pfanchri/Bachelorarbeit/Latex/Bachelorarbeit/Abschnitte/Anhang/Schaltplaene.tex

\section{Schaltpläne}
\label{app:Schematics}
Auf den folgenden Seiten sind die in Altium Designer erstellten Schaltpläne für alle Baugruppen der Basisstation dargestellt. Außerdem ist das \ac{PCB}-Layout der Basisstation abgebildet.

\includepdf[landscape, pages=-]{"../../Altium/mobile Basisstation/Project Outputs for mobile Basisstation/Basisstation Schematics"} 

\includepdf[landscape, pages=11]{"Abbildungen/Aufnahmen/SmartPDF/mobile Basisstation"}
