pfanchri/Bachelorarbeit/Präsentation/Präsentation PDF Export.pdf

# Au#au und Inbetriebnahme einer mobilen Basissta4on für feldstärkebasierte Lokalisierung

# Christof Pfannenmüller

07.10.2016

# Übersicht

# •Motivation •Anforderungen •Platinenlayout

# - Transceiver TDA 5340 - Mikrocontroller XMC4500

# •SoIwareentwurf •Datenausgabe und Tests

# Mo4va4on

# - ernergiesparende Lösung zur Lokalisierung - relative Ortung zu mobiler Basisstation - Anwendung innerhalb von Gebäuden - Sub-GHz-Band - Lokalisierung auf RSSI-Basis - Nutzung bereitgestellter Daten

# Anforderungen

# Anforderungen

# - sechs unabhängige Transceiver - Mikrocontroller zur Steuerung - Spannungsversorgung - Ausgabe ( USB & Ethernet ) - interruptbasierte Steuerung - Kommunikation über SPI-Interface

# Pla4nenlayout

# Mikrocontroller XMC4500

# - ARM® CortexTM-M4

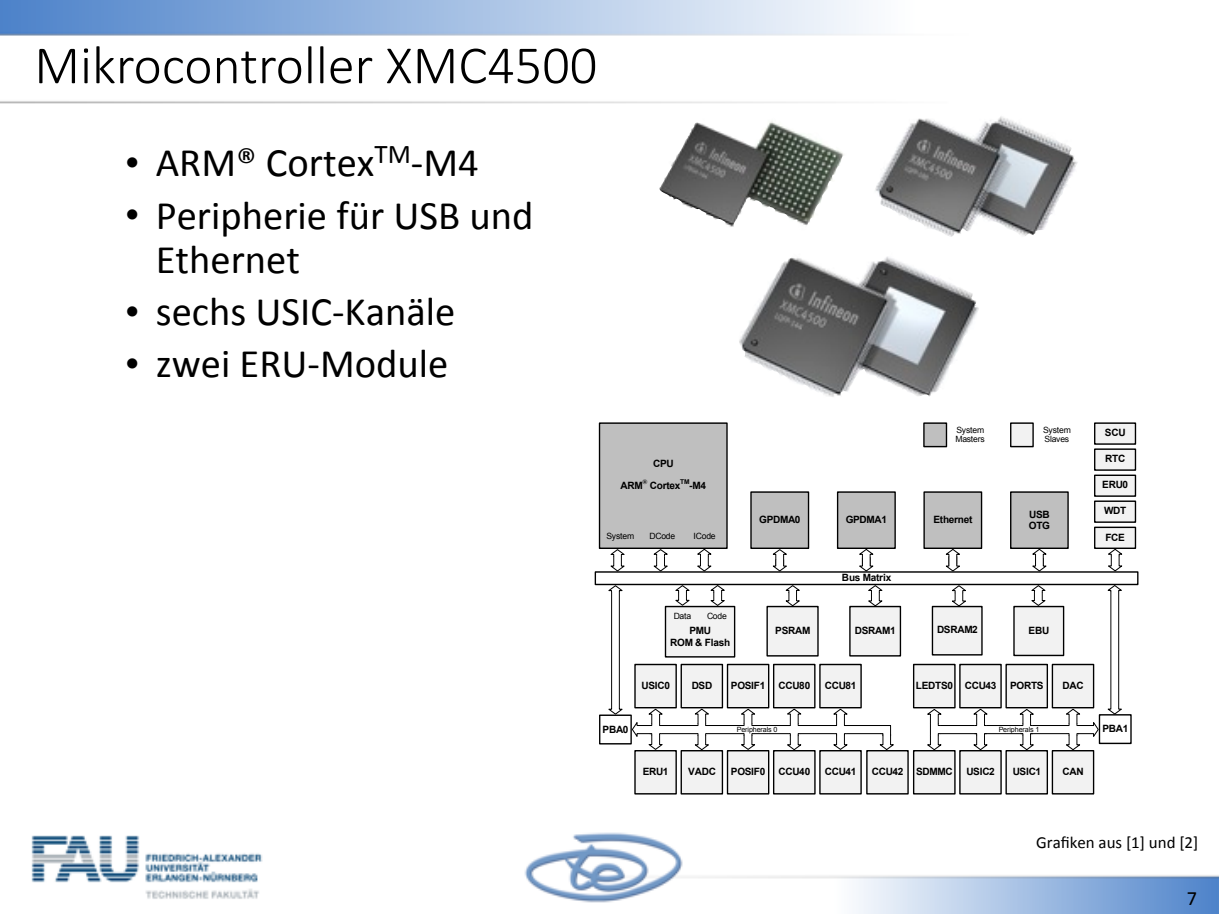
[picture p25: page 7]
PMU ROM & Flash; Bus Matrix; CPU; ARM® CortexTM-M4; PSRAM; DSRAM1; DSRAM2; EBU; FCE; GPDMA0; GPDMA1; USB; OTG Ethernet; System; ICode DCode; PBA0; Peripherals 0; Peripherals 1; Data; Code; WDT; RTC; ERU0; SCU; ERU1; VADC; POSIF0 CCU40; CCU41; CCU42; USIC0; DSD; POSIF1 CCU80; CCU81; LEDTS0 CCU43; PORTS; DAC; SDMMC; USIC2; USIC1; CAN; System Masters; System Slaves; PBA1

• Peripherie für USB und
Ethernet
• sechs USIC-Kanäle
• zwei ERU-Module

Grafiken aus [1] und [2]

# Schaltplan Mikrocontroller 1

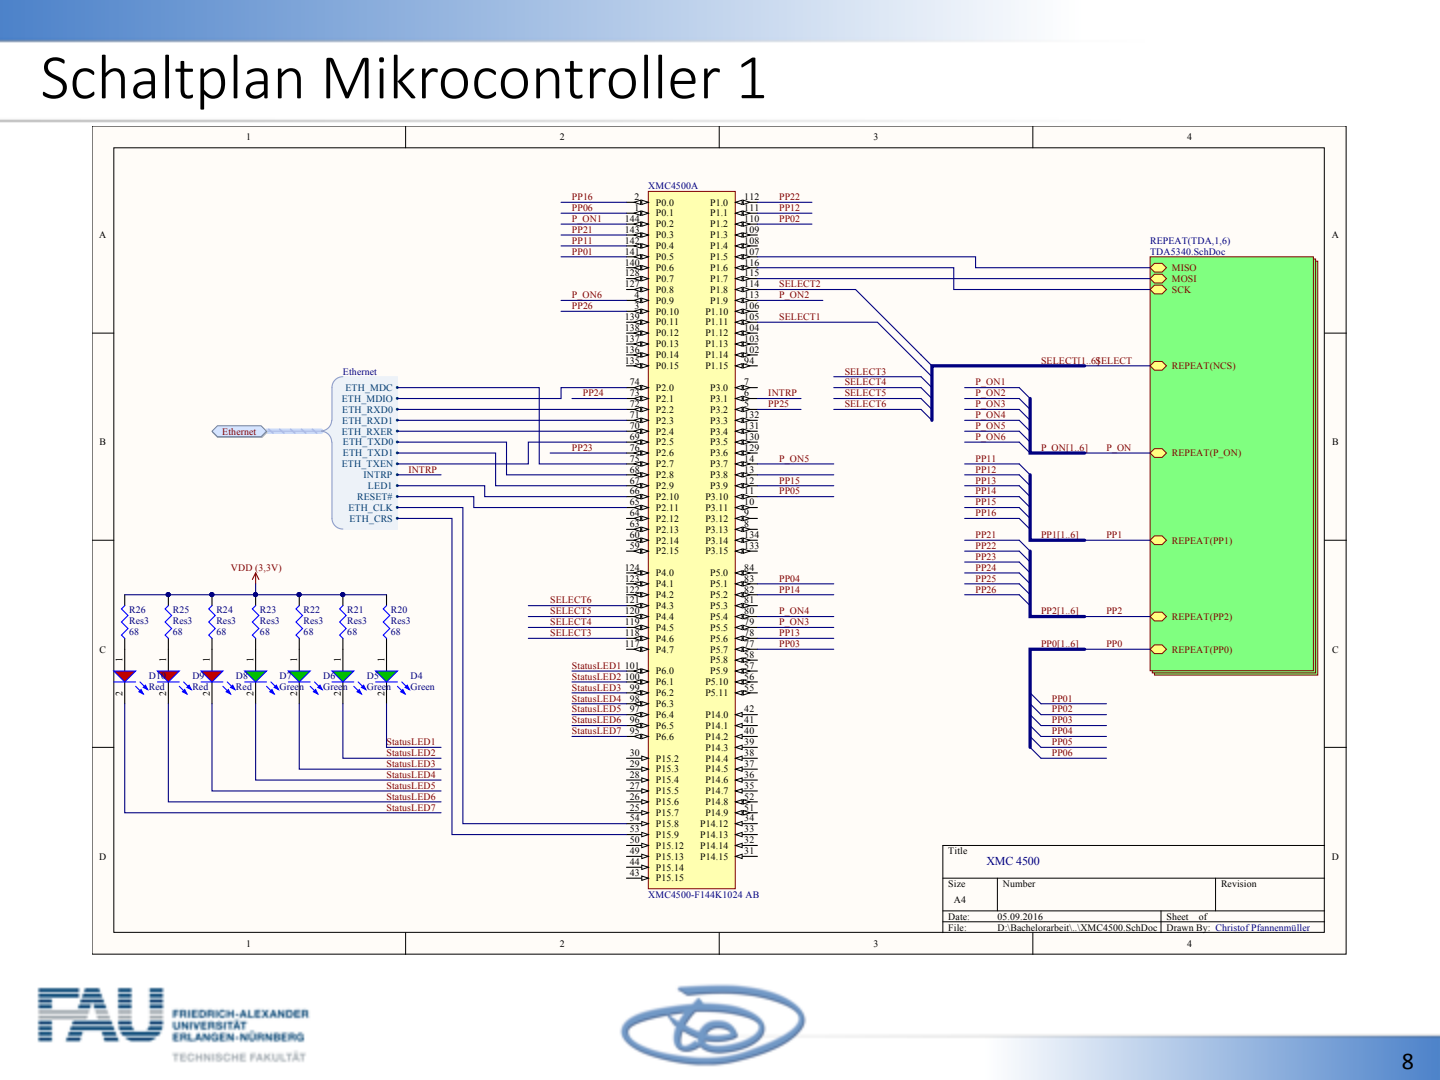
[picture p26: page 8]

# Schaltplan Mikrocontroller 2

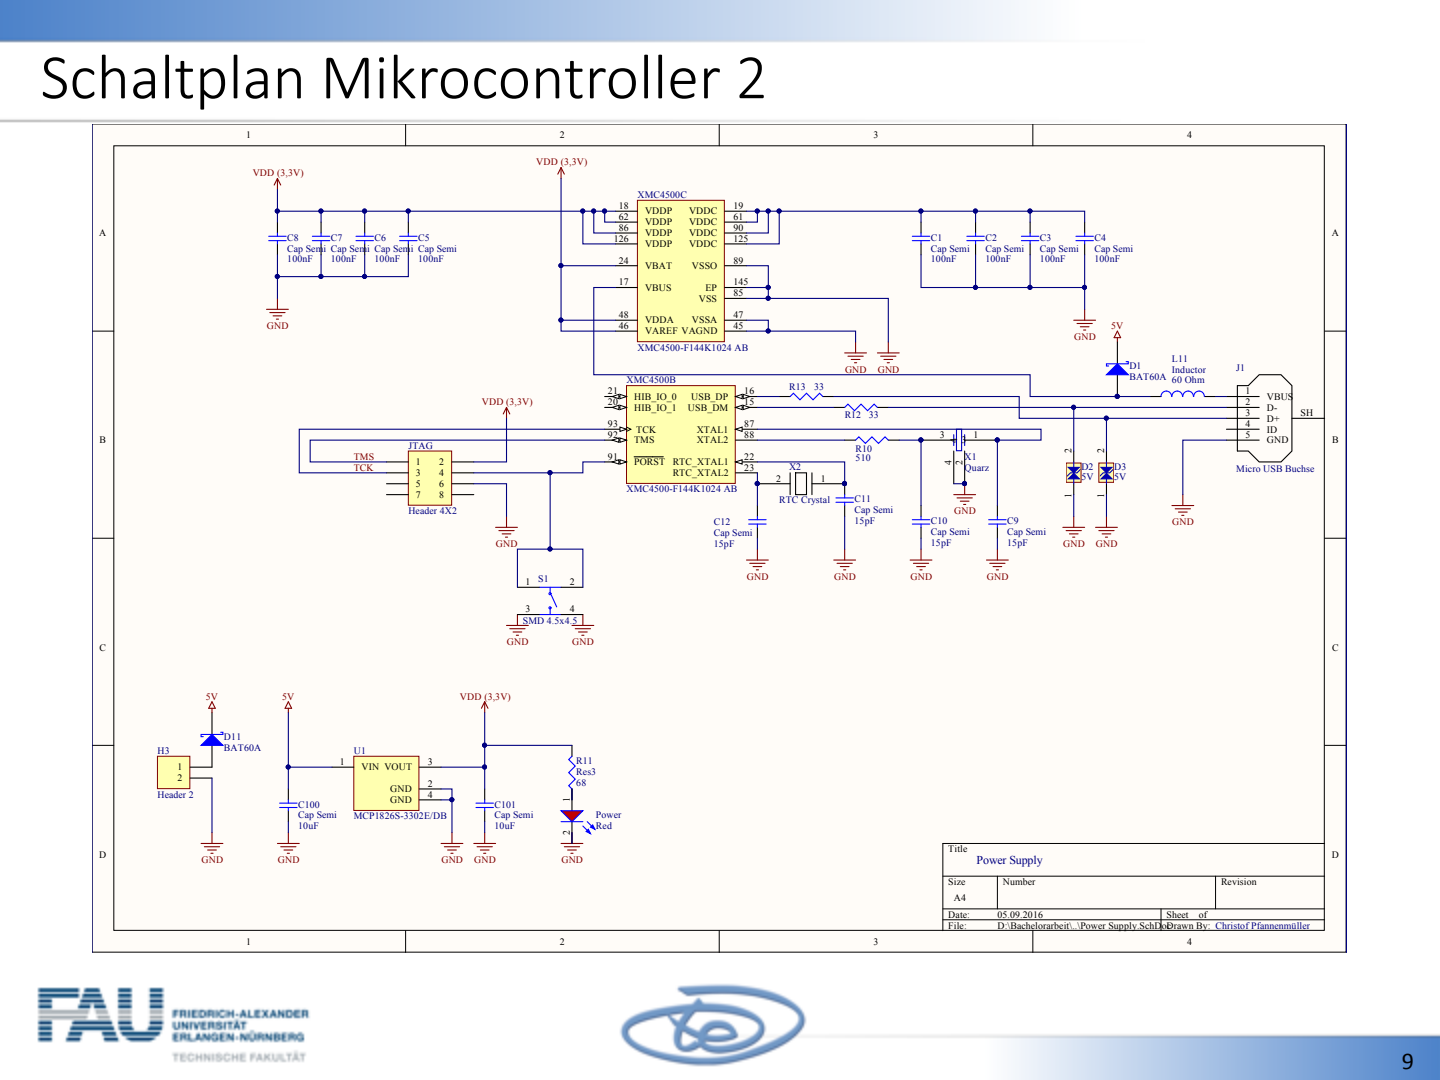
[picture p27: page 9]

# Transceiver TDA5340

# - Basisbanddemodulation

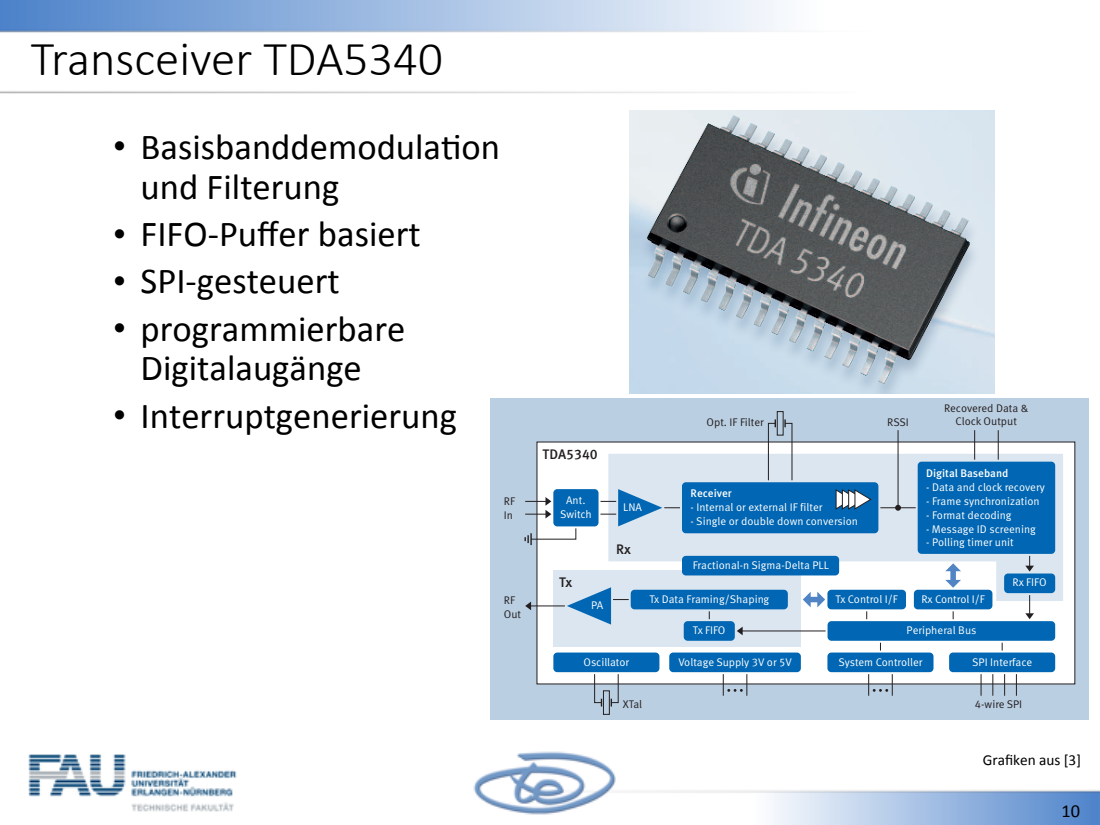
[picture p28: page 10]
Grafiken aus [3]; LNA; TDA5340; Ant. Switch; Rx FIFO; Tx FIFO; Peripheral Bus; Tx Data Framing/Shaping; Tx Control I/F; Oscillator; Voltage Supply 3V or 5V; System Controller; XTal; 4-wire SPI; Opt. IF Filter; RSSI; Recovered Data & Clock Output; RF Out; SPI Interface; Rx Control I/F

und Filterung
• FIFO-Puffer basiert
• SPI-gesteuert
• programmierbare
Digitalaugänge
• Interruptgenerierung

Digital Baseband
- Data and clock recovery
- Frame synchronization
- Format decoding
- Message ID screening
- Polling timer unit

Receiver
- Internal or external IF filter
- Single or double down conversion

Fractional-n Sigma-Delta PLL

# Schaltplan Transceiver

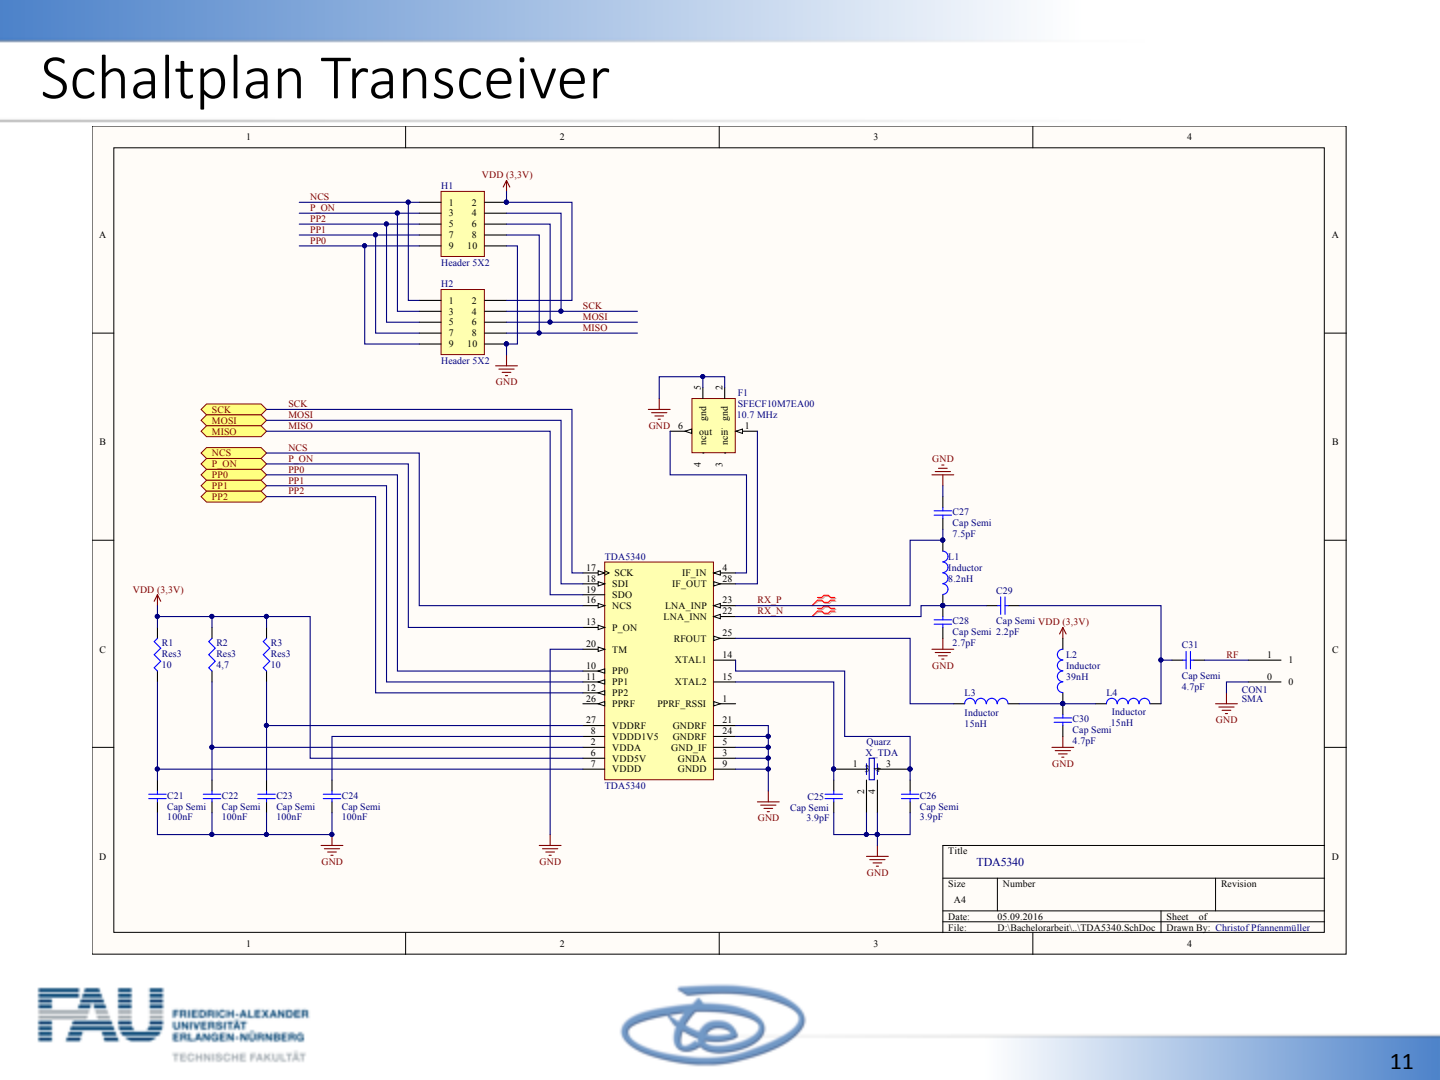
[picture p29: page 11]

# Layout Basissta4on

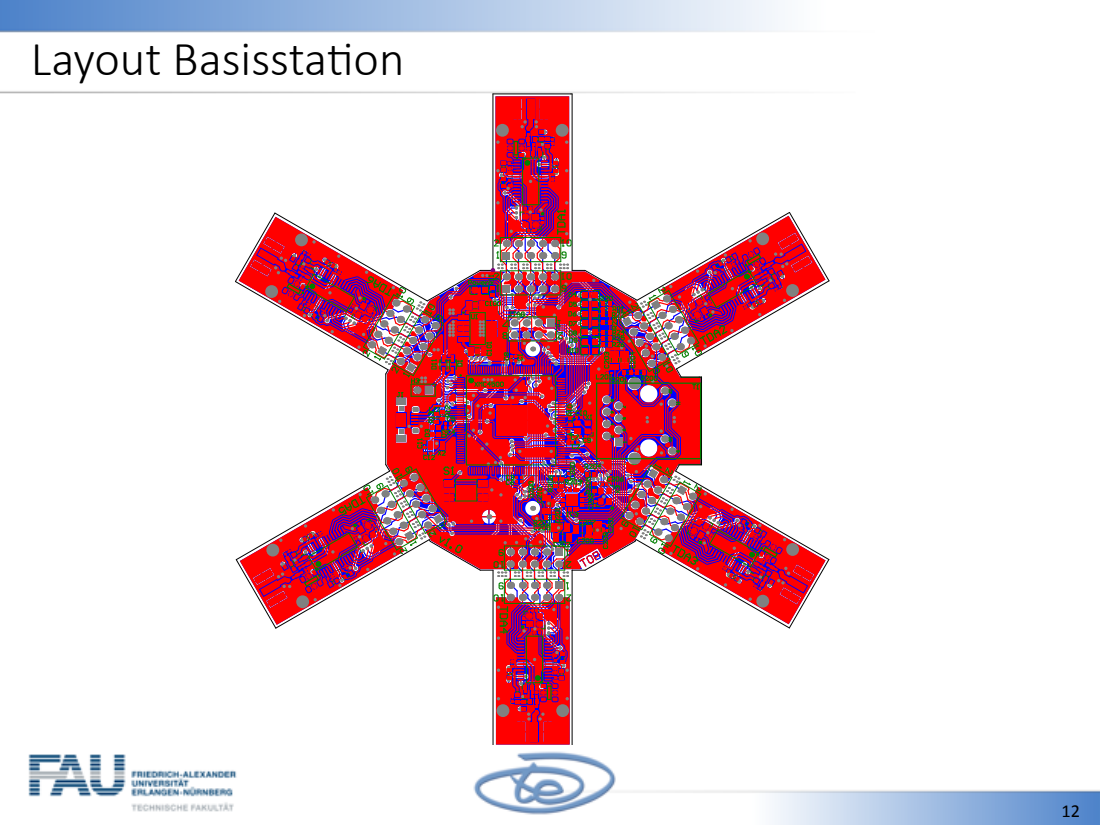
[picture p30: page 12]

# Layout XMC4500

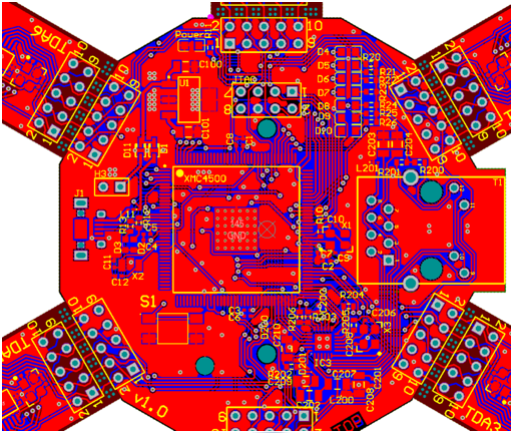
[picture p31: figure]

# Layout Transceiver

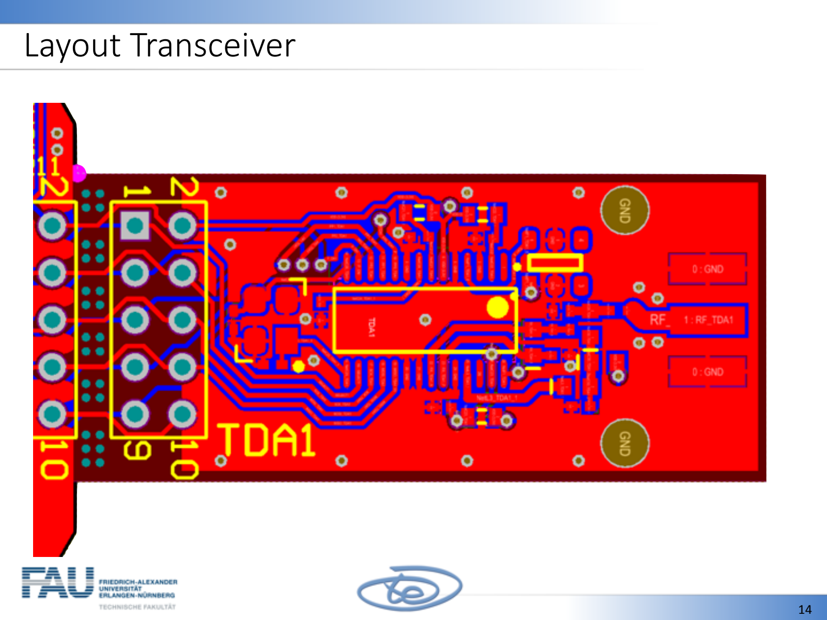
[picture p32: page 14]

# Bestückung

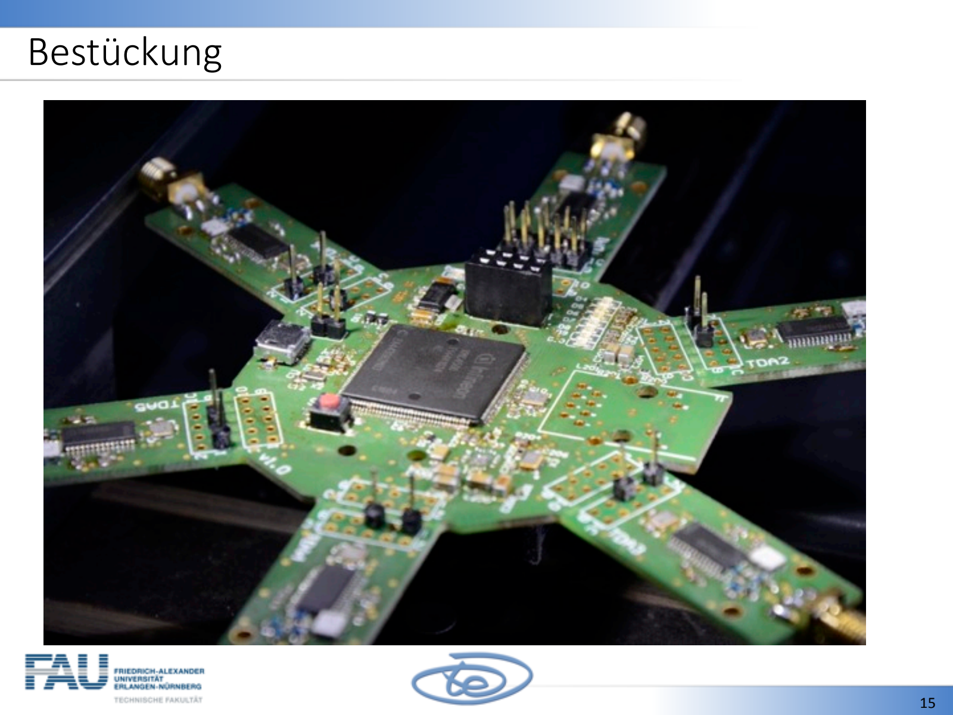
[picture p33: page 15]

# SoMwareentwurf

# Datenausgabe und Feldtest

# Vielen Dank für Ihre Aufmerksamkeit!

# Literatur

[1] P. Bauer, P. Schäfer und S. Zizala, New Infineon 32-bit Microcontroller Family XMC4000 for Industrial Applications Combines Powerful Application-optimized Peripherals and ARM CortexTM-M4 processor,

# Presseerklärung, 2012 [2] XMC4500 Data Sheet, Revison 1.3, Infineon Technologies AG, März 2014

[3] “SmartLEWISTM TRX – TDA5340 Mul9-Channel Transceiver for Sub 1GHz.” Produktbroschüre, April 2004.

# Au#au und Inbetriebnahme einer mobilen Basissta4on für feldstärkebasierte Lokalisierung

# Christof Pfannenmüller
