pfanchri/Bachelorarbeit/Latex/Bachelorarbeit/Abschnitte/Feldtest.tex

\chapter{Feldtest}
\label{sec:Feldtest}
\pagestyle{scrheadings}
\section{Aufbau}
Zur Evaluation der Basisstation wurde ein  XMC4500 Relax Kit von Infineon mit einem aufgesteckten Evaluations-Board für den TDA5340 betrieben. Mit Hilfe einer Powerbank konnte dieses mobil über den \ac{USB}-Anschluss des Relax Kits betrieben werden.
Dieses wurde auf eine Sendefrequenz von \unit[868,0]{MHz} und eine Empfangsfrequenz von \unit[867,999]{MHz} programmiert, was durch die Werte für die \ac{PLL} im TDA5340 eingestellt wurde. 
Die Basisstation wurde mit sechs Antennen bestückt, die einen Verstärkungsfaktor von \unit[3,6]{dBi} und eine Mittenfrequenz von \unit[868]{MHz} aufwiesen. Die Basis wurde über \ac{USB} an den Computer zur Auswertung angeschlossen. Das Auslesen der durch den virtuellen COM-Port übertragenen Daten erfolgte mit  PuTTY. Die Messungen fanden innerhalb des Gebäudes statt.

\section{Durchführung}
Es wurden  im selben Raum von diversen Positionen durch einen Tastendruck am Relax Kit eine Übertragung ausgelöst. Dabei wurde die zuvor einprogrammierte Zeichenkette $1,2,3,4,5,6,7,8,9$ ausgesendet. Der Abstand zur Basisstation betrug im ersten Test  \unit[3,30]{m} und wurde nach jeder Übertragung um \unit[30]{cm} verringert. 
In einem zweiten Test wurde ebenfalls mit einem Abstand von \unit[3,30]{m} gestartet.  Nach jeder Übertragung wurde der Sender \unit[30]{cm}  von der Startposition aus entlang einer  Linie rechtwinklig zur Sichtverbindung Startpunkt-Basis vom Relax Kit entfernt. Die gemessenen Werte wurden zur weiteren Auswertung abgespeichert.
In beiden Tests war die Basisstation so ausgerichtet, dass TDA1 in Richtung der gemeinsamen Startposition der Tests zeigte. Logic Analyser und Debugger waren während der Tests nicht an der Basisstation angeschlossen. So sollten Abschattungseffekte durch diese verhindert werden. Die Basisstation wurde auf einem \unit[70]{cm} hohen Tisch aufgestellt. Der Sender wurde auf gleicher Höhe freischwebend bewegt. Es wurden in beiden Tests zehn Messpunkte gesendet. Sowohl die Antennen an der Basisstation als auch jene am Relax Kit waren senkrecht nach oben zeigend ausgerichtet.
\begin{figure}[h]
\centering

\caption[Aufbau des Testszenarios]{Aufbau des ersten (rot) und des zweiten (blau) Feldtests der Basisstation. Transceiver TDA1 zeigt in Richtung des Startpunktes der beiden Feldtests}
\label{fig:aufbau-feldtest}
\end{figure}

\section{Ergebnisse und Auswertung}
Auffallend ist, dass zwar in jedem Test zehn Mal durch das Drücken des Tasters eine Übertragung ausgelöst wurde, jedoch öfter eine Übertragung an der Basisstation registriert wurde. Im ersten Feldtest wurden fünfzehn, im zweiten sogar sechzehn gültige Übertragungen von der Basisstation an den Hostcomputer weitergegeben. Beispielhafte Werte der Ausgabe sind in Tabelle \ref{tab:gemesseneWerte} zu erkennen, die gesamte Ausgabe der Konsole ist im  Anhang \ref{app:Feldtest} eingefügt. Darin ist zu erkennen, dass die Empfangsleistung mit abnehmendem Abstand des Senders ansteigt, wie es zu erwarten war.

\begin{table}
	\centering
	\begin{tabular}{c|ccccccc}
		Position & Start & 4 & 7 & 11 & 13 & 14 & 15 \\ 
		\hline
		TDA1 & -114 & -114 & -114 & -114 & -104 & -104 & -97 \\ 
		TDA2 & -110 & -37 & -50 & -33 & -32 & -32 & -32 \\ 
		TDA3 & -114 & -114 & -114 & -114 & -109 & -106 & -106 \\ 
		TDA4 & -110 & -35 & -33 & -36 & -36 & -31 & -31 \\ 
		TDA5 & -67 & -50 & -44 & -43 & -44 & -33 & -33 \\ 
		TDA6 & -59 & -58 & -58 & -55 & -48 & -43 & -43 \\ 
	\end{tabular} 
	\caption[Beispielhafte Empfangsleistungen des ersten Feldtests]{Empfangsleistungen für Übertragungen von ausgewählten Messpunkten des ersten Feldtests. In der ersten Zeile sind die durchnummerierten Positionen des Feldtests aufgeführt, an denen die jeweilige Messung durchgeführt wurde. Alle dargestellten Werte sind in dBm angegeben}
	\label{tab:gemesseneWerte}
\end{table}

Im ersten Test konnten bei der ersten Übertragung an den Transceivern eins bis vier keine Daten empfangen  werden. Erst in der darauffolgenden zweiten erkannten Übertragung wurde hier die gesendete Zahlenfolge empfangen. Bei der zweiten Übertragung, welche über die Konsole ausgegeben wurde, stimmten die Werte von TDA5 und TDA6 in allen ausgelesenen Registern mit den Messwerten der ersten Übertragung überein.  Daraus ist zu folgern, dass es sich bei diesen Werten noch um die Messungen aus dem ersten Transfer handelt. Somit wäre zu vermuten, dass durch eine leichte Verzögerung zwischen den TDA5340 der steuernde Mikrocontroller eine gemeinsame Übermittlung als zwei getrennte Übertragungen interpretiert hat.

Transceiver 1 konnte in dem Test erst ab der vierten Übertragung gültige Daten empfangen. Außerdem waren die gemessenen Empfangsleistungen stets geringer als \mbox{\unit[-100]{dBm}}, lediglich  bei der letzten Übertragung, welche bei einem Abstand von \unit[30]{cm} stattfand, konnte hier ein Wert von \unit[-97]{dBm} gemessen werden. Da diese  sehr schwachen Empfangsleistungen in vorherigen Tests nicht auftraten, ist zu vermuten, dass etwa eine nicht richtig verbundene Antenne  Grund der schwachen Empfangswerte war.

TDA3 konnte in keiner einzigen Übertragung passable Messwerte liefern. Die errechnete und ausgegebene Empfangsfeldstärke von \unit[-114]{dBm} entsprach dem minimal möglichen Ausgabewert der dafür verwendeten Funktion. Es ist also davon auszugehen, dass in diesem Transceiver nie eine Funkverbindung erkannt wurde. Gründe dafür wären ein Fehler im Anpassnetzwerk zwischen der Antenne und dem Transceiver oder ein Defekt des selbigen. Letzteres ist eher unwahrscheinlich, da eine Verbindung über \ac{SPI} mit dem \ac{IC} möglich war. Lediglich ein Teildefekt  in der RF-Sektion des Chips wäre also denkbar.
Daneben waren vereinzelt auch noch Übertragungen zu erkennen, in denen Registerwerte mit den Messungen aus den folgenden oder vorherigen Übertragungen übereinstimmten. Auch hier ist zu vermuten, das einzelne Transceiver eine Übertragung nicht erkennen konnten. 

Zu beachten ist, dass die vermeintlich doppelt ankommenden Übertragungen auch vom Sender ausgehen konnten. Es war nicht  sicher festzustellen, ob die mehrfache Ausgabe einer Übertragung durch die Basisstation  bedingt ist oder ob vom Relax Kit mehr als die gezählten Übertragungen versendet wurden. Das Versenden der Nachricht wurde an diesem durch einen Tastendruck ausgelöst.  Durch ein Prellen des Tasters könnten auch mehrfache, nur minimal verzögerte Übertragungen ausgelöst worden sein.
Für die Durchführung von nachfolgenden Tests wäre demnach ein Sicherstellen einer nur einmaligen Übertragung pro Tastendruck notwendig. Zusätzlich wäre die Ausgabe eines Zählers für die Übertragungen am Relax Kit und ein neuer zu sendender Datensatz für jede Übermittlung hilfreich.

Ein Abtrennen der Transceiver-Baugruppen und somit ein Vergrößern des Abstandes der Antennen war zur Verbesserung der Empfangsleistung nicht notwendig.
