pfanchri/Bachelorarbeit/Latex/Bachelorarbeit/Abschnitte/Anhang/3D.tex

\section{Gehäuse}
\label{app:Gehause}
Mit der Software SolidWorks wurde ein Gehäuse für die Platine erstellt. Dieses wurde anschließend mit einem 3D-Drucker aus Polylactide (PLA) ausgedruckt.
\begin{figure}[H]
\centering

\caption{Erstellte Box zum Schutz der Basisstation in der Software SolidWorks}
\label{fig:boxbildschirmsw}
\end{figure}
