pfanchri/Bachelorarbeit/Latex/Bachelorarbeit/Abschnitte/Anhang/Aufsteckboard.tex

\section{Layout Aufsteckboard TDA5340}
\label{app:Aufsteckboard}
Das Layout der Transceiver-Unterbaugruppen orientiert sich an dem Layout eines Aufsteckboards für den \enquote{XMC 2Go}, damit ein TDA5340 mit diesem verwendet werden kann. 

\begin{figure}[H] 
	\centering
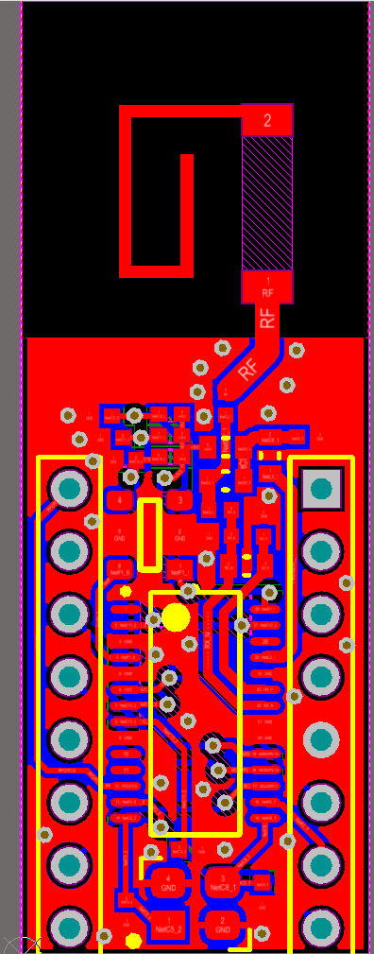
[picture p34: Latex/Bachelorarbeit/Abbildungen/Aufnahmen/Bilder/Altium/Layout_Stefan_Erhard/Layout.PNG]
	
	\caption{Layout des Aufsteckboards mit dem TDA5340}
	\label{fig:AufsteckboardTDA}
\end{figure}
