pfanchri/Bachelorarbeit/Latex/Bachelorarbeit/Abschnitte/Anhang/Seriennummern.tex

\section{Seriennummern}
\label{app:Seriennummern}
Alle TDA5340 verfügen über eine eingebaute Seriennummer, welche ausgelesen werden kann. Die Seriennummern der verwendeten TDA5340 sind in der Tabelle aufgeführt.
\begin{table}[H]
	\centering
	\begin{tabular}{cc}
		TDA & Seriennummer\\
		\hline
		TDA1 & 33020236\\
		TDA2 & 11727080\\
		TDA3& 11545236\\
		TDA4& 11728870\\
		TDA5& 11550773\\
		TDA6& 33026263\\
	\end{tabular}
	\caption{Seriennummern der im Projekt verwendeten TDA5340 }
	\label{default}
\end{table}
