pfanchri/Bachelorarbeit/Präsentation/LTE-Vorlagen/Latex/Presentation.pdf

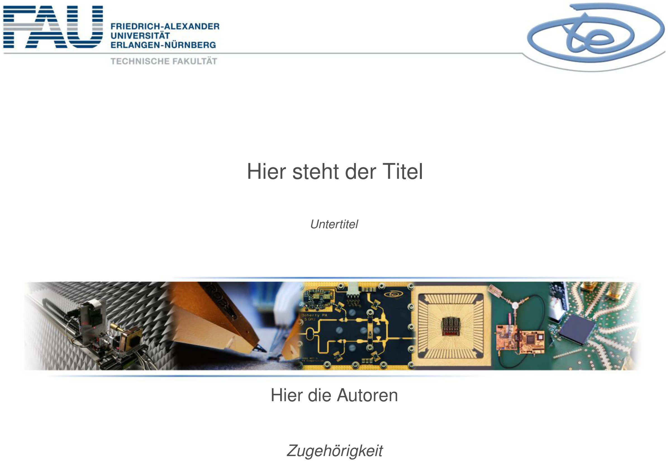
[picture p35: page 1]

Hier steht der Titel

Untertitel

Hier die Autoren

Zugehörigkeit

## Übersicht/Content

1 | First Section
2 | Second Section Minipage Columns
3 | Third Section

## Übersicht/Content

1 | First Section
2 | Second Section Minipage Columns
3 | Third Section

## Übersicht/Content

1 | First Section
2 | Second Section Minipage Columns
3 | Third Section

First Section

## Page with Title

First Section

Page without Title

Second Section | Minipage

## Minipage


Left side

Second Section | Columns

## Columns

Left side | Right side

Below
Listing:
First item
second item

Third Section

Auflistung
1 | Punkt 1
2 | Punkt 2
3 | Punkt 3

# Vielen Dank für Ihre Aufmerksamkeit!

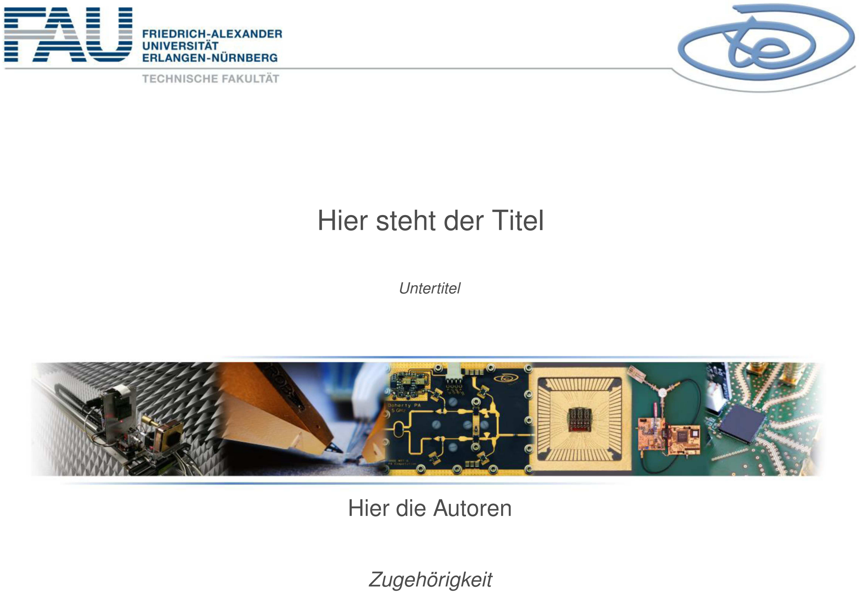
[picture p36: page 11]

Hier steht der Titel

Untertitel

Hier die Autoren

Zugehörigkeit
