pfanchri/Bachelorarbeit/Latex/Bachelorarbeit/Abbildungen/Logo/FAUlogo.pdf

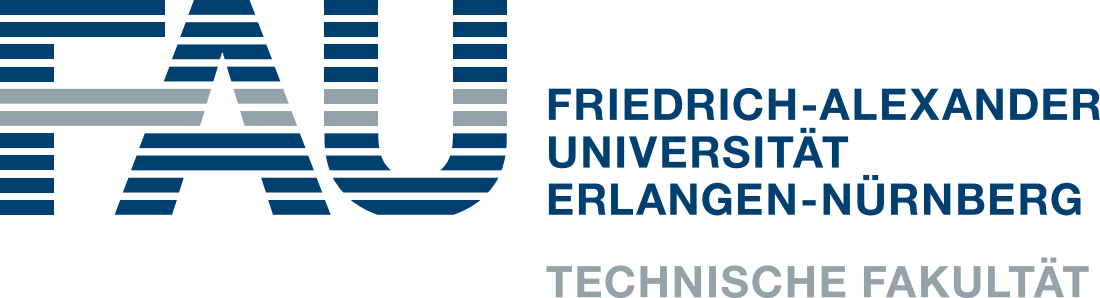
[picture p37: page 1]
