pfanchri/Bachelorarbeit/Präsentation/LTE-Vorlagen/Latex/graphics/theme/FAU.pdf

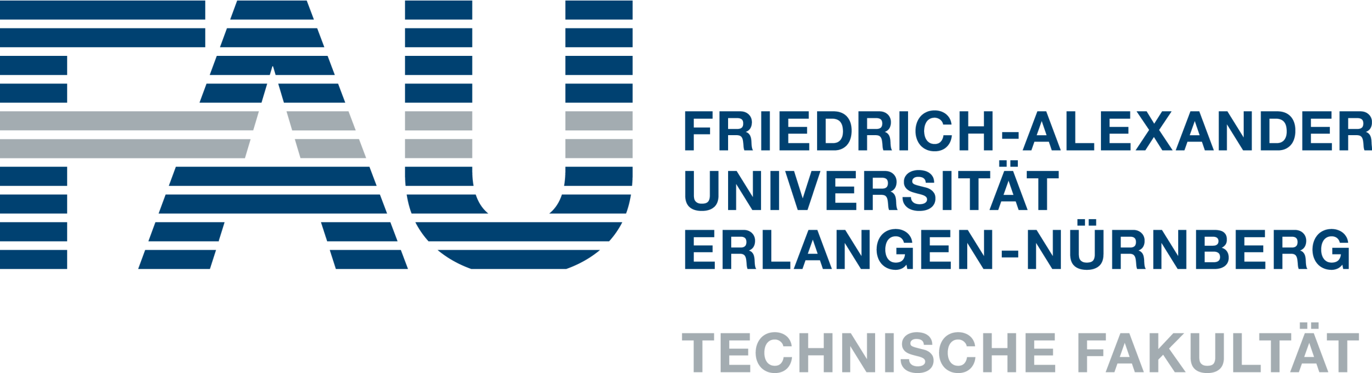
[picture p38: page 1]
