pfanchri/Bachelorarbeit/Präsentation/LTE-Vorlagen/Latex/graphics/theme/logo_oben2.pdf

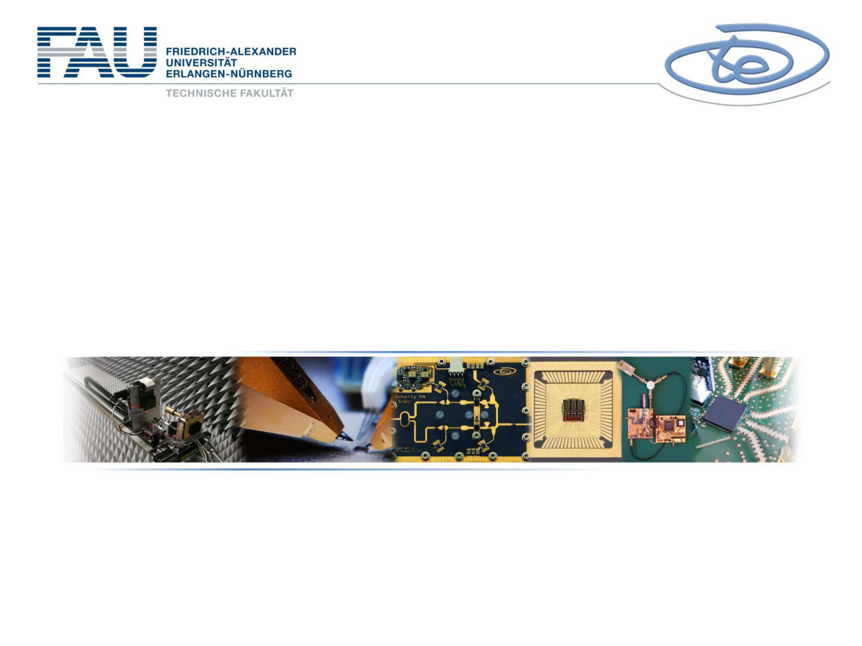
[picture p39: page 1]
