pfanchri/Bachelorarbeit/Präsentation/LTE-Vorlagen/Latex/graphics/theme/logoLTE.pdf

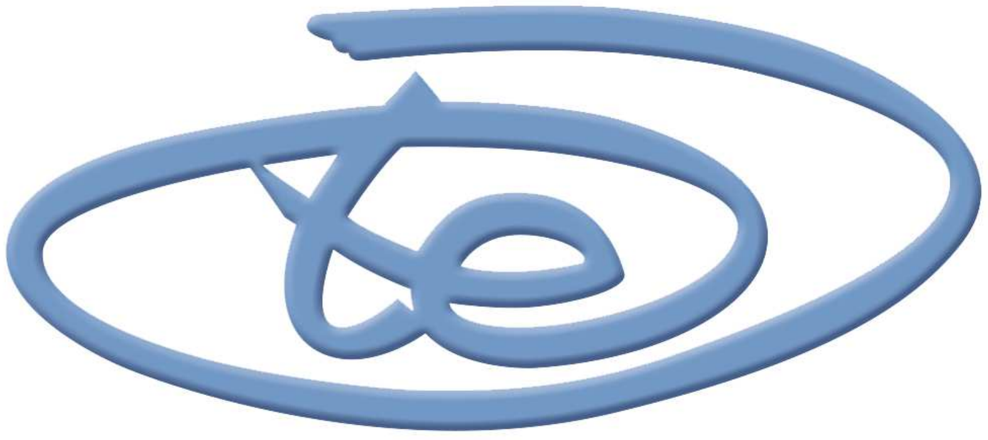
[picture p40: page 1]
