pfanchri/Bachelorarbeit/Latex/Bachelorarbeit/Abbildungen/Aufnahmen/Bilder/Altium/3D3.PNG

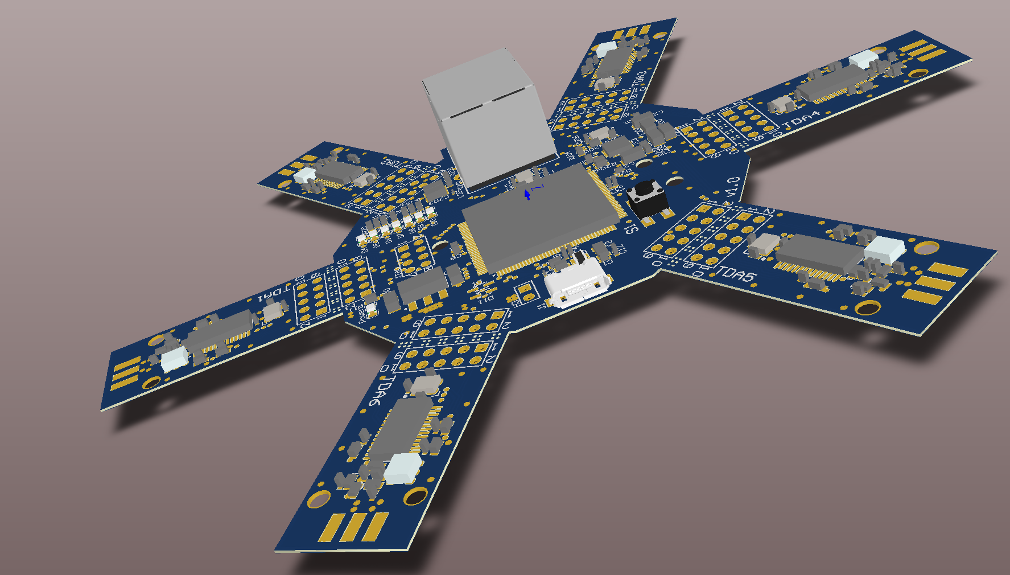
Latex/Bachelorarbeit/Abbildungen/Aufnahmen/Bilder/Altium/3D3.PNG
