pfanchri/Bachelorarbeit/Latex/Bachelorarbeit/Abbildungen/Aufnahmen/Bilder/Altium/3D4.PNG

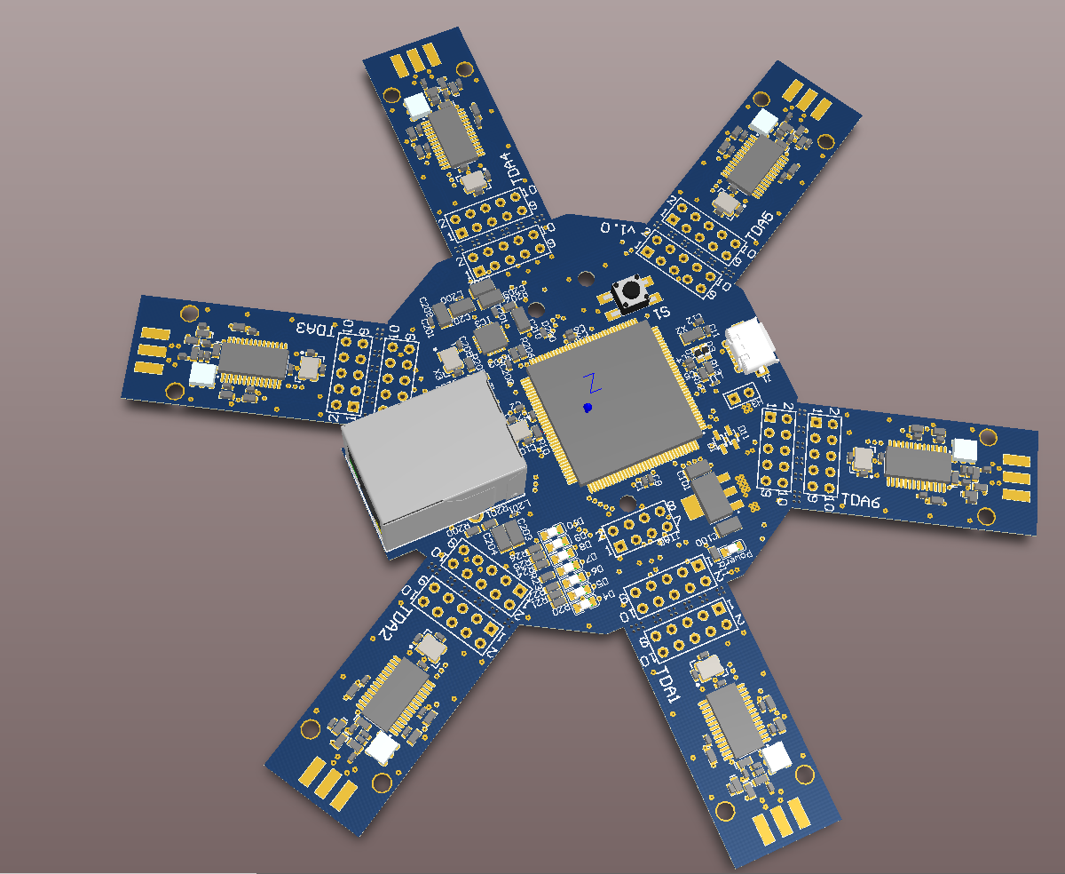
Latex/Bachelorarbeit/Abbildungen/Aufnahmen/Bilder/Altium/3D4.PNG
