pfanchri/Bachelorarbeit/Latex/Bachelorarbeit/Abbildungen/Aufnahmen/Bilder/Altium/3D.PNG

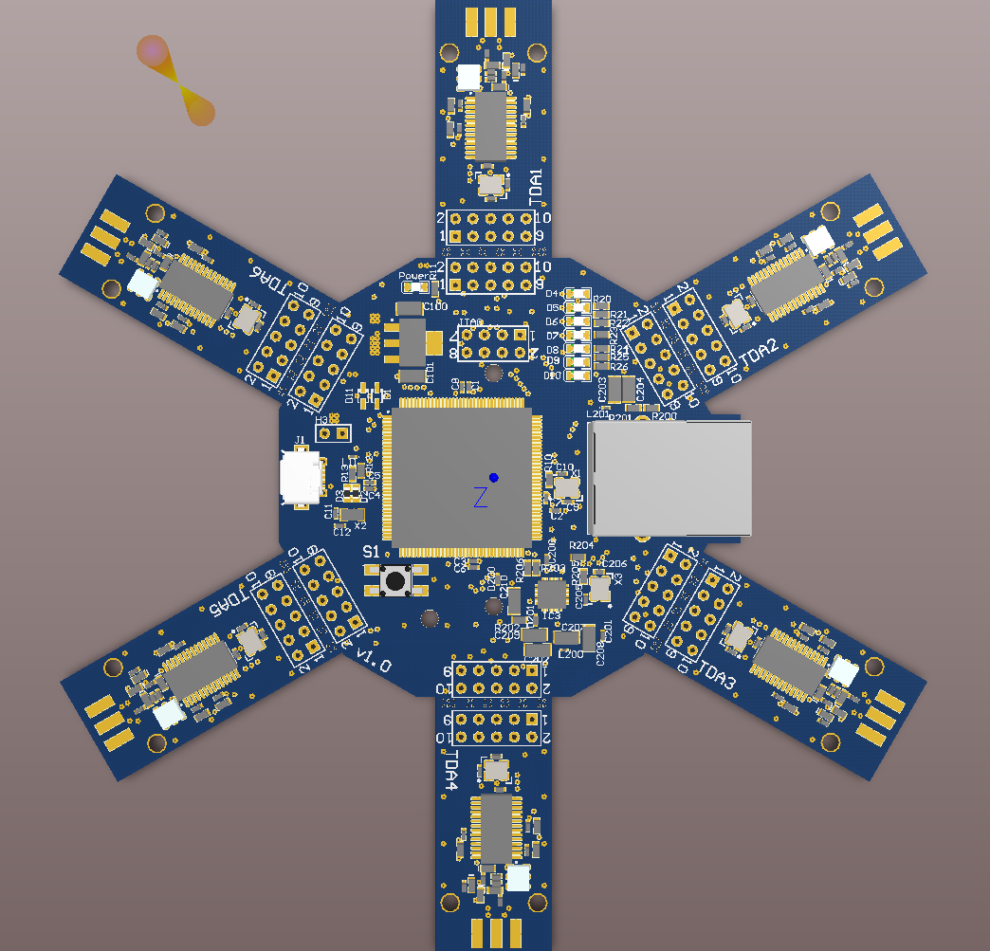
Latex/Bachelorarbeit/Abbildungen/Aufnahmen/Bilder/Altium/3D.PNG
