pfanchri/Bachelorarbeit/Latex/Bachelorarbeit/Abbildungen/Aufnahmen/Bilder/Altium/Anpassnetzwerk.PNG

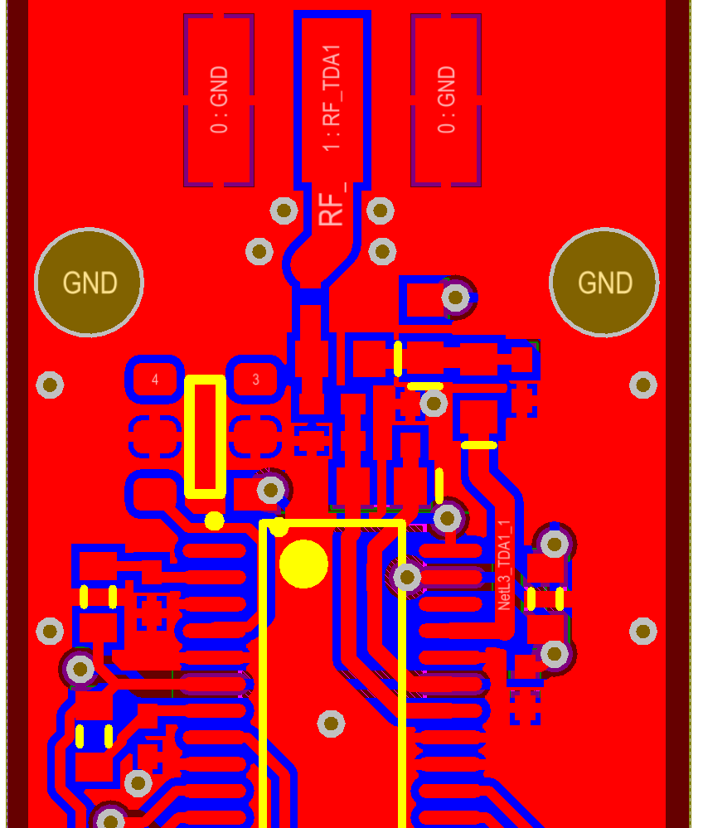
Latex/Bachelorarbeit/Abbildungen/Aufnahmen/Bilder/Altium/Anpassnetzwerk.PNG
