pfanchri/Bachelorarbeit/Latex/Bachelorarbeit/Abbildungen/Aufnahmen/Bilder/Altium/eigene PCB Library.PNG

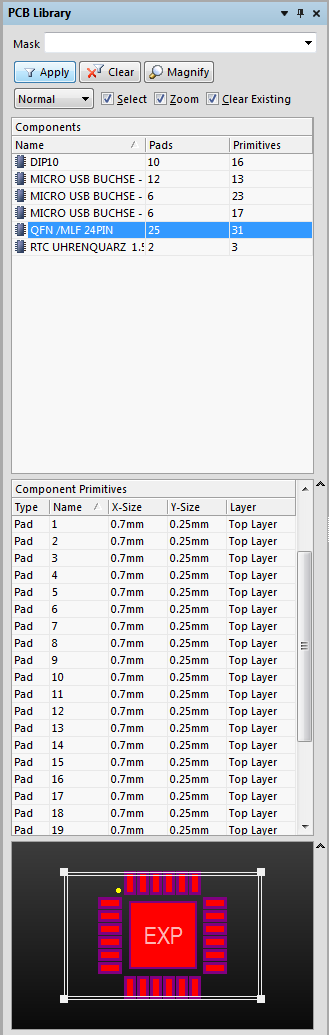
Latex/Bachelorarbeit/Abbildungen/Aufnahmen/Bilder/Altium/eigene PCB Library.PNG
