pfanchri/Bachelorarbeit/Latex/Bachelorarbeit/Abbildungen/Aufnahmen/Bilder/Altium/Gerber2.PNG

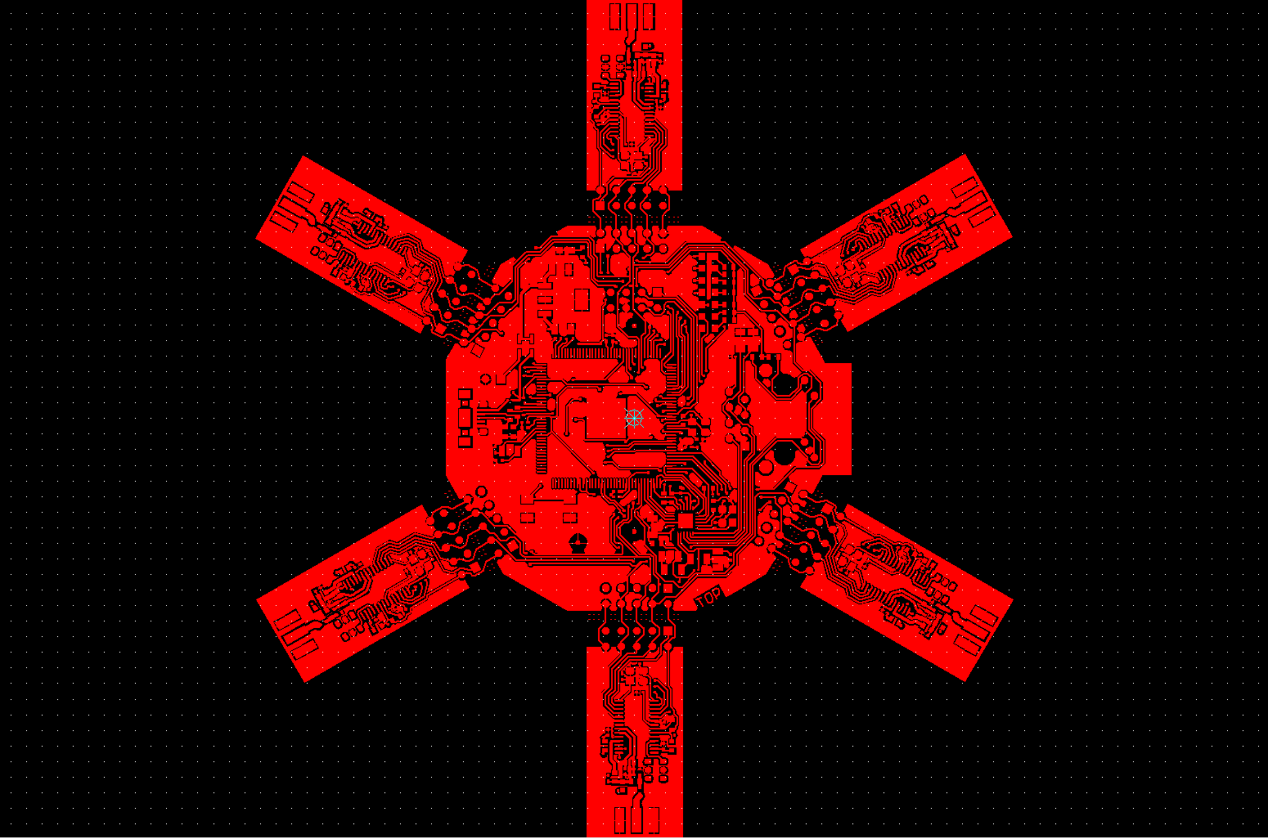
Latex/Bachelorarbeit/Abbildungen/Aufnahmen/Bilder/Altium/Gerber2.PNG
