pfanchri/Bachelorarbeit/Latex/Bachelorarbeit/Abbildungen/Aufnahmen/Bilder/Altium/Gerber.PNG

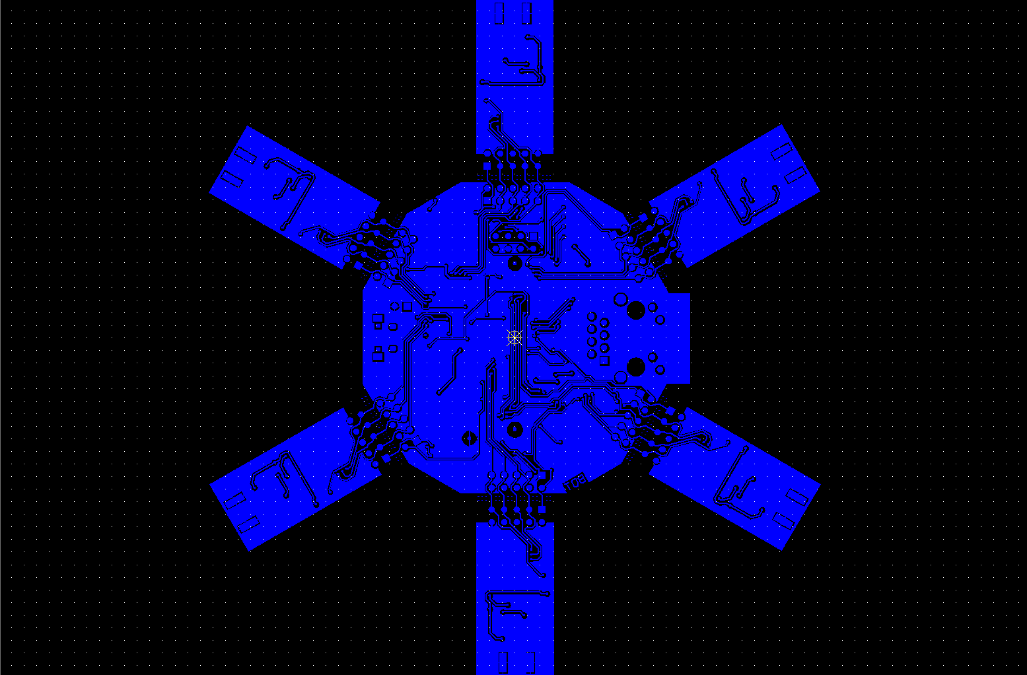
Latex/Bachelorarbeit/Abbildungen/Aufnahmen/Bilder/Altium/Gerber.PNG
