pfanchri/Bachelorarbeit/Latex/Bachelorarbeit/Abbildungen/Aufnahmen/Bilder/Altium/Header.PNG

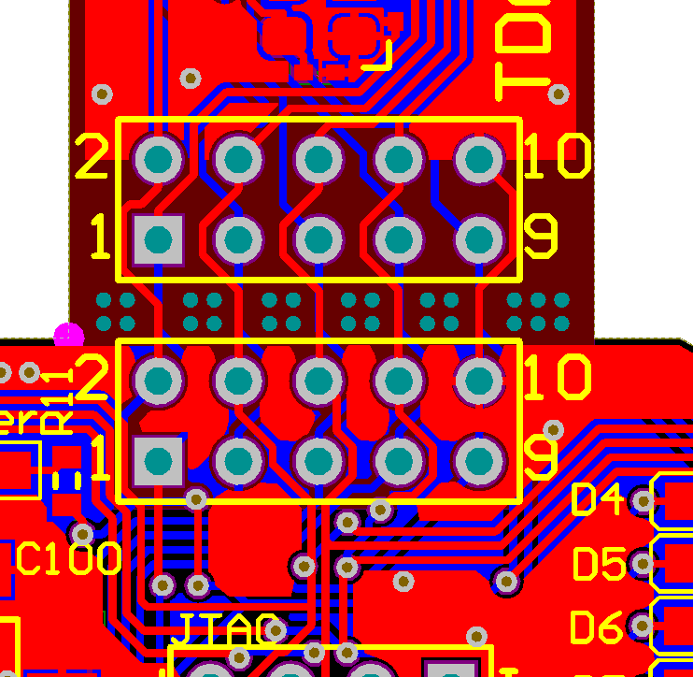
Latex/Bachelorarbeit/Abbildungen/Aufnahmen/Bilder/Altium/Header.PNG
