pfanchri/Bachelorarbeit/Latex/Bachelorarbeit/Abbildungen/Aufnahmen/Bilder/Altium/Layout_Stefan_Erhard/Antenne.PNG

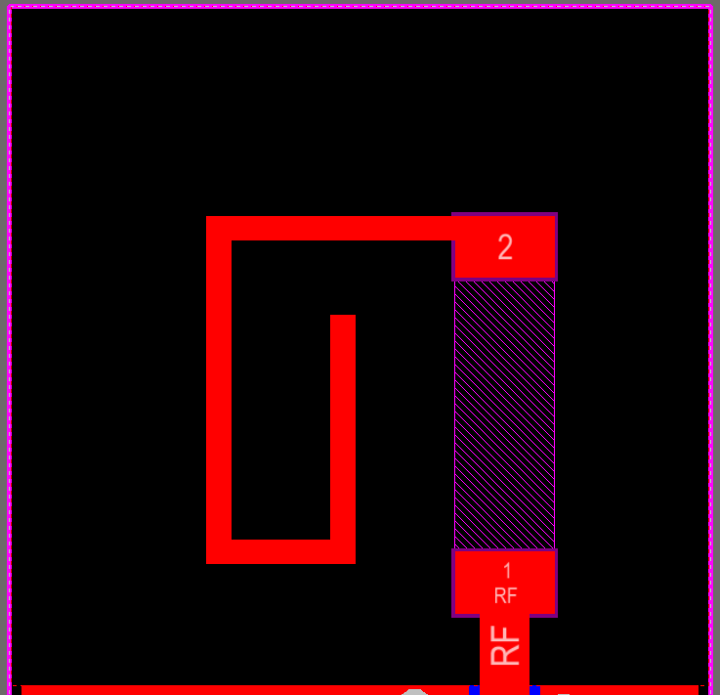
Latex/Bachelorarbeit/Abbildungen/Aufnahmen/Bilder/Altium/Layout_Stefan_Erhard/Antenne.PNG
