pfanchri/Bachelorarbeit/Latex/Bachelorarbeit/Abbildungen/Aufnahmen/Bilder/Altium/PCB2.PNG

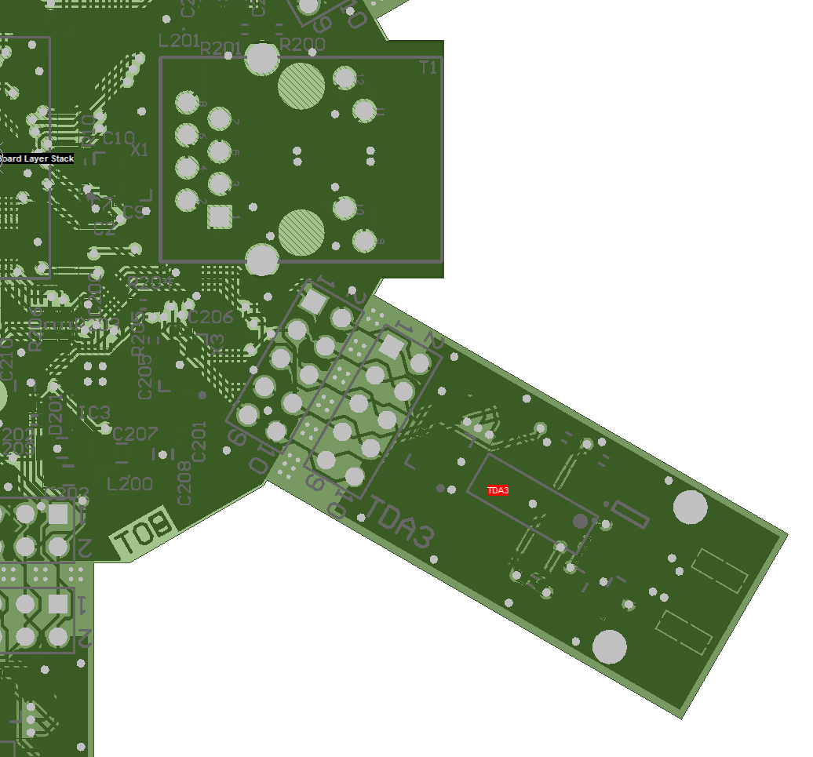
Latex/Bachelorarbeit/Abbildungen/Aufnahmen/Bilder/Altium/PCB2.PNG
