pfanchri/Bachelorarbeit/Latex/Bachelorarbeit/Abbildungen/Aufnahmen/Bilder/Altium/PCB.PNG

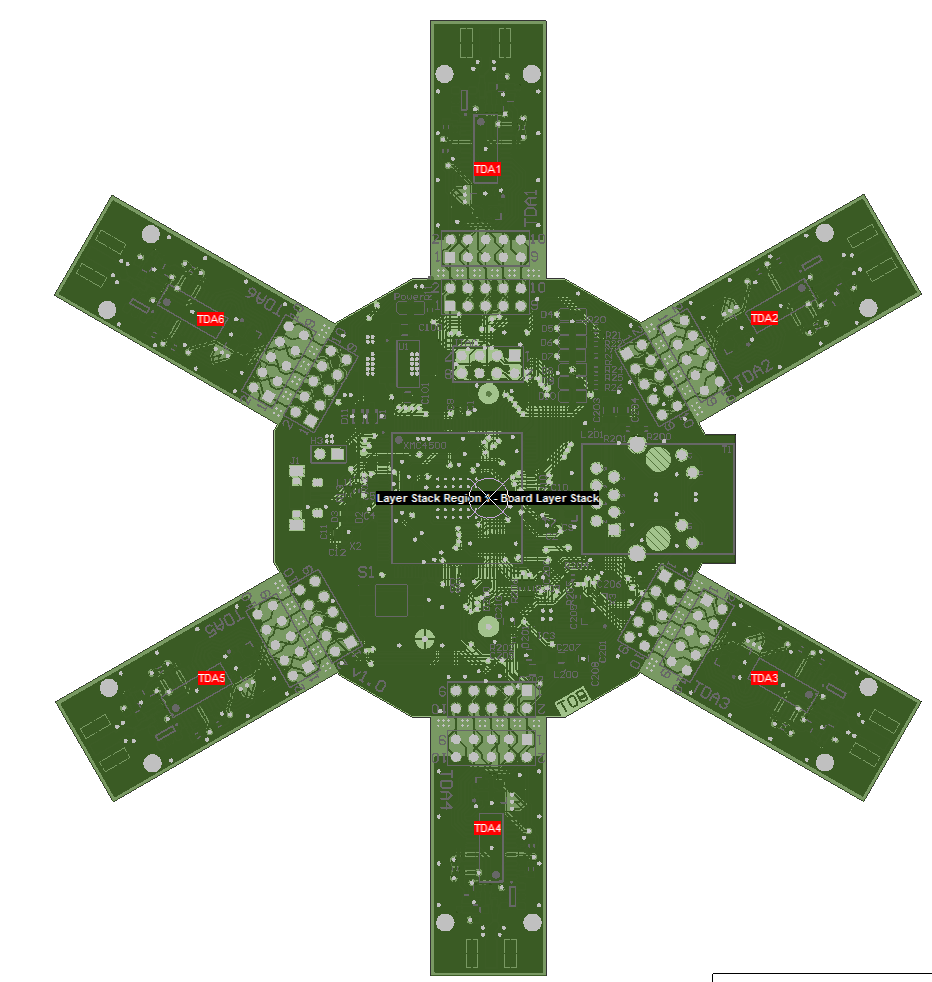
Latex/Bachelorarbeit/Abbildungen/Aufnahmen/Bilder/Altium/PCB.PNG
