pfanchri/Bachelorarbeit/Latex/Bachelorarbeit/Abbildungen/Aufnahmen/Bilder/Altium/PowerSupply.PNG

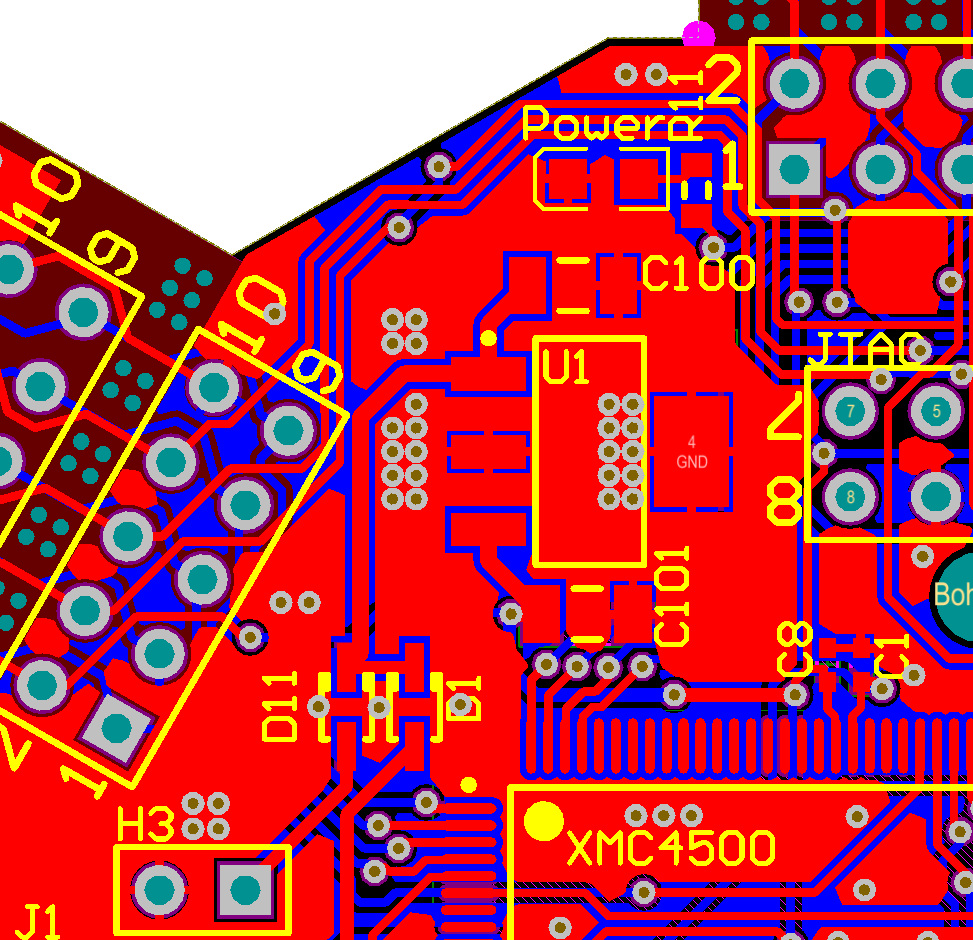
Latex/Bachelorarbeit/Abbildungen/Aufnahmen/Bilder/Altium/PowerSupply.PNG
