pfanchri/Bachelorarbeit/Latex/Bachelorarbeit/Abbildungen/Aufnahmen/Bilder/Altium/QFN Package.PNG

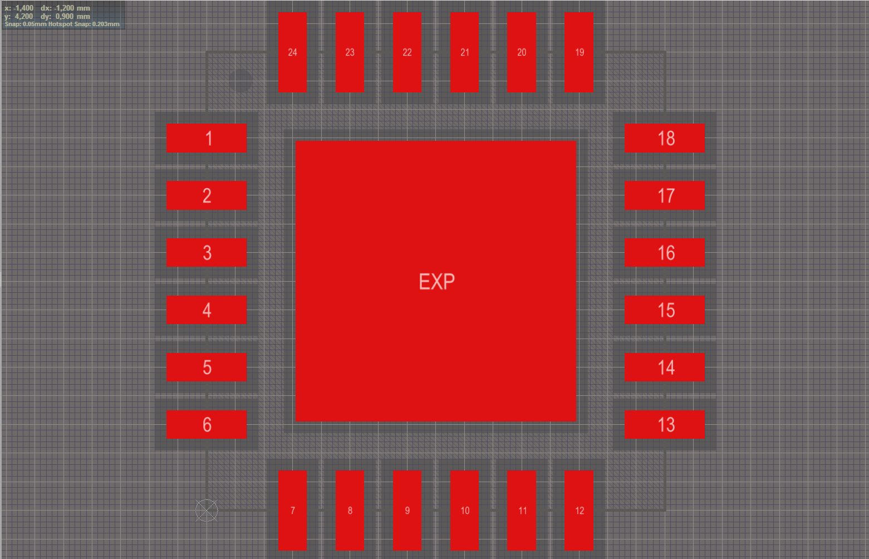
Latex/Bachelorarbeit/Abbildungen/Aufnahmen/Bilder/Altium/QFN Package.PNG
