pfanchri/Bachelorarbeit/Latex/Bachelorarbeit/Abbildungen/Aufnahmen/Bilder/Altium/TDA2.PNG

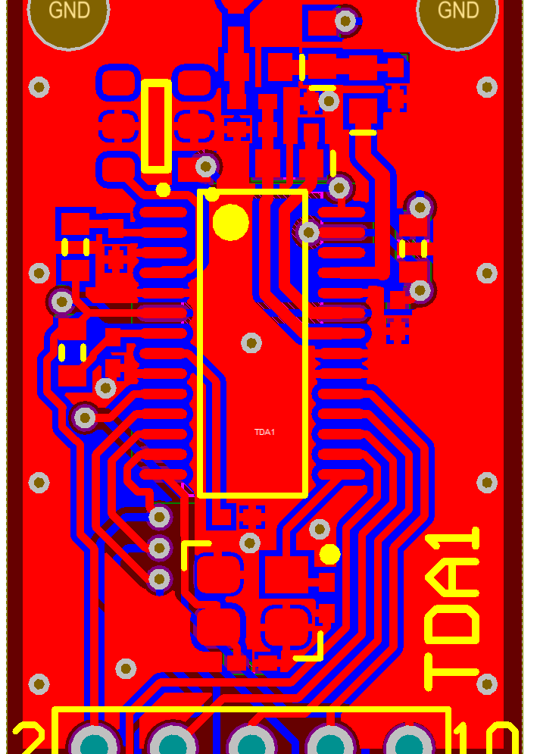
Latex/Bachelorarbeit/Abbildungen/Aufnahmen/Bilder/Altium/TDA2.PNG
