pfanchri/Bachelorarbeit/Latex/Bachelorarbeit/Abbildungen/Aufnahmen/Bilder/Altium/TDA.PNG

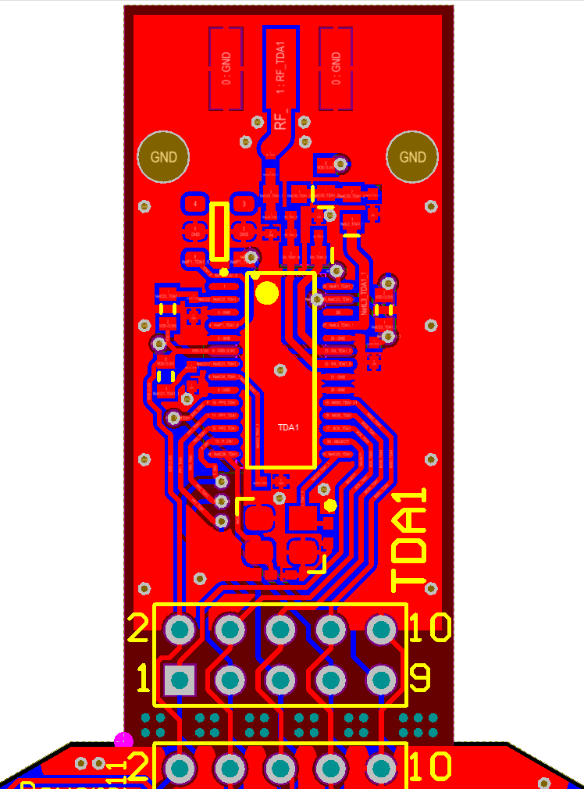
Latex/Bachelorarbeit/Abbildungen/Aufnahmen/Bilder/Altium/TDA.PNG
