pfanchri/Bachelorarbeit/Latex/Bachelorarbeit/Abbildungen/Aufnahmen/Bilder/Altium/USB und XMC.PNG

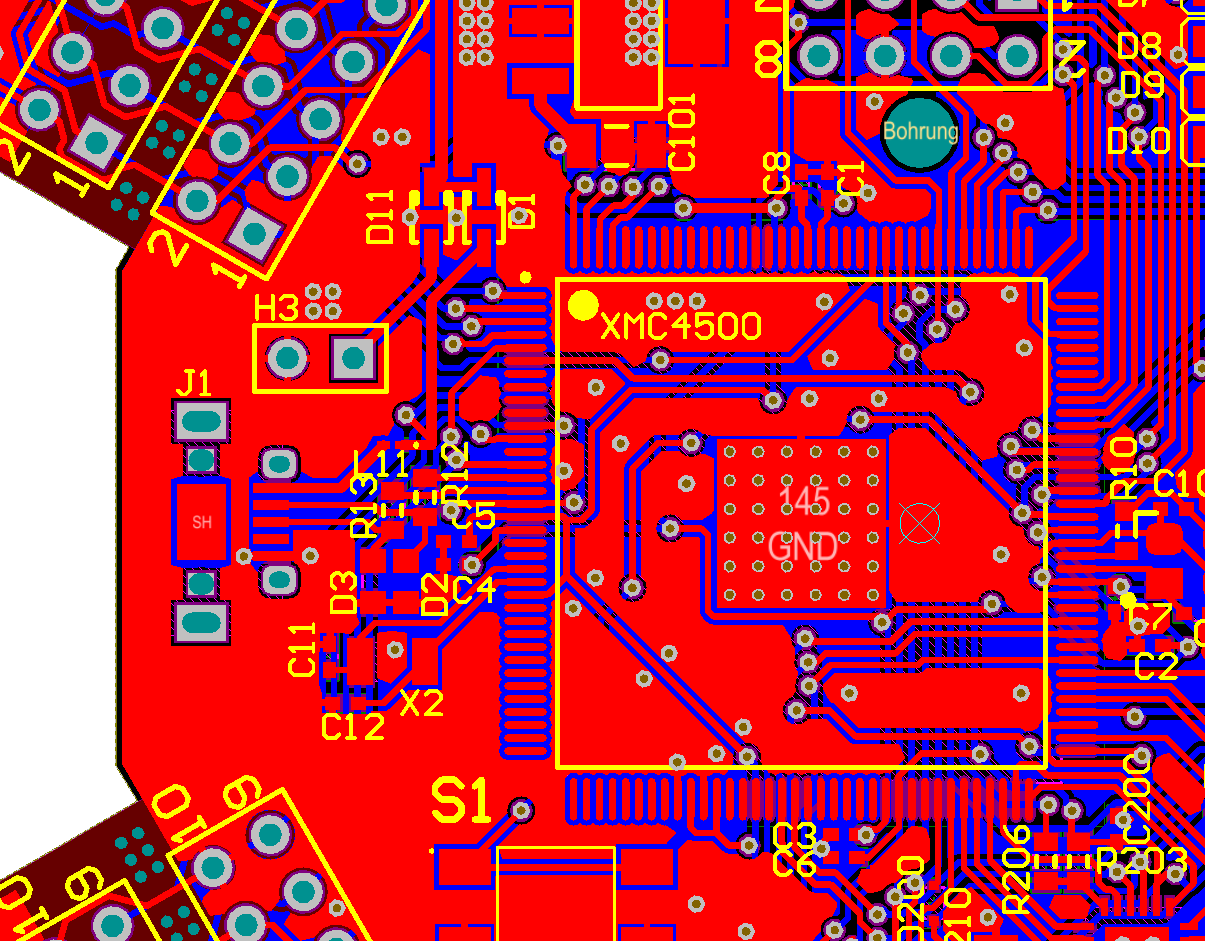
Latex/Bachelorarbeit/Abbildungen/Aufnahmen/Bilder/Altium/USB und XMC.PNG
