pfanchri/Bachelorarbeit/Latex/Bachelorarbeit/Abbildungen/Aufnahmen/Bilder/Dave/Dave Apps.PNG

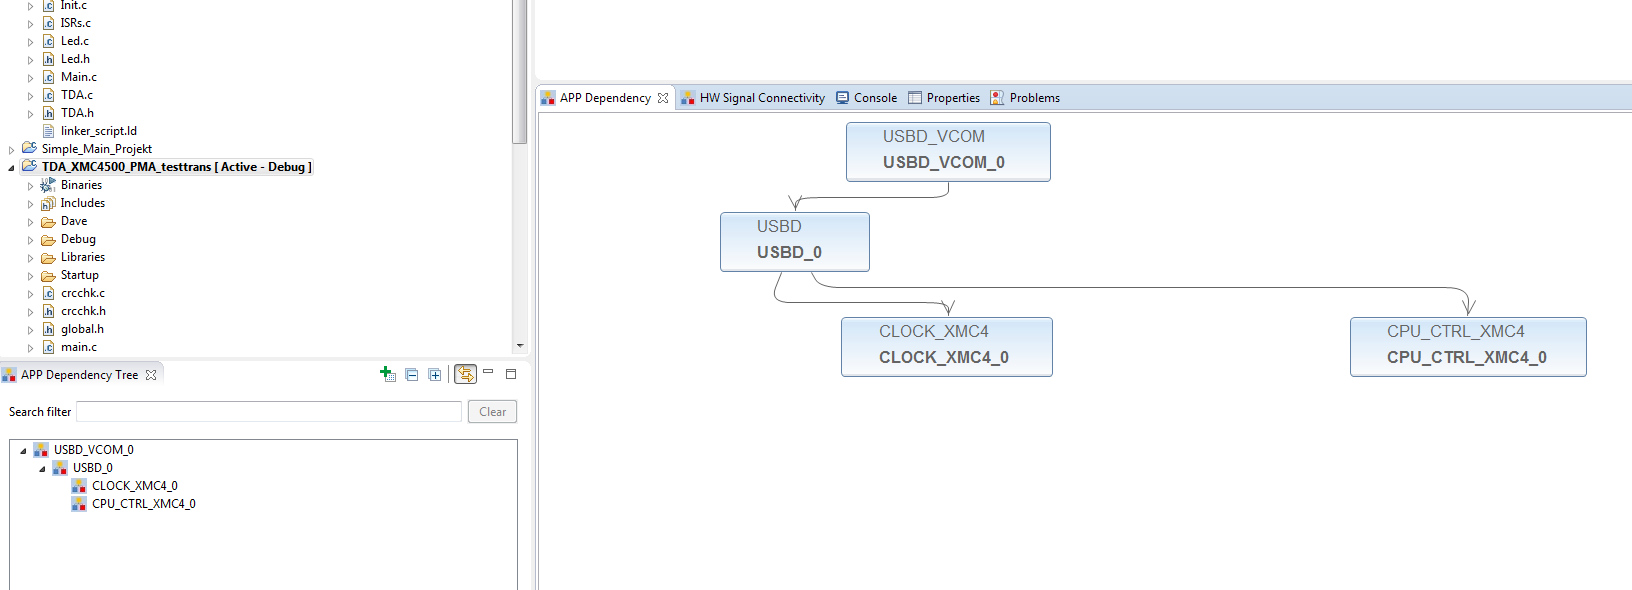
Latex/Bachelorarbeit/Abbildungen/Aufnahmen/Bilder/Dave/Dave Apps.PNG
