pfanchri/Bachelorarbeit/Latex/Bachelorarbeit/Abbildungen/Aufnahmen/Bilder/Dave/Projektexplorrer.PNG

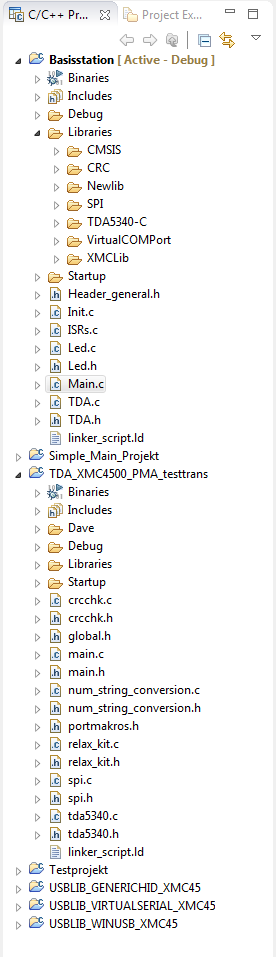
Latex/Bachelorarbeit/Abbildungen/Aufnahmen/Bilder/Dave/Projektexplorrer.PNG
