pfanchri/Bachelorarbeit/Latex/Bachelorarbeit/Abbildungen/Aufnahmen/Bilder/Dave/Übersicht.PNG

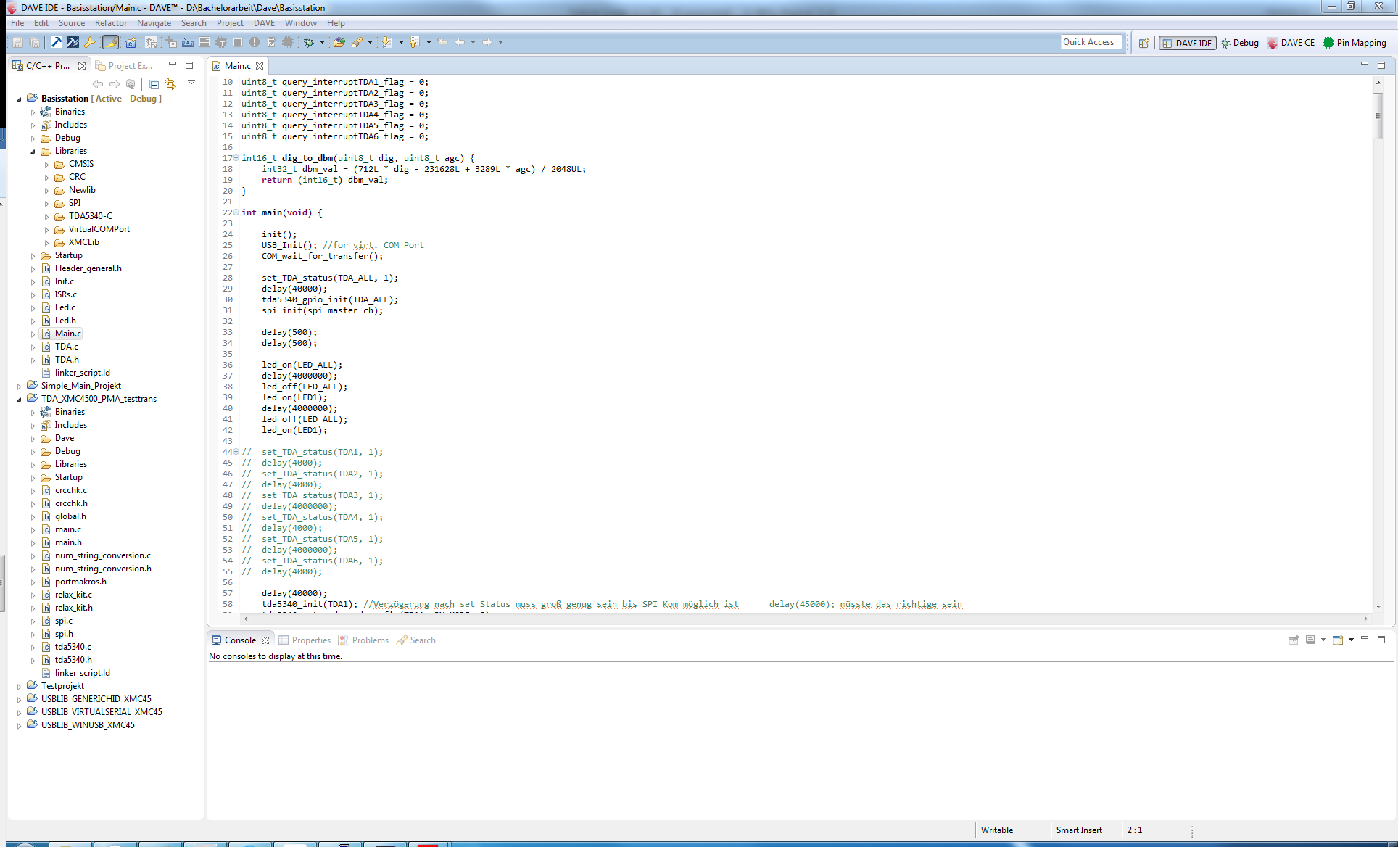
Latex/Bachelorarbeit/Abbildungen/Aufnahmen/Bilder/Dave/Übersicht.PNG
