pfanchri/Bachelorarbeit/Latex/Bachelorarbeit/Abbildungen/Aufnahmen/Bilder/Logic Analyser/AuftretenInterrupts.PNG

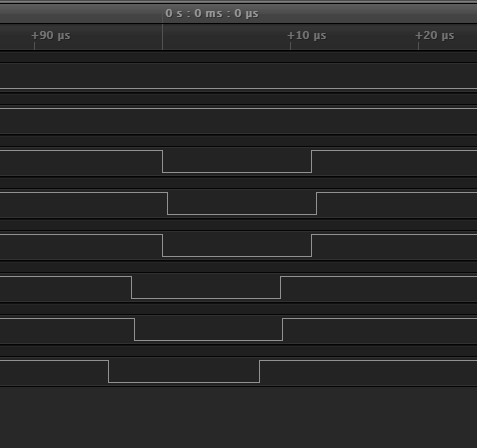
Latex/Bachelorarbeit/Abbildungen/Aufnahmen/Bilder/Logic Analyser/AuftretenInterrupts.PNG
