pfanchri/Bachelorarbeit/Latex/Bachelorarbeit/Abbildungen/Aufnahmen/Bilder/Logic Analyser/AuftretenInterruptsZeitmessung2.PNG

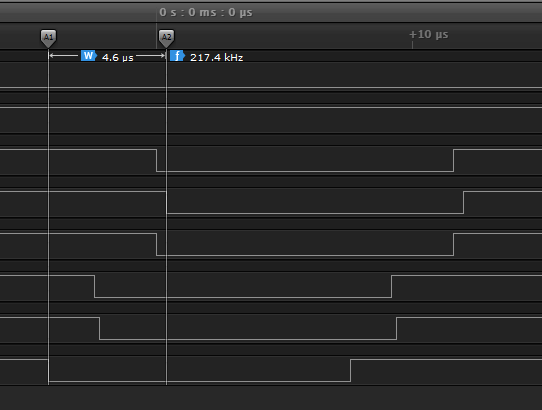
Latex/Bachelorarbeit/Abbildungen/Aufnahmen/Bilder/Logic Analyser/AuftretenInterruptsZeitmessung2.PNG
