pfanchri/Bachelorarbeit/Latex/Bachelorarbeit/Abbildungen/Aufnahmen/Bilder/Logic Analyser/AuftretenInterruptsZeitmessung.PNG

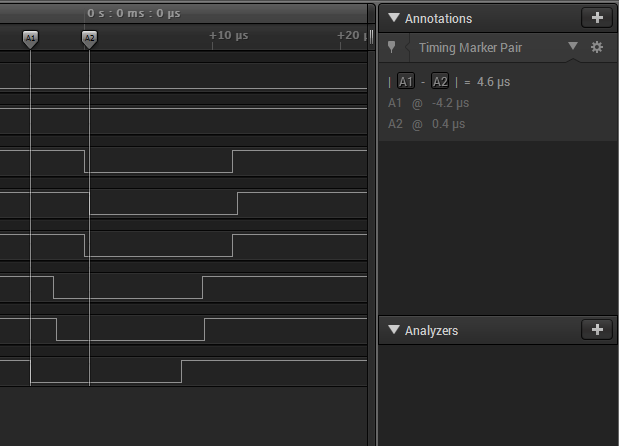
Latex/Bachelorarbeit/Abbildungen/Aufnahmen/Bilder/Logic Analyser/AuftretenInterruptsZeitmessung.PNG
