pfanchri/Bachelorarbeit/Latex/Bachelorarbeit/Abbildungen/Aufnahmen/Bilder/Logic Analyser/SPI_Interrupt_messung.PNG

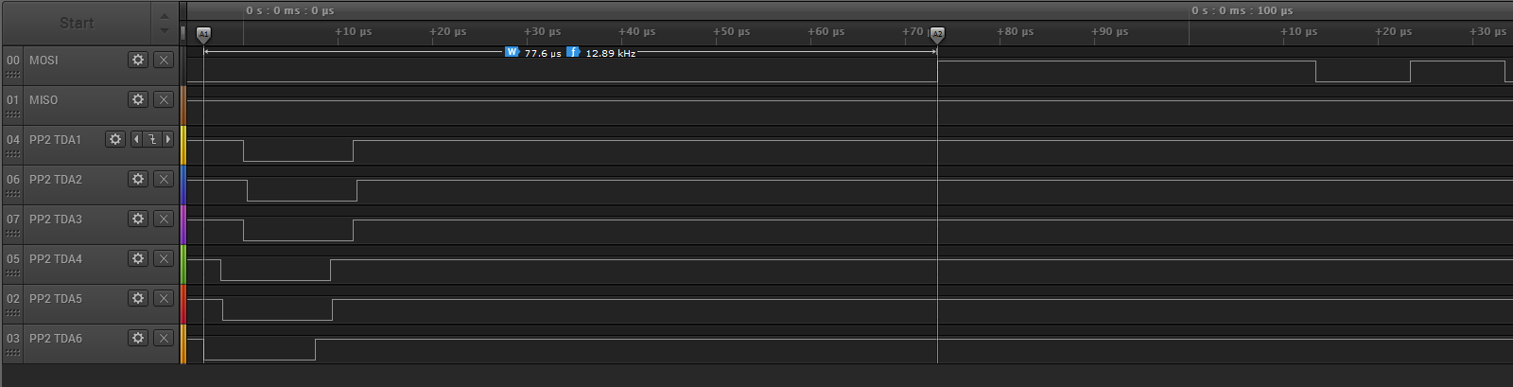
Latex/Bachelorarbeit/Abbildungen/Aufnahmen/Bilder/Logic Analyser/SPI_Interrupt_messung.PNG
