pfanchri/Bachelorarbeit/Latex/Bachelorarbeit/Abbildungen/Aufnahmen/Bilder/Logic Analyser/SPI_Start.PNG

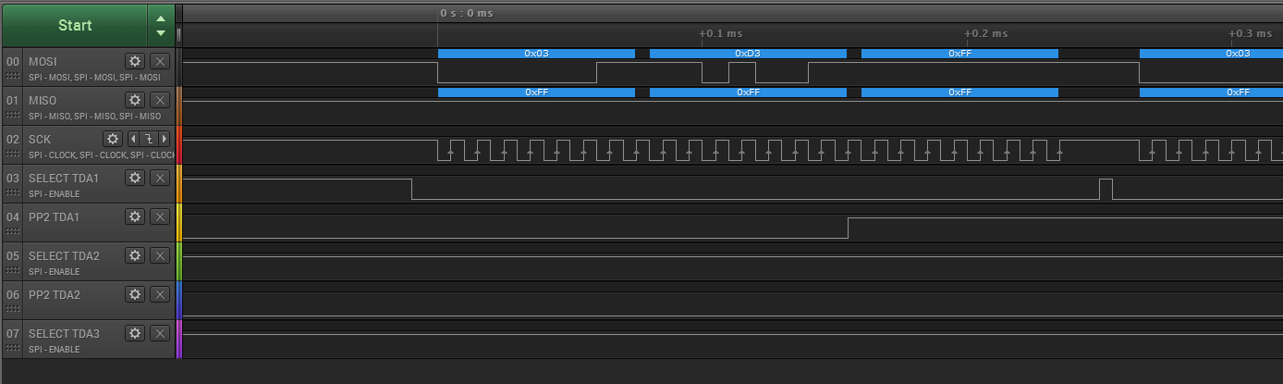
Latex/Bachelorarbeit/Abbildungen/Aufnahmen/Bilder/Logic Analyser/SPI_Start.PNG
