pfanchri/Bachelorarbeit/Latex/Bachelorarbeit/Abbildungen/Aufnahmen/Bilder/Putty/Ubertragung2.PNG

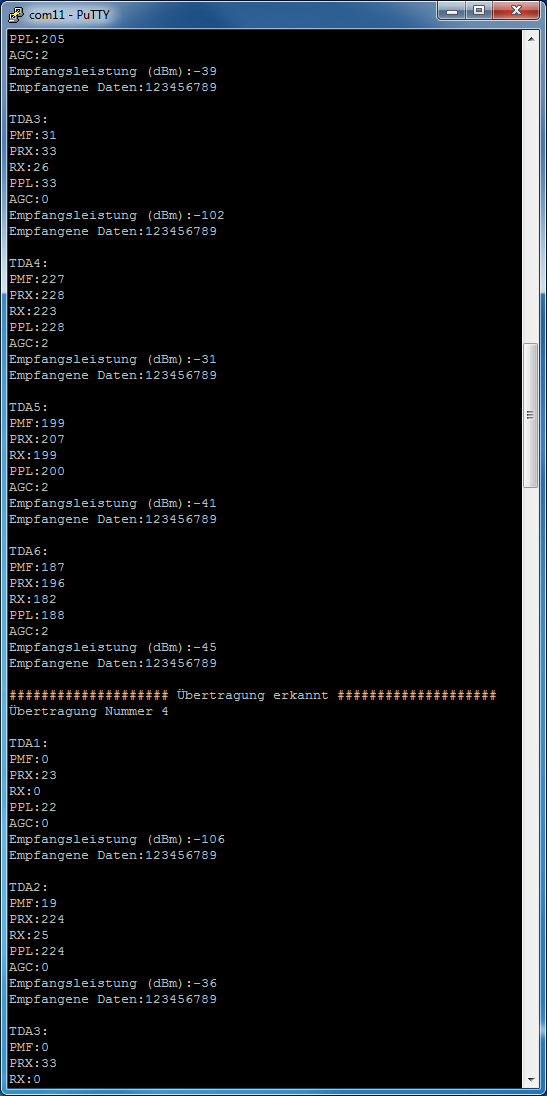
Latex/Bachelorarbeit/Abbildungen/Aufnahmen/Bilder/Putty/Ubertragung2.PNG
