pfanchri/Bachelorarbeit/Latex/Bachelorarbeit/Quellen/DAvE3.jpg

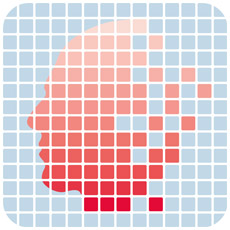
Latex/Bachelorarbeit/Quellen/DAvE3.jpg
