pfanchri/Bachelorarbeit/Latex/Bachelorarbeit/Quellen/Infineon Microcontroller avaliable/Application_Board_Kits.jpg

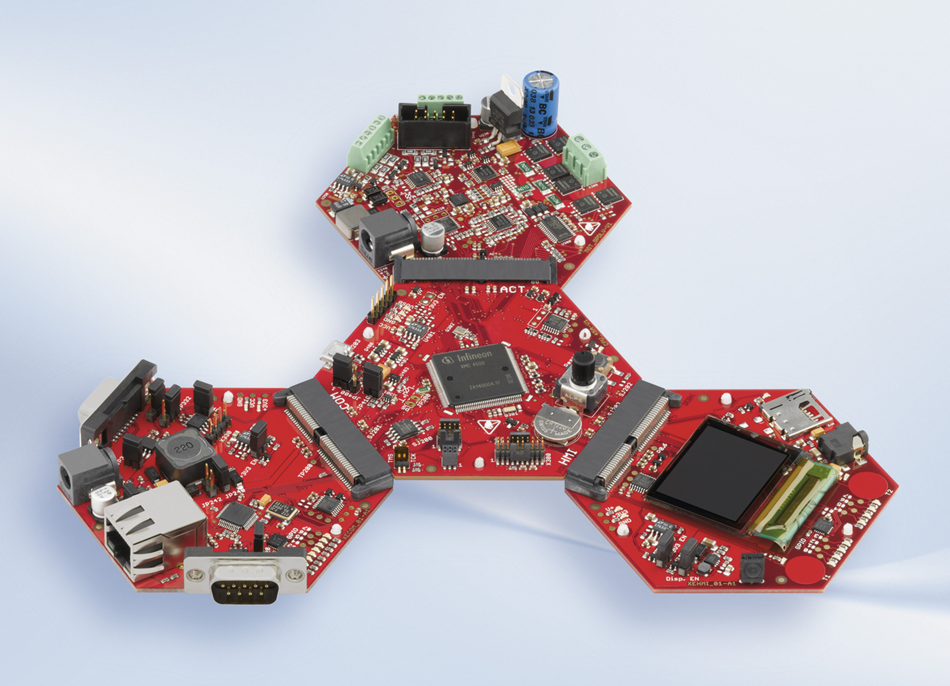
Latex/Bachelorarbeit/Quellen/Infineon Microcontroller avaliable/Application_Board_Kits.jpg
