pfanchri/Bachelorarbeit/Latex/Bachelorarbeit/Quellen/Infineon Microcontroller avaliable/XMC4500.jpg

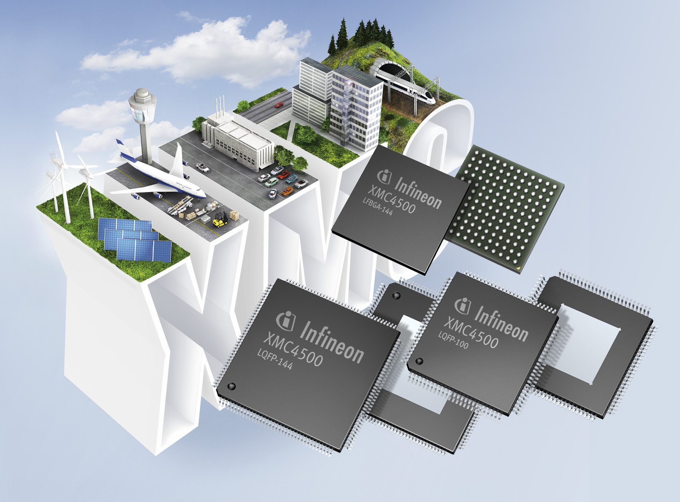
Latex/Bachelorarbeit/Quellen/Infineon Microcontroller avaliable/XMC4500.jpg
