pfanchri/Bachelorarbeit/Latex/Bachelorarbeit/Quellen/New Infineon Controller Family/XMC4500_LQFP-100_LQFP-144_LFBGA-144.jpg

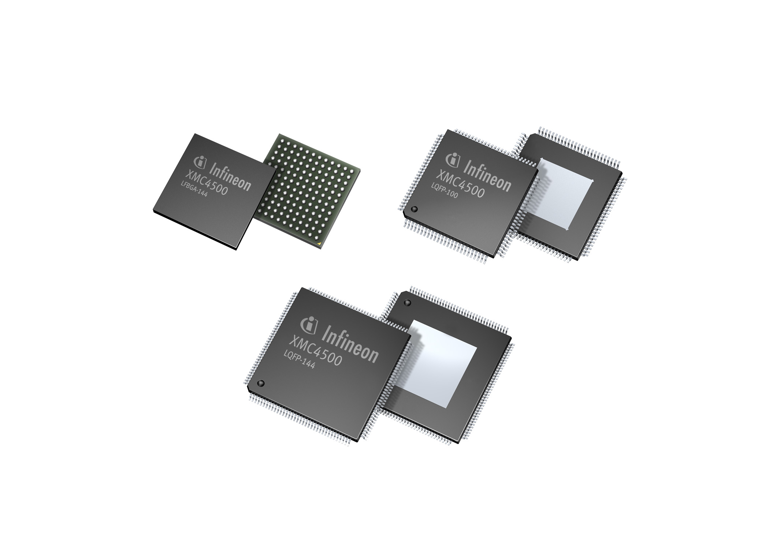
Latex/Bachelorarbeit/Quellen/New Infineon Controller Family/XMC4500_LQFP-100_LQFP-144_LFBGA-144.jpg
