pfanchri/Bachelorarbeit/Latex/Bachelorarbeit/Quellen/XMC4500-E144F1024 AC/XMC4500_LQFP-144_plain_lowres.jpg_472149771.jpg

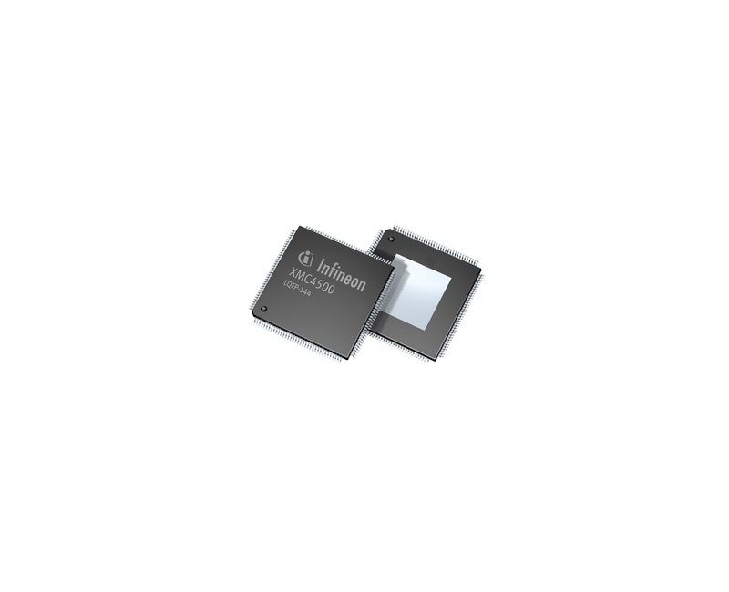
Latex/Bachelorarbeit/Quellen/XMC4500-E144F1024 AC/XMC4500_LQFP-144_plain_lowres.jpg_472149771.jpg
