pfanchri/Bachelorarbeit/Latex/Bachelorarbeit/Quellen/XMC4500_LQFP-100_vA_plain_lowres.jpg

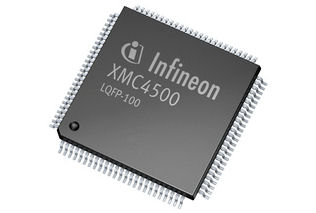
Latex/Bachelorarbeit/Quellen/XMC4500_LQFP-100_vA_plain_lowres.jpg
