pfanchri/Bachelorarbeit/Altium/Box/ImportSW_alt/PCB_Testplatine.SLDASM

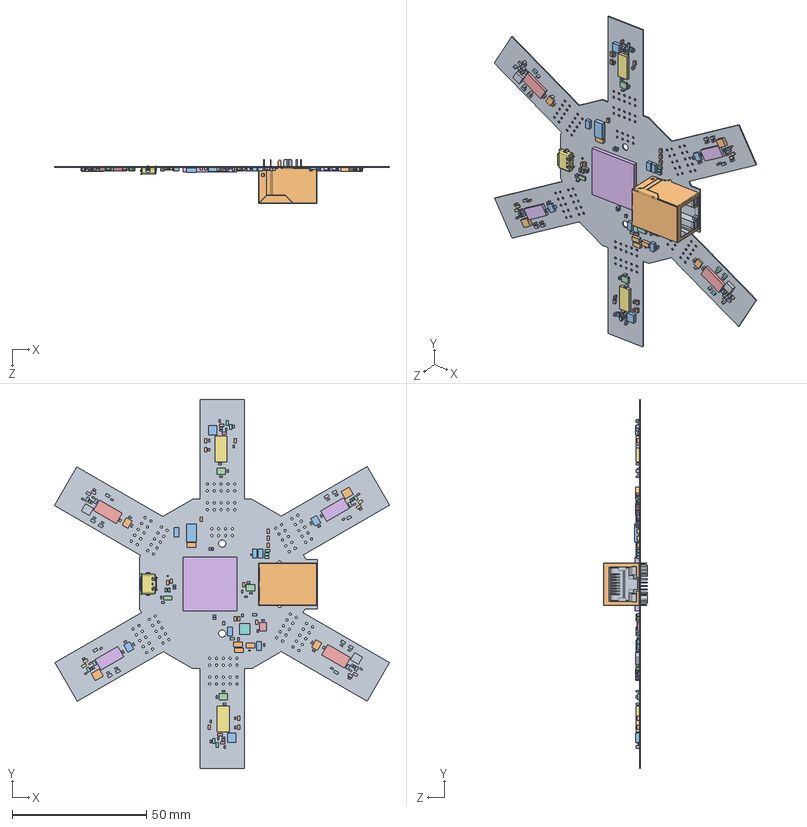
[picture p90: CAD file, 2016-07-27]
Altium/Box/ImportSW_alt/PCB_Testplatine.SLDASM
124.8 x 137.4 x 16.6 mm
Board
Extruded x 2
Extruded_2 x 2
Extruded_3 x 3
Extruded_4 x 2
Extruded_5 x 2
Extruded_6 x 2
Extruded_7 x 6
Extruded_8 x 6
Extruded_9 x 16
Extruded_10 x 4
Extruded_11 x 4
Extruded_12 x 4
Extruded_13 x 4
Extruded_14 x 4
Extruded_15 x 4
Extruded_16 x 2
Extruded_17 x 2
Extruded_18 x 2
Extruded_19 x 14
Extruded_20 x 14
Extruded_21 x 21
Extruded_22 x 8
Extruded_23 x 8
Extruded_24 x 17
Extruded_25 x 4
Extruded_26 x 5
WE-VE_0603 x 2
Extruded_27 x 2
Extruded_28 x 2
Extruded_29
Extruded_30 x 5
housing
shielding
Extruded_31
Extruded_32
Extruded_33
Extruded_34
Extruded_35
