pfanchri/Bachelorarbeit/Dave/Basisstation/TDA_XMC4500_PMA_testtrans/Dave/Model/APPS/CLOCK_XMC4/v4_0_6/doc/ClockTree.png

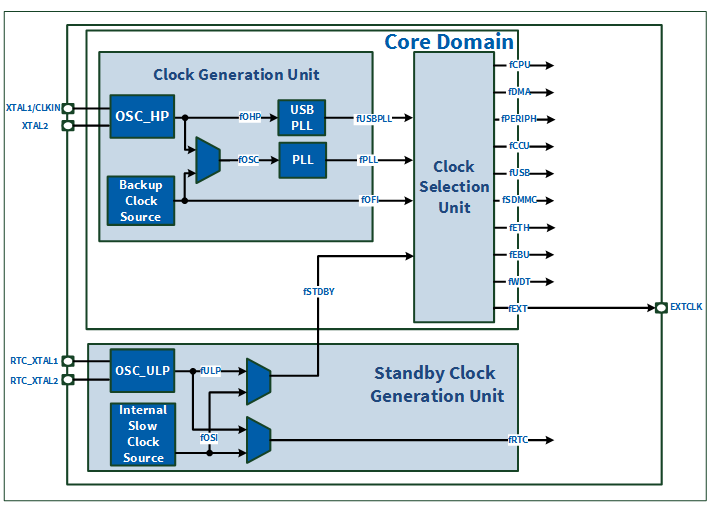
Dave/Basisstation/TDA_XMC4500_PMA_testtrans/Dave/Model/APPS/CLOCK_XMC4/v4_0_6/doc/ClockTree.png
