pfanchri/Bachelorarbeit/Latex/Bachelorarbeit/Abbildungen/Aufnahmen/SmartPDF/mobile Basisstation.pdf

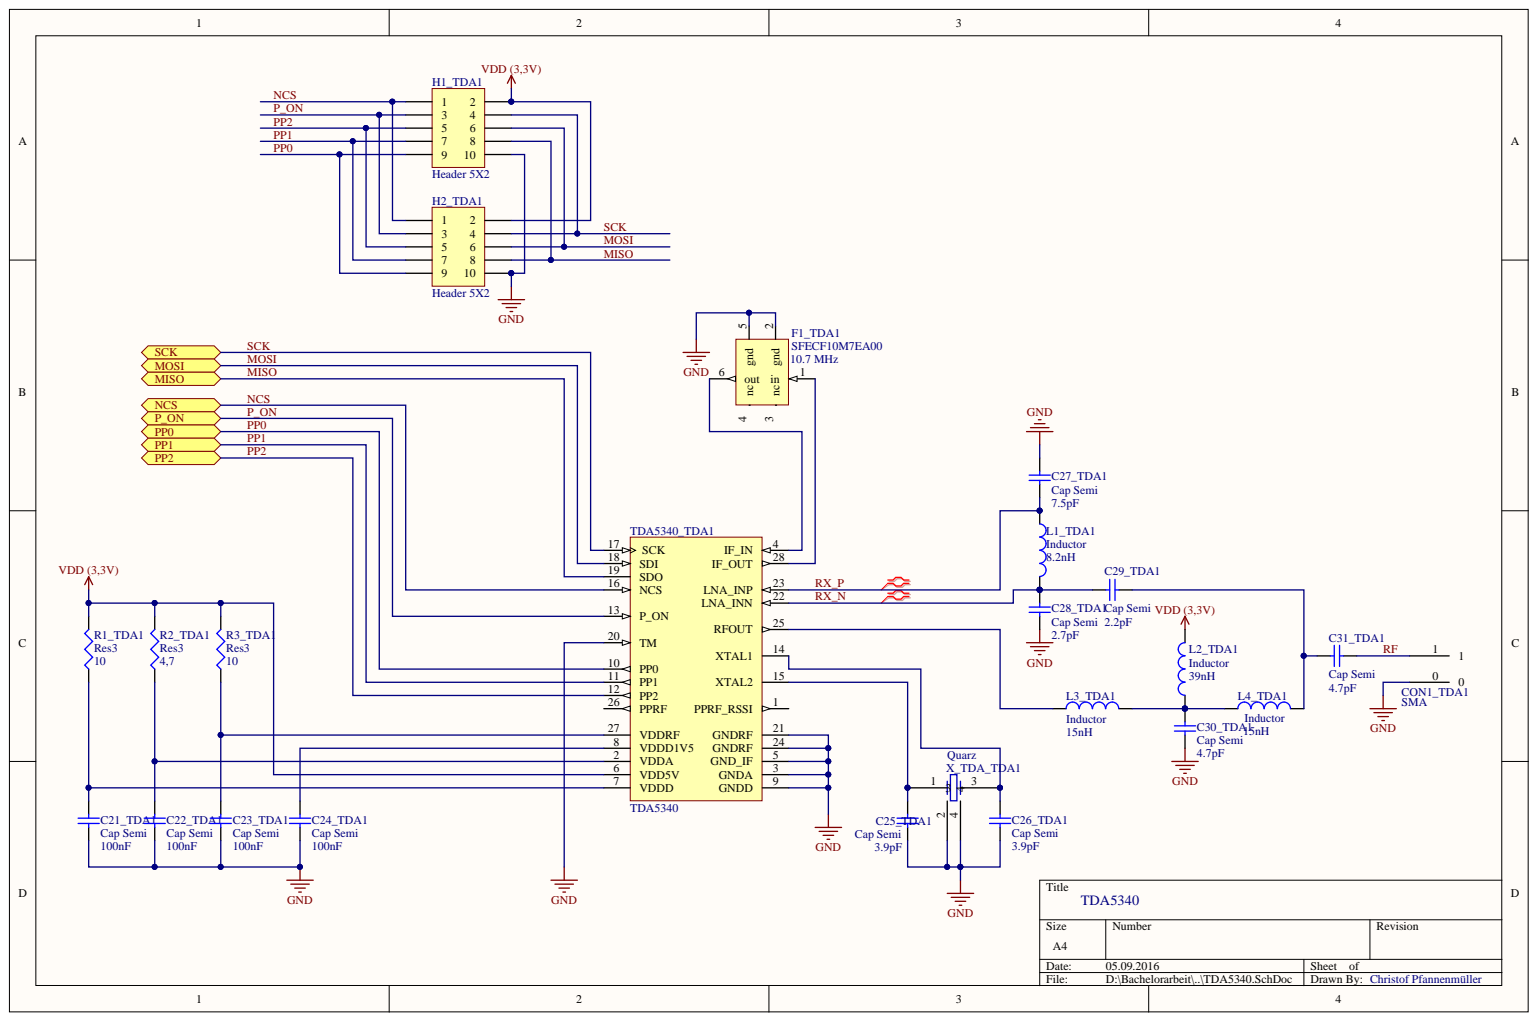
[picture p99: page 1]

NCS 16
P_ON 13 | RX_N | Cap Semi | VDD (3,3V) L2_TDA1 Inductor 39nH

R3_TDA1 Res3 10 | | TM 20

PPRF 26

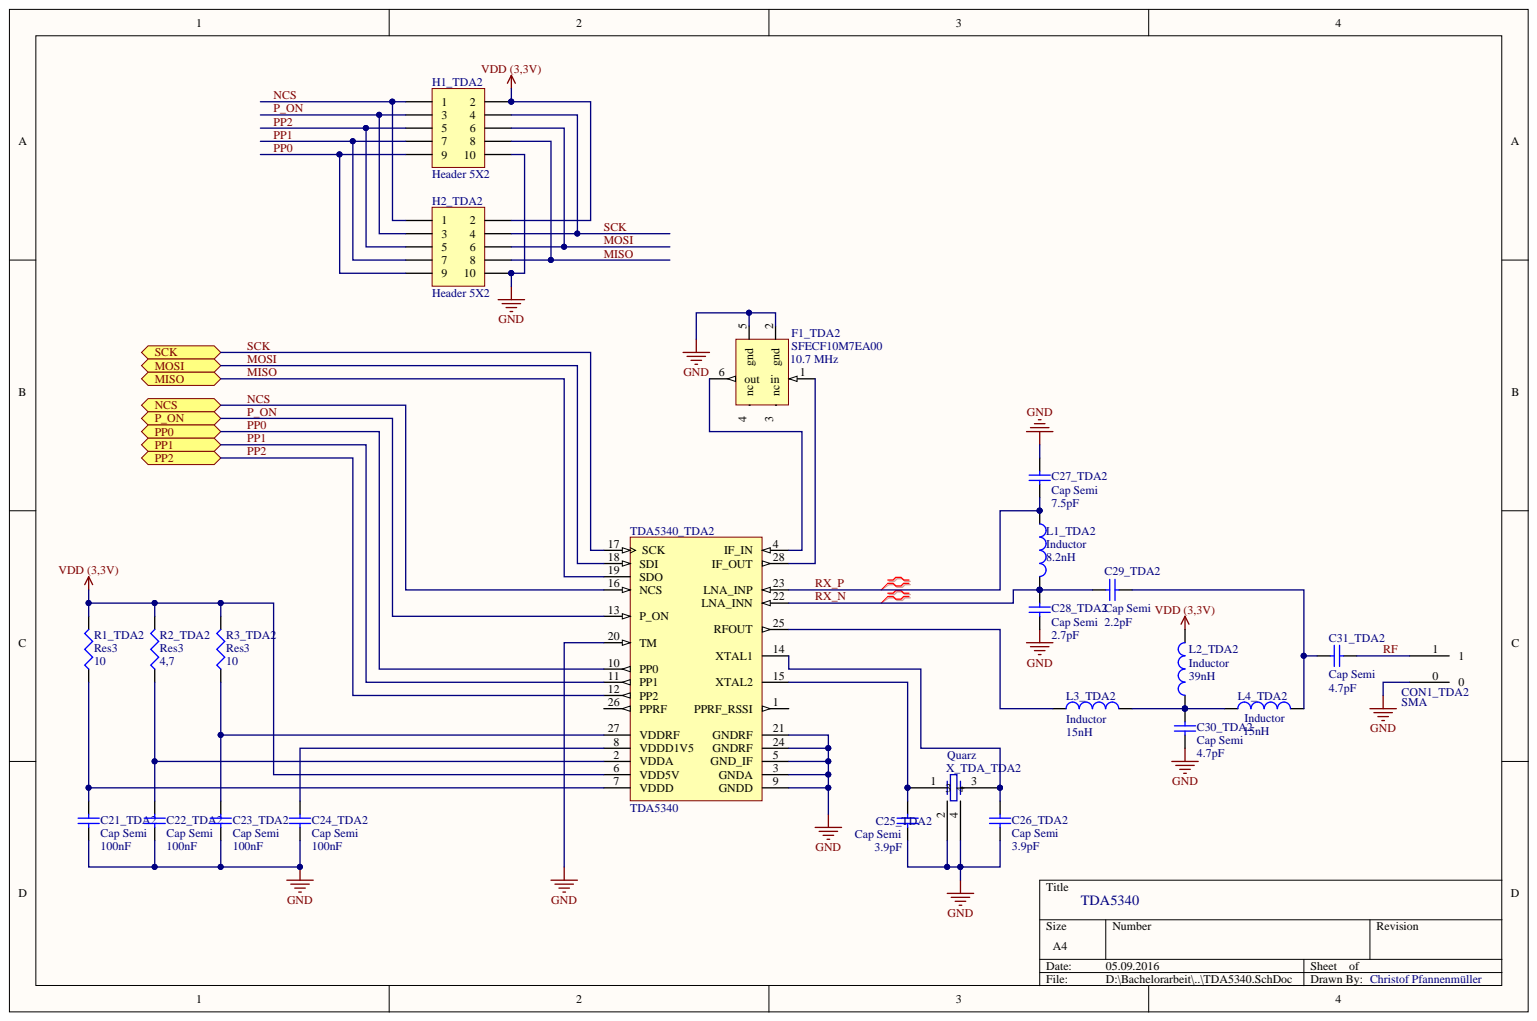
[picture p100: page 2]

NCS 16
P_ON 13 | RX_N | Cap Semi | VDD (3,3V) L2_TDA2 Inductor 39nH

R3_TDA2 Res3 10 | | TM 20

PPRF 26

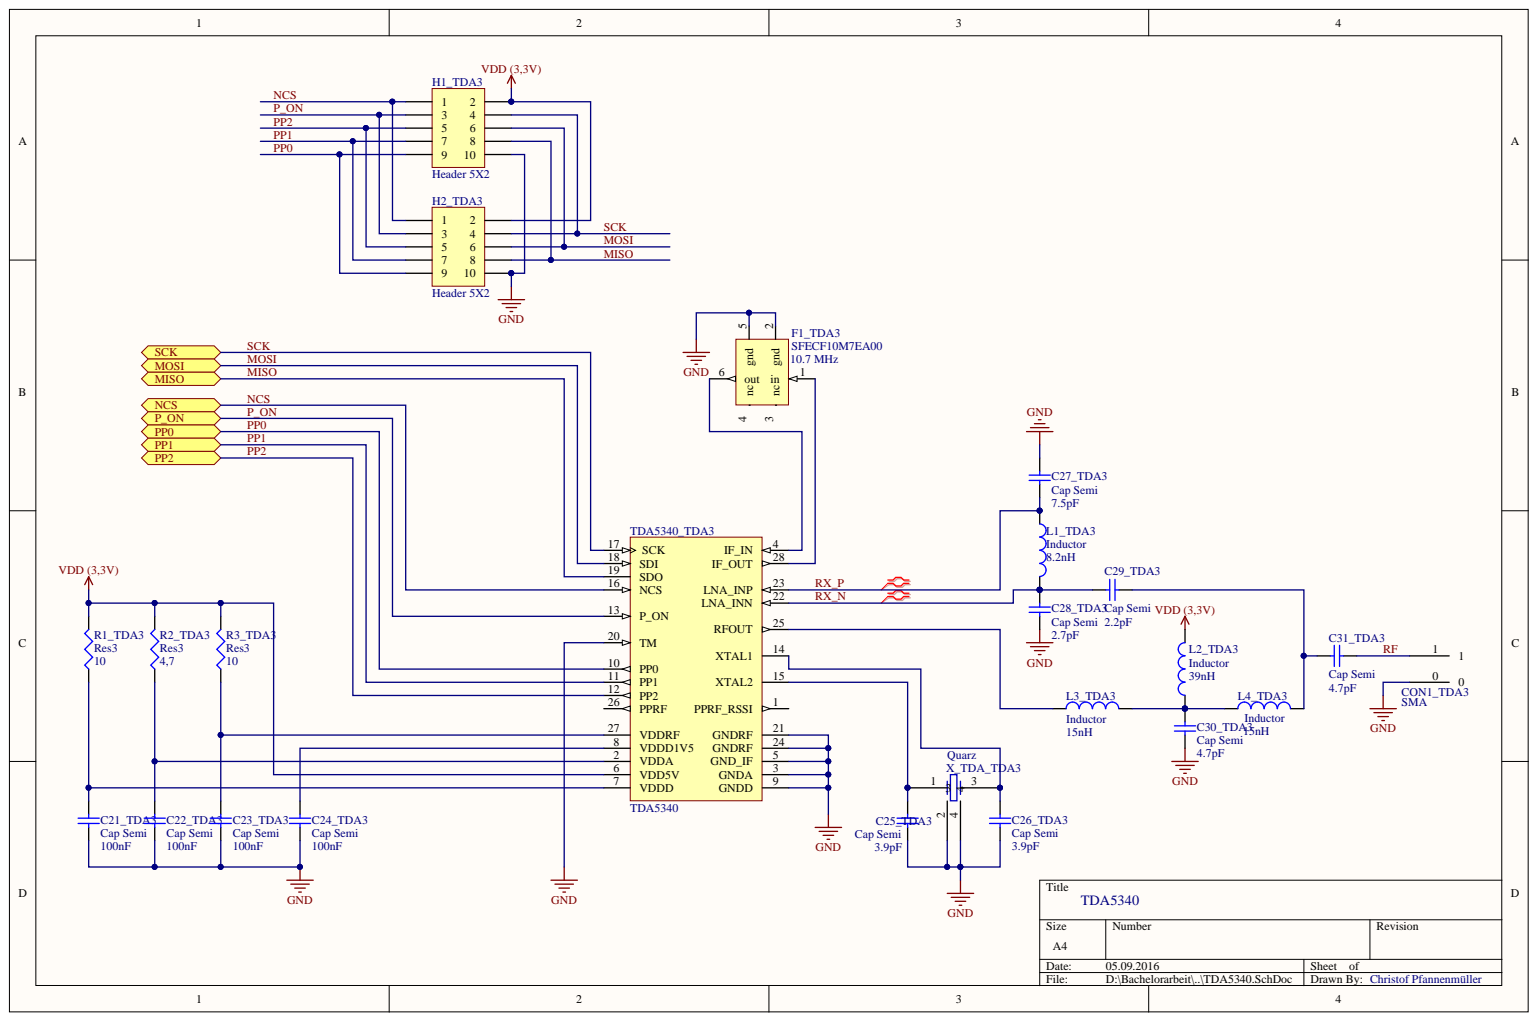
[picture p101: page 3]

NCS 16
P_ON 13 | RX_N | Cap Semi | VDD (3,3V) L2_TDA3 Inductor 39nH

R3_TDA3 Res3 10 | | TM 20

PPRF 26

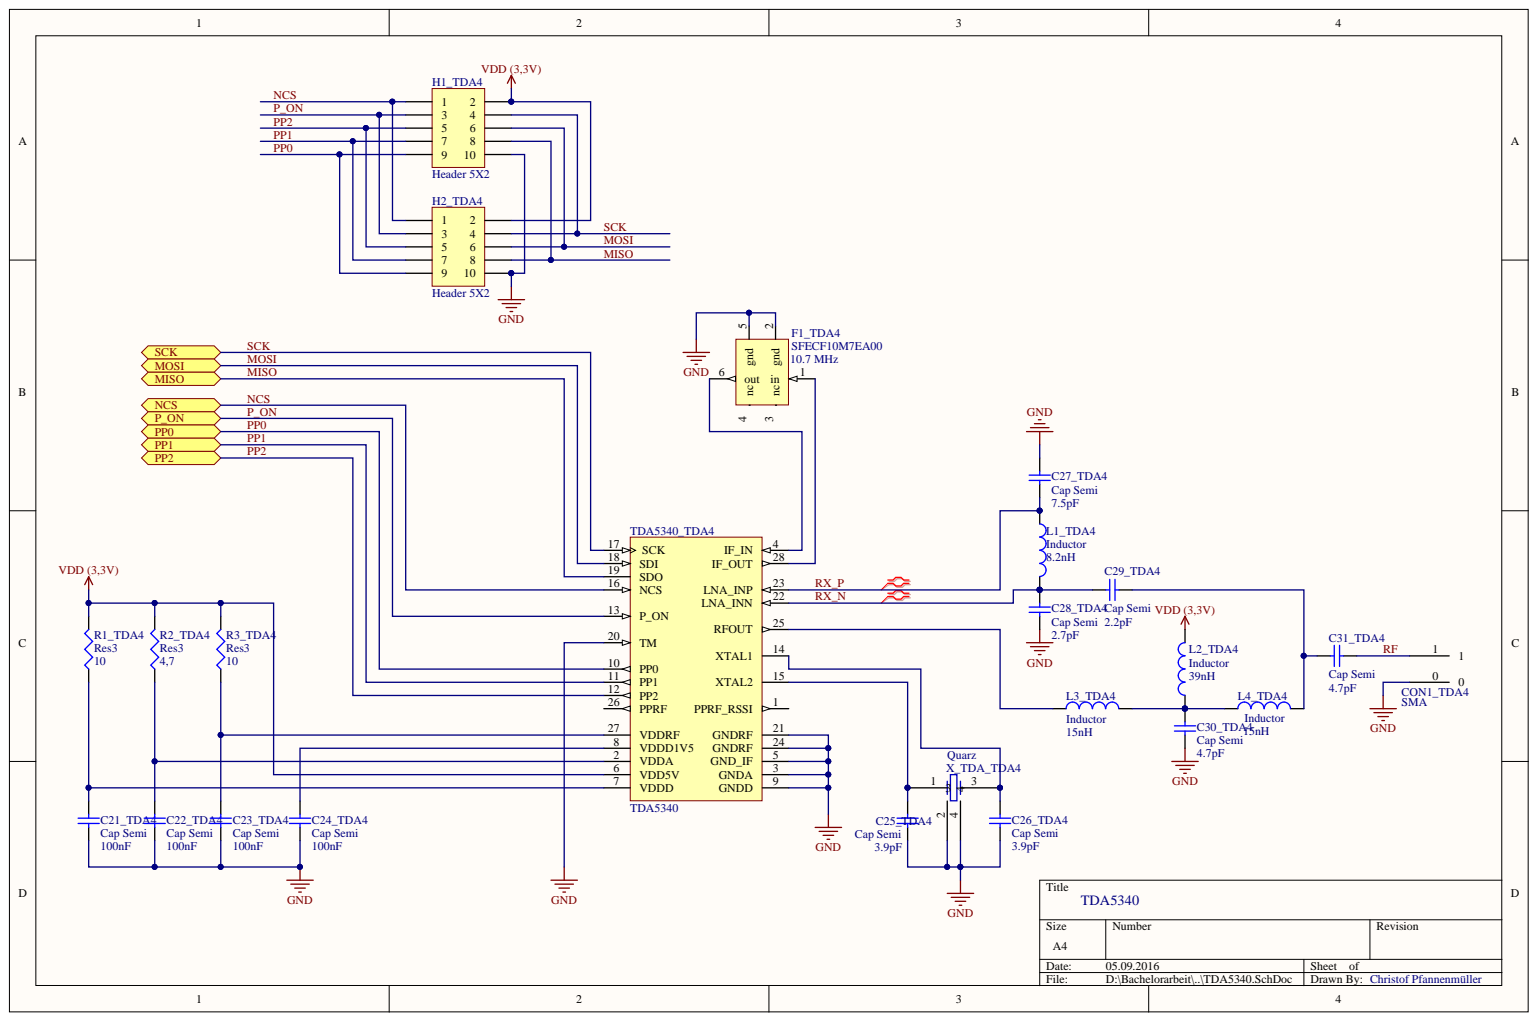
[picture p102: page 4]

NCS 16
P_ON 13 | RX_N | Cap Semi | VDD (3,3V) L2_TDA4 Inductor 39nH

R3_TDA4 Res3 10 | | TM 20

PPRF 26

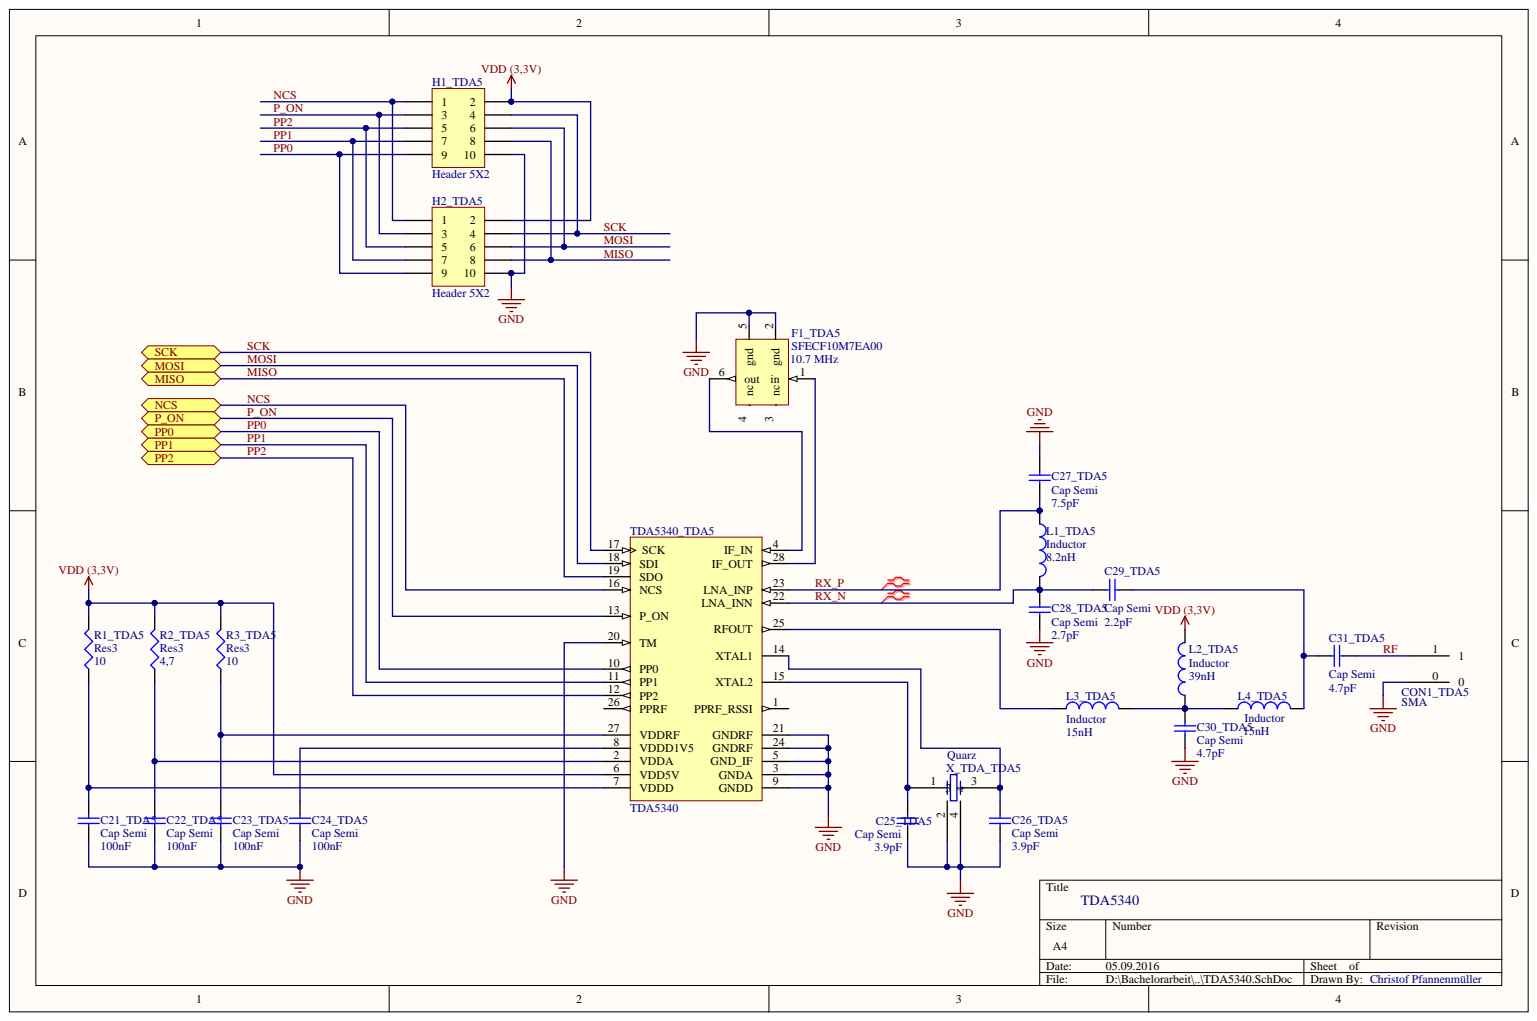
[picture p103: page 5]

NCS 16
P_ON 13 | RX_N | Cap Semi | VDD (3,3V) L2_TDA5 Inductor 39nH

R3_TDA5 Res3 10 | | TM 20

PPRF 26

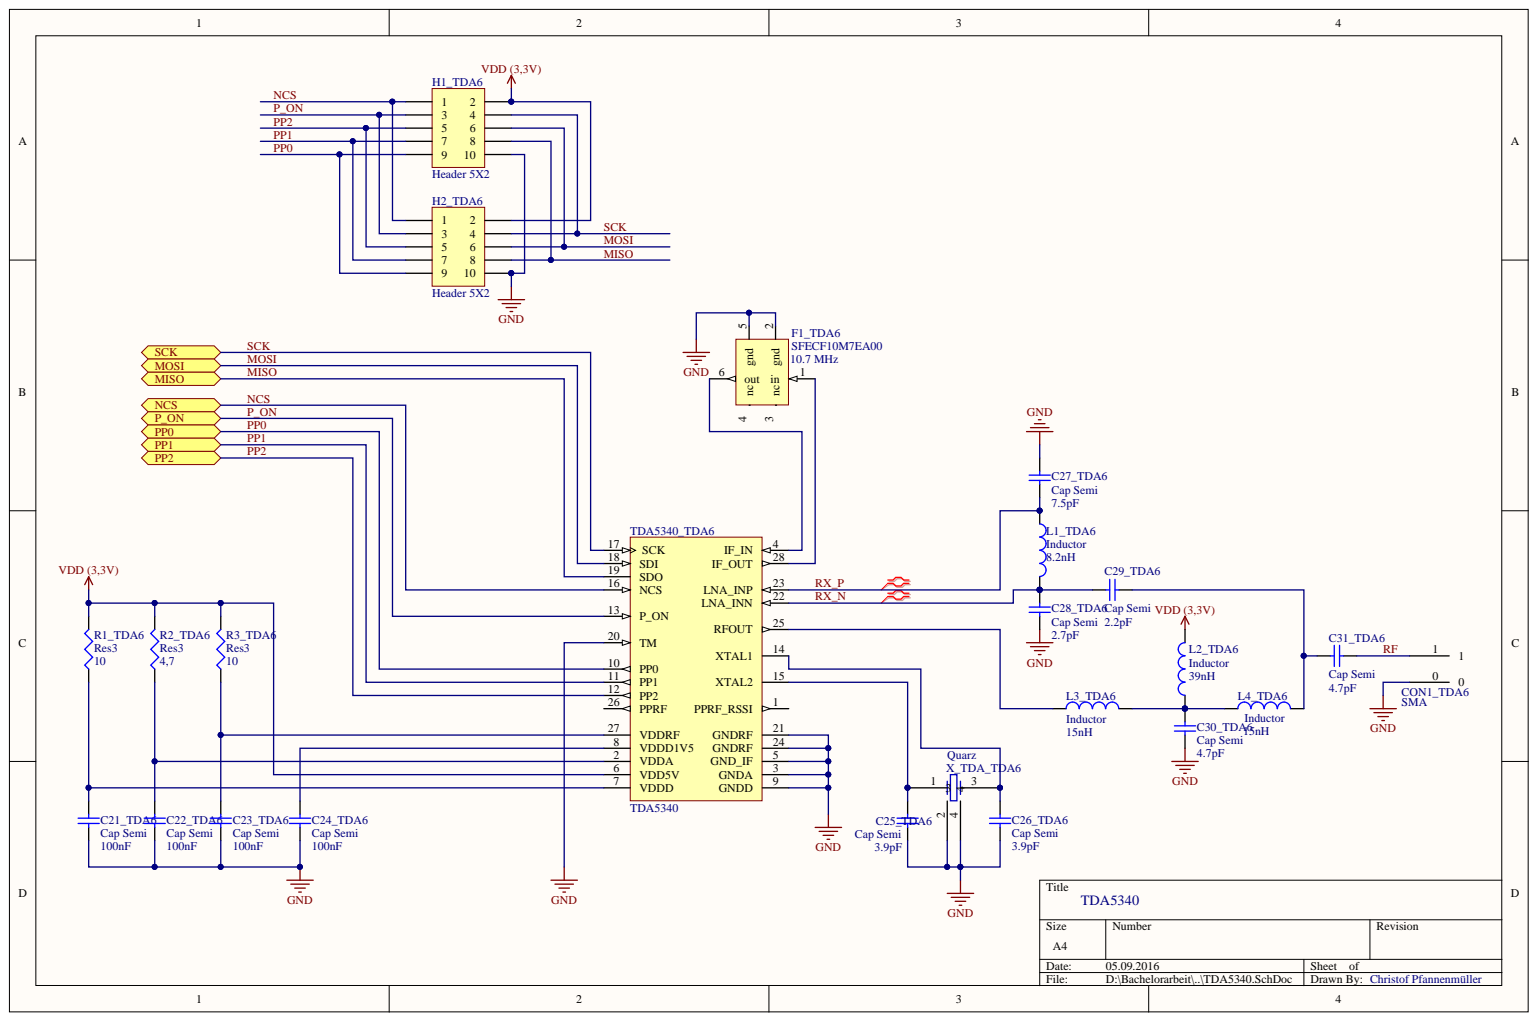
[picture p104: page 6]

NCS 16
P_ON 13 | RX_N | Cap Semi | VDD (3,3V) L2_TDA6 Inductor 39nH

R3_TDA6 Res3 10 | | TM 20

PPRF 26

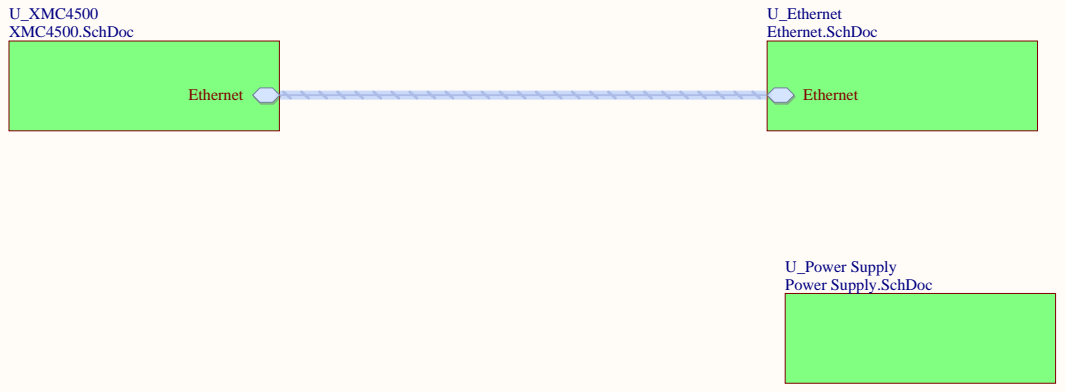
[picture p105: page 7]

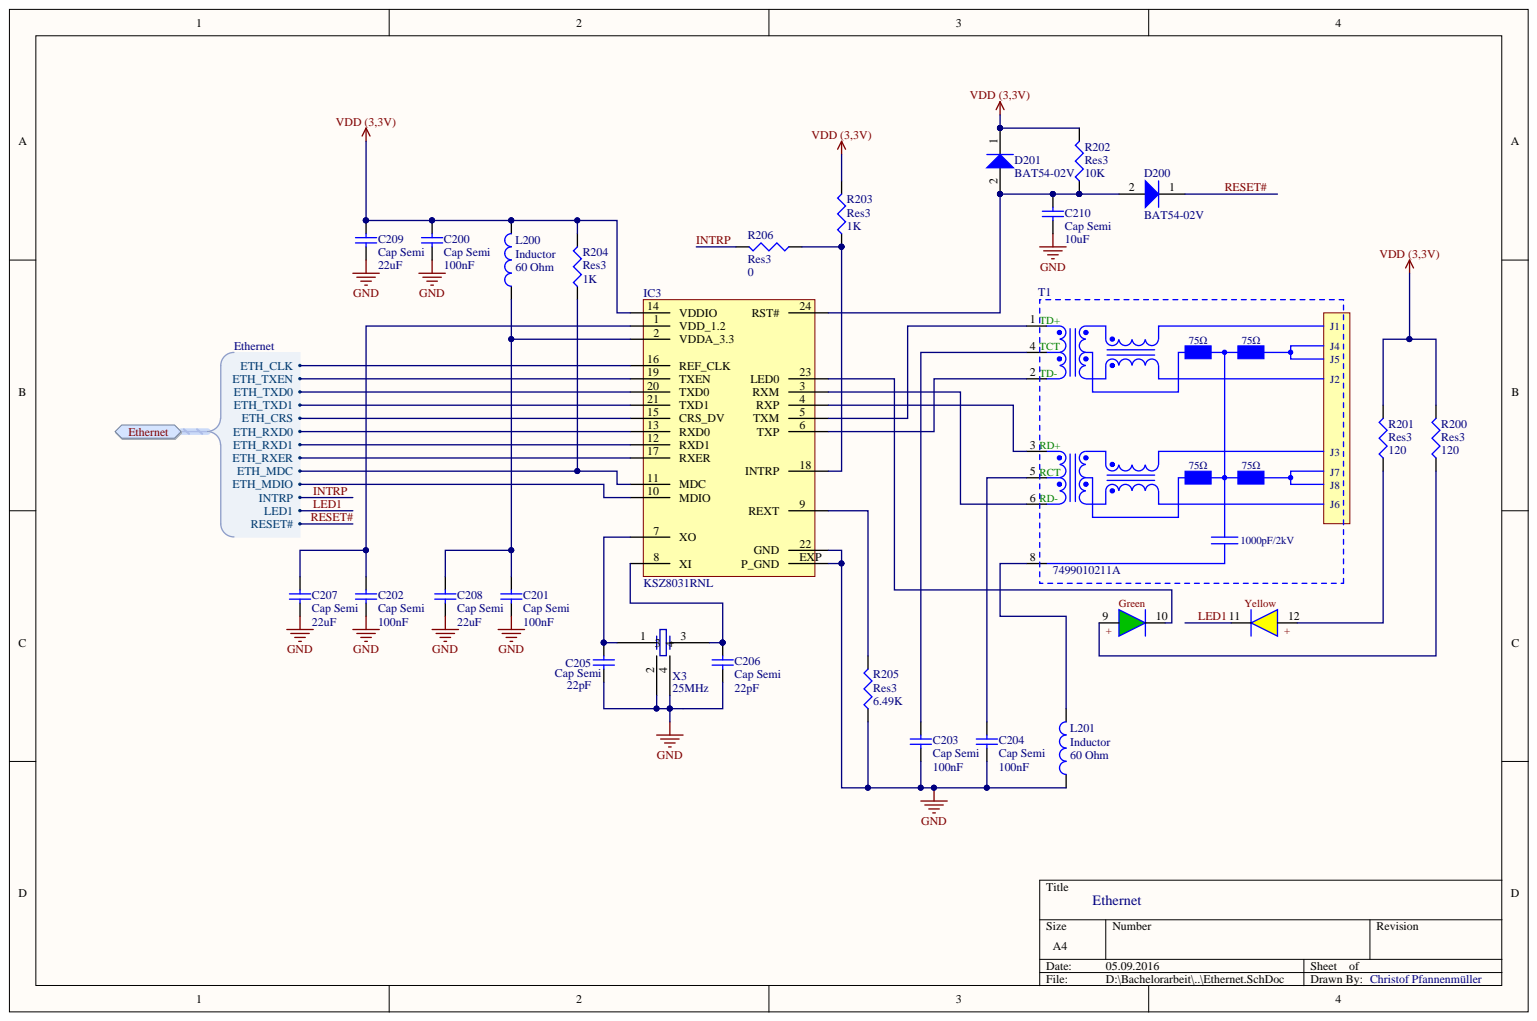
[picture p106: page 8]

VDDA_3.3 2

REF_CLK 16
TXEN 19
TXD0 20
TXD1 21
CRS_DV 15
RXD1 12 RXD0 13

RXER 17

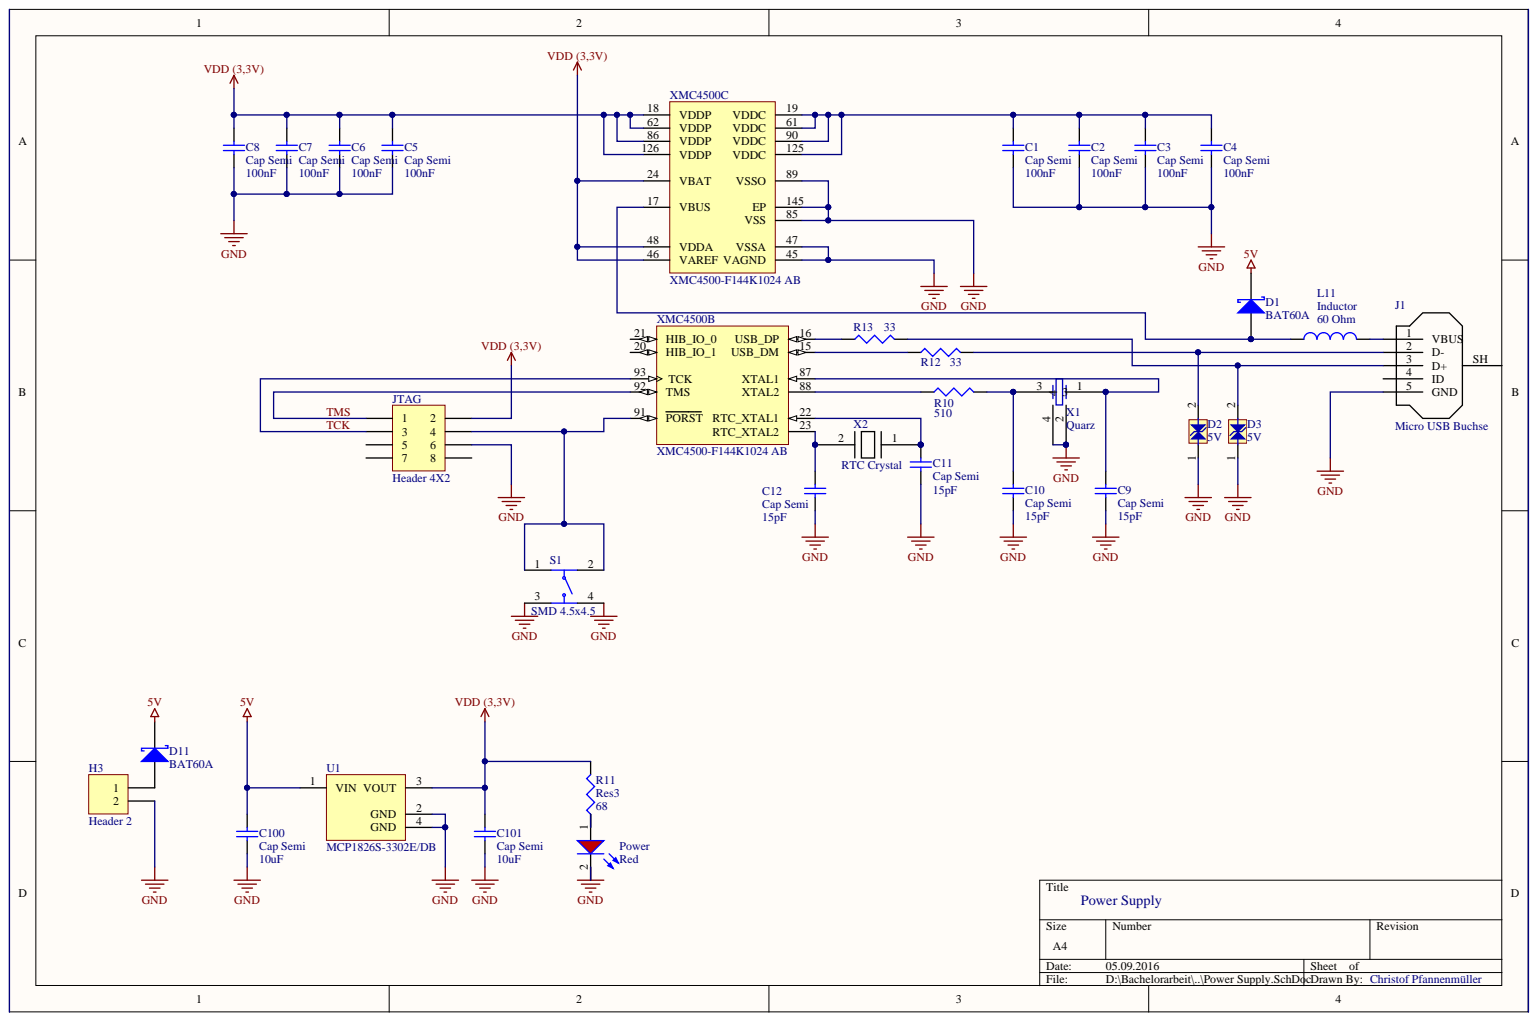
[picture p107: page 9]

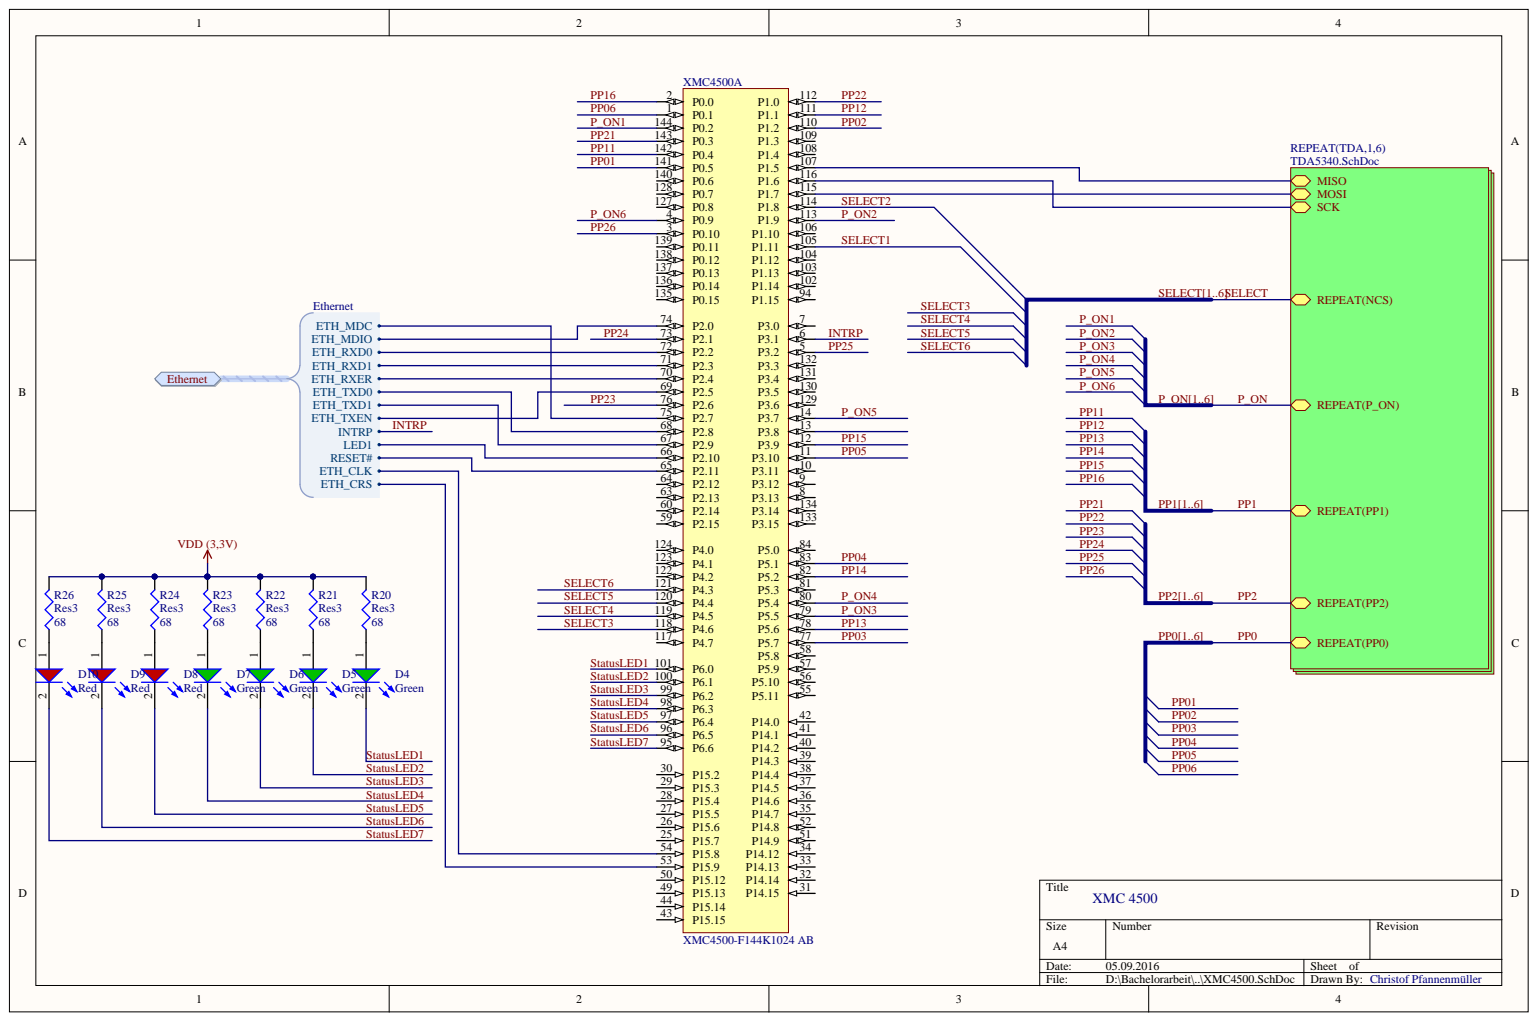
[picture p108: page 10]

D4 Green

StatusLED1

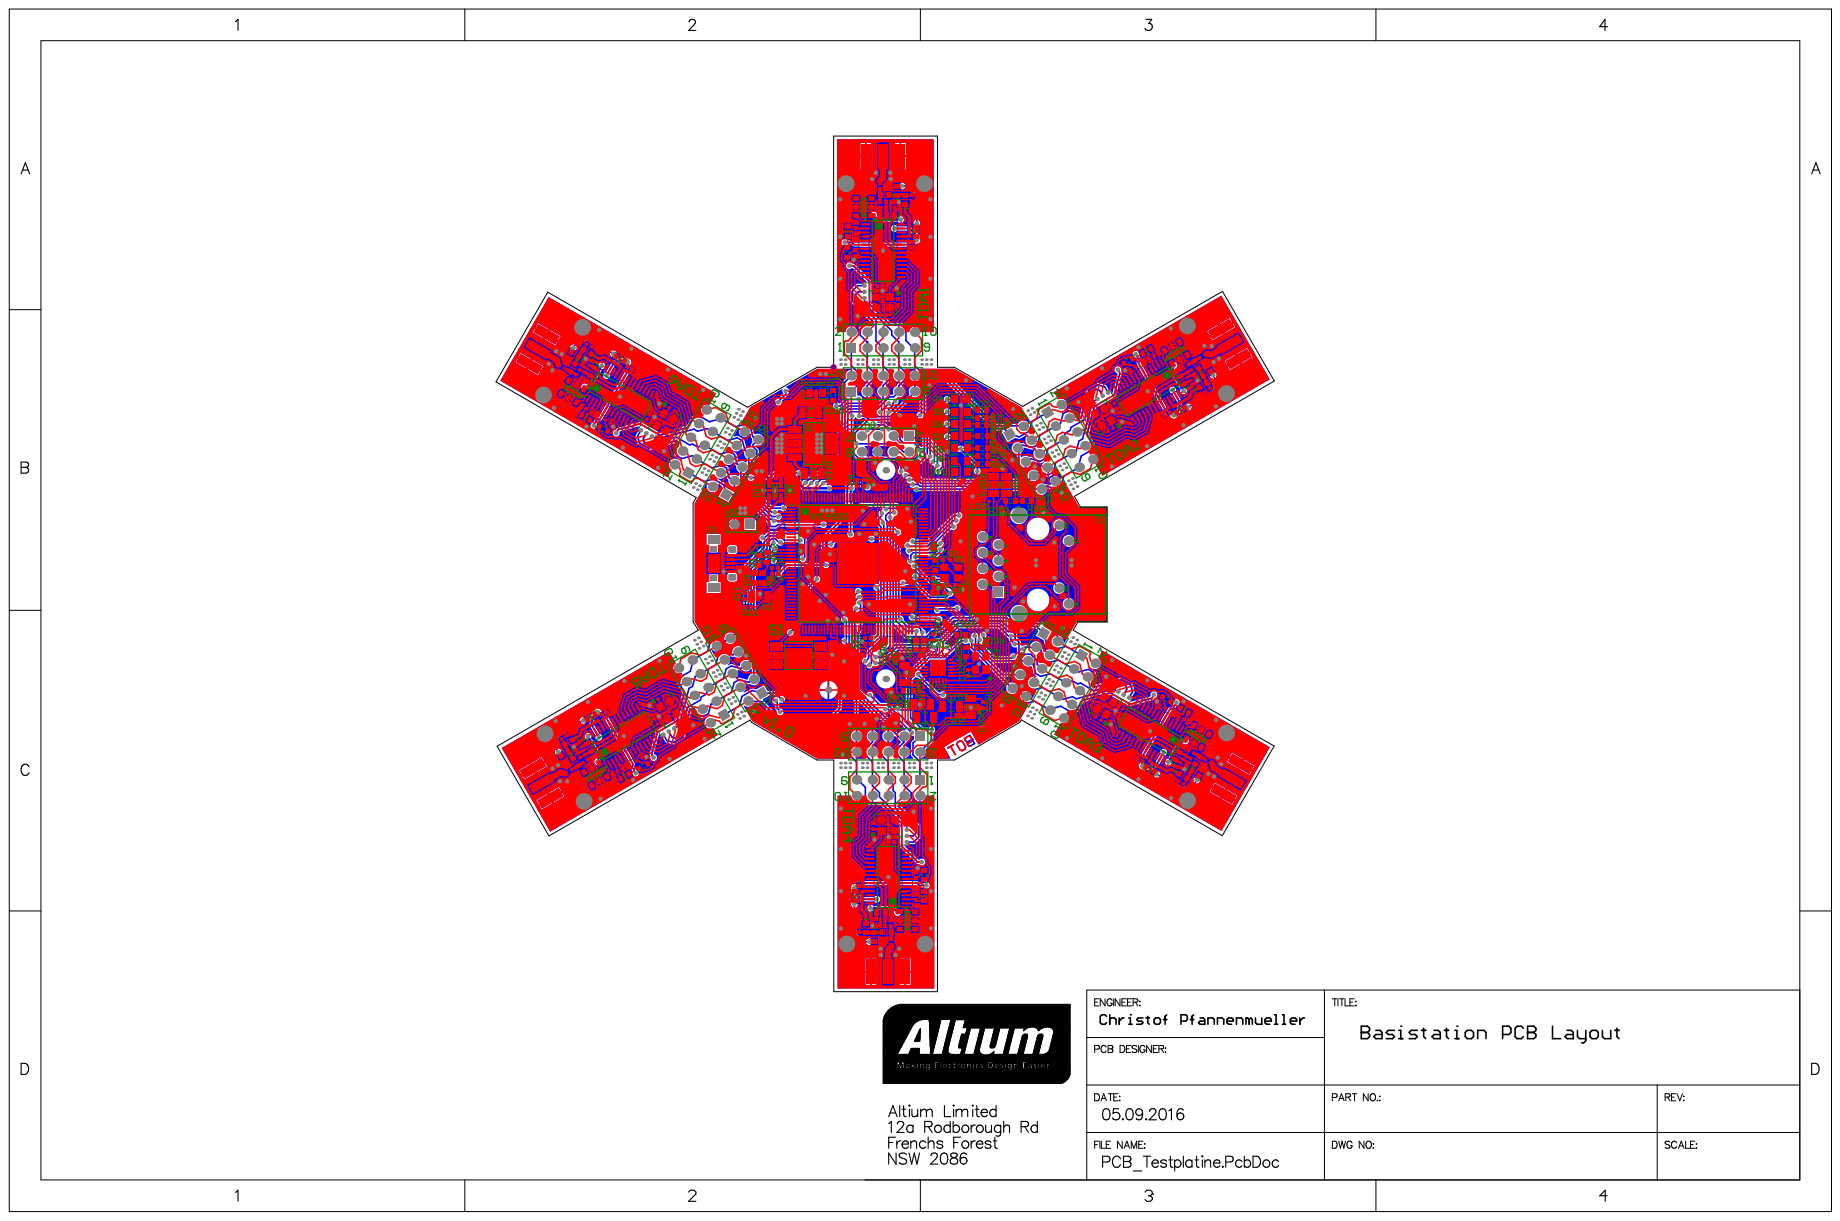
[picture p109: page 11]
