pfanchri/Bachelorarbeit/Latex/Bachelorarbeit/Abbildungen/Aufnahmen/SmartPDF/TDA-antenna_rev2.pdf

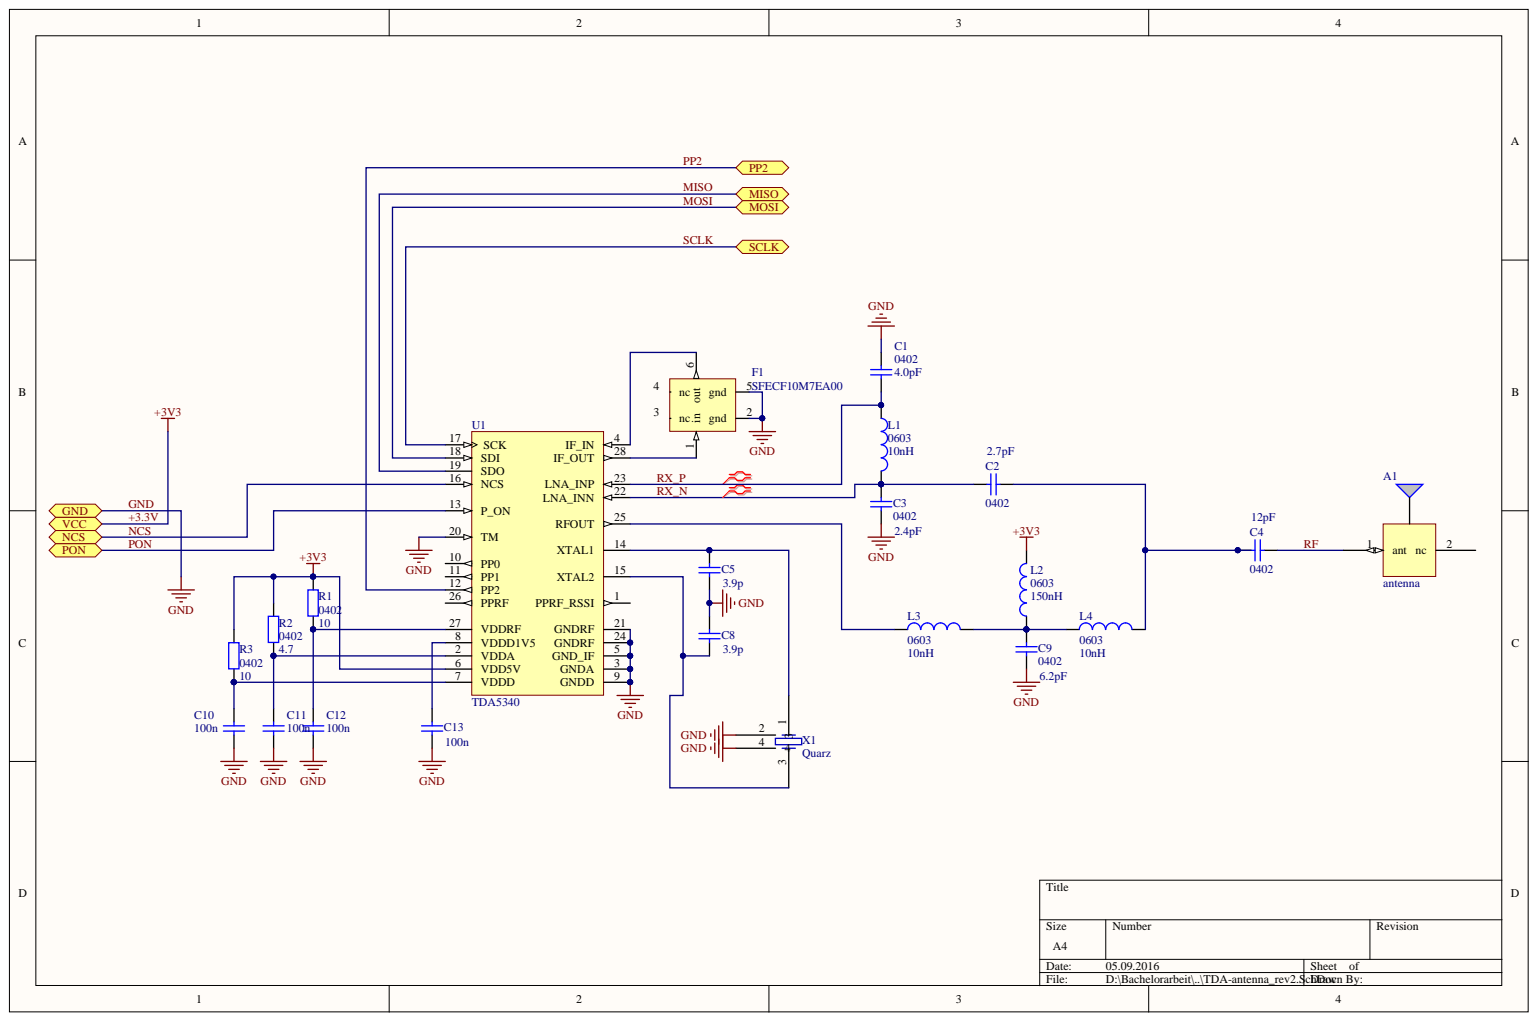
[picture p110: page 1]

SDI 18 IF_OUT | 28
SDO 19

PPRF 26 PPRF_RSSI GNDRF GNDRF VDDD1V5 VDDA GND_IF VDD5V GNDA VDDD GNDD | 1 | C8 3.9p

VDDRF 27 | 21 24

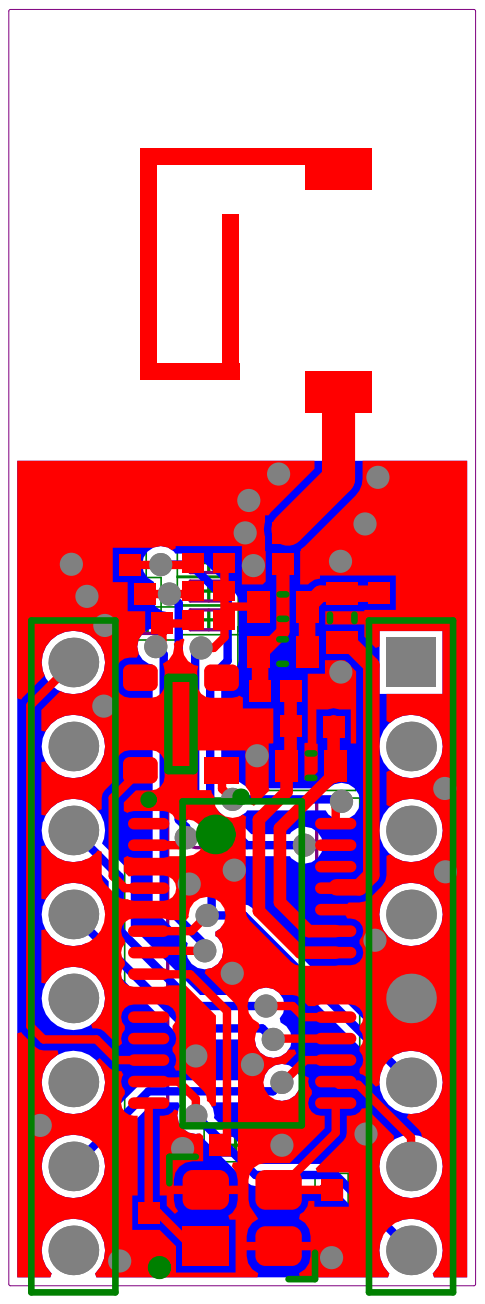
[picture p111: page 2]
