pfanchri/Bachelorarbeit/Präsentation/Bilder/ERU Übersicht.pdf

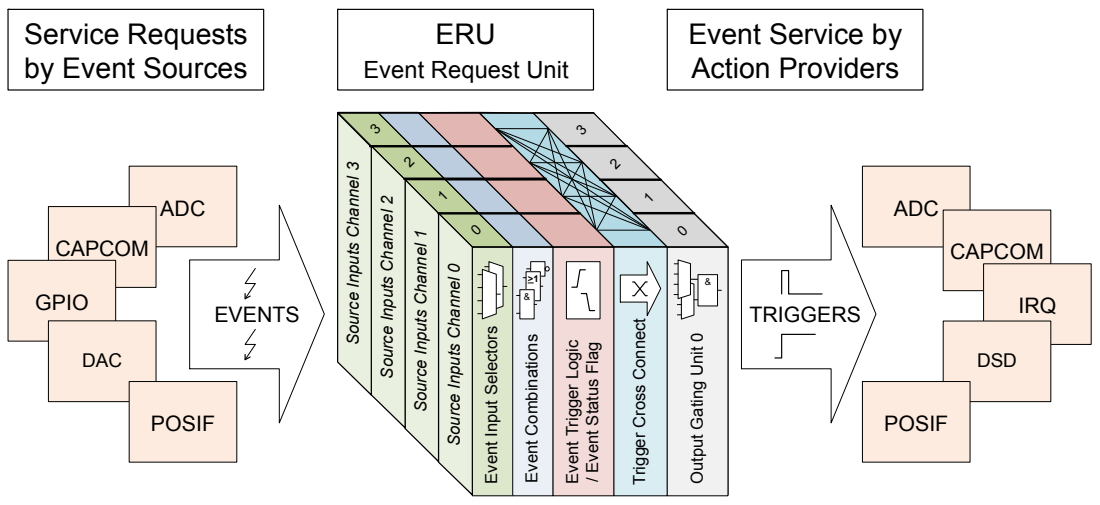
[picture p114: page 1]
A similar structure exists for input Bx (selection from ERU_xB[3:0]). Event Input Selectors; Event Combinations; Event Trigger Logic; Trigger Cross Connect / Event Status Flag; Output Gating Unit 0; ADC; CAPCOM; GPIO; DAC; POSIF; IRQ; DSD; EVENTS; TRIGGERS

Service Requests
by Event Sources

ERU
Event Request Unit

Event Service by
Action Providers

Source Inputs Channel 3

Source Inputs Channel 2

Source Inputs Channel 1

Source Inputs Channel 0
