pfanchri/Bachelorarbeit/Altium/mobile Basisstation/mobile Basisstation.pdf

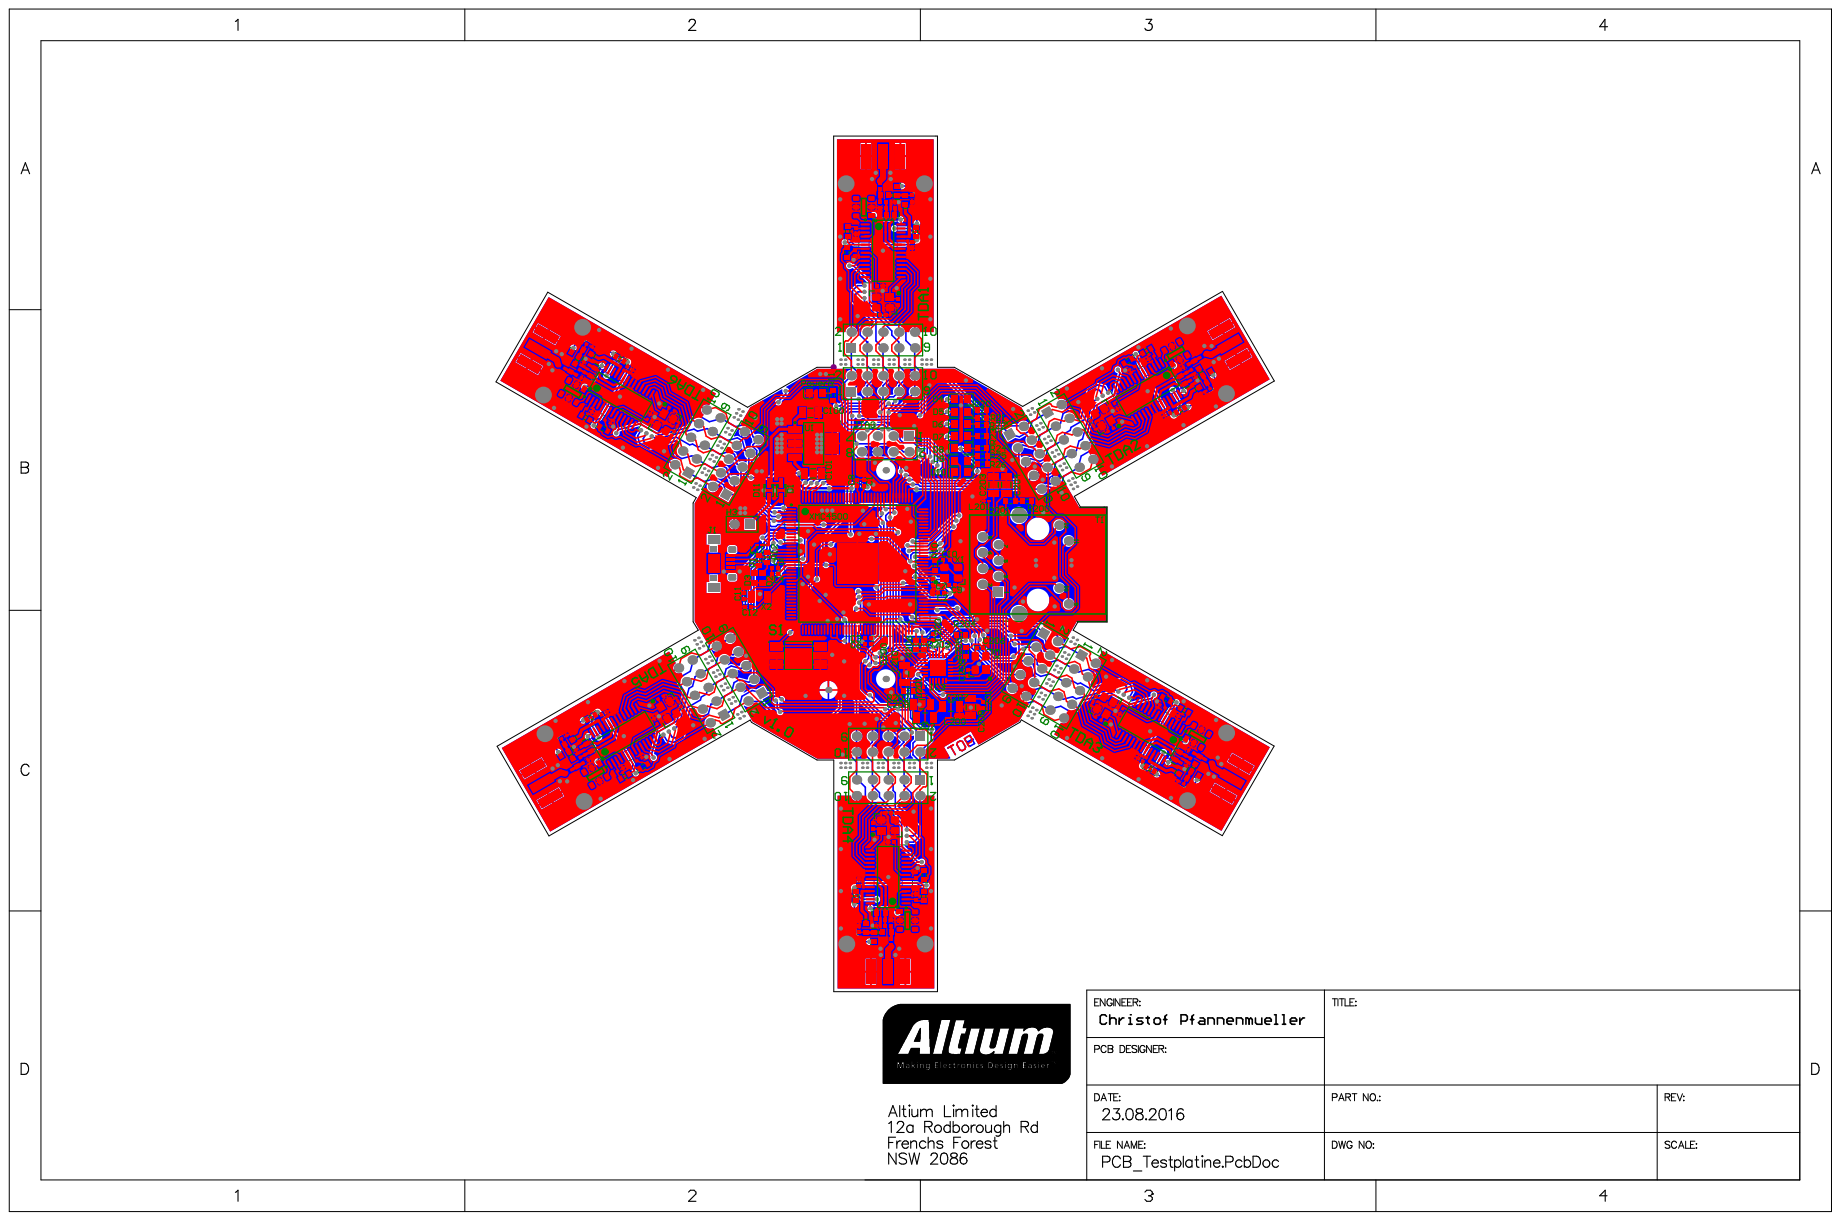
[picture p115: page 1]
