pfanchri/Bachelorarbeit/Altium/mobile Basisstation/Project Outputs for mobile Basisstation/Basisstation Composite Drawing.PDF

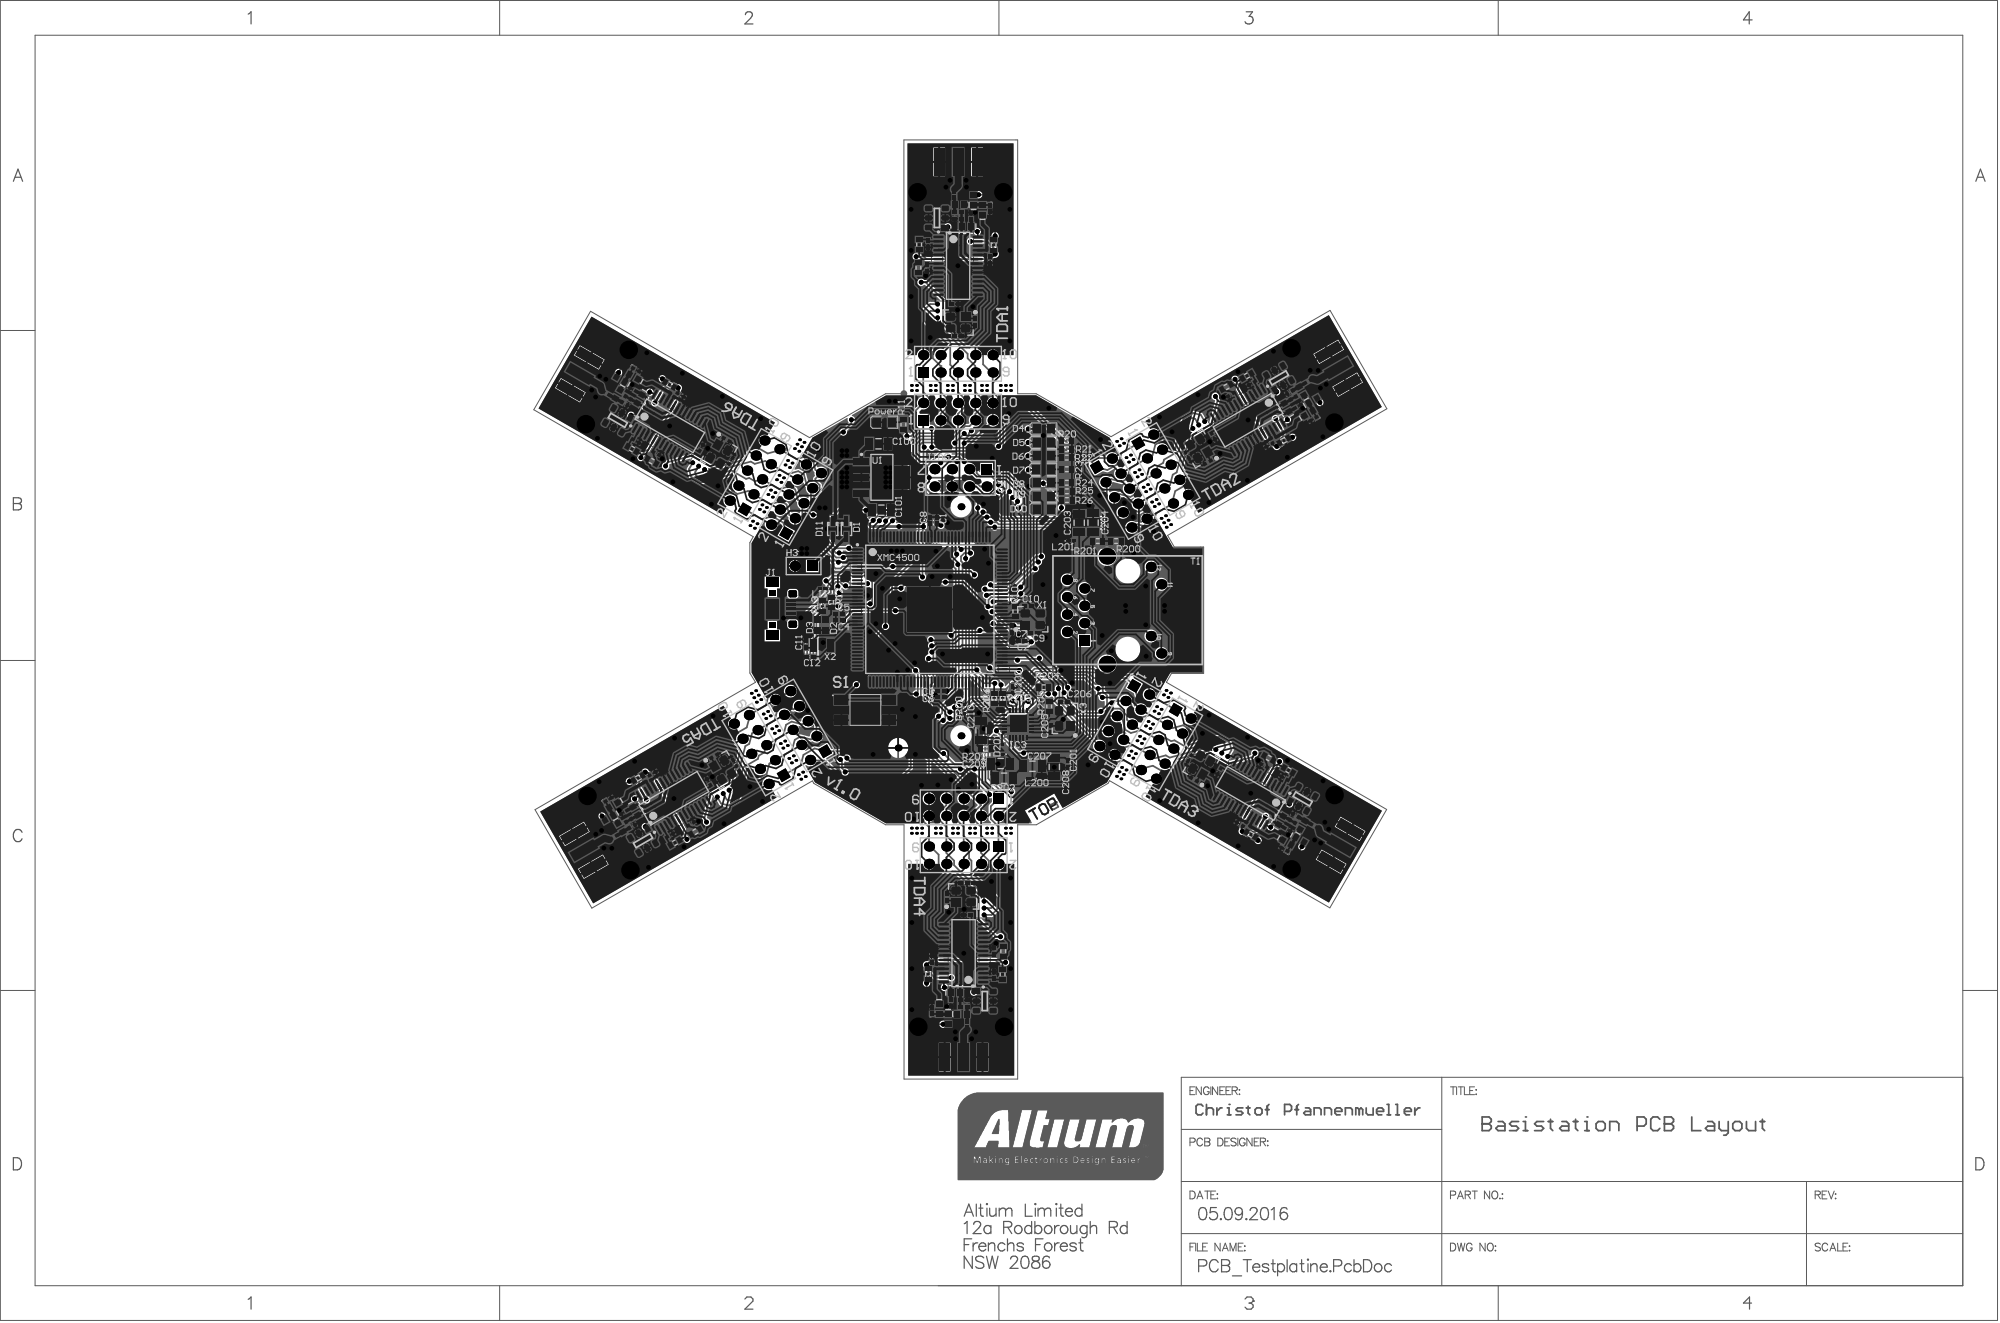
[picture p116: page 1]
