pfanchri/Bachelorarbeit/Latex/Bachelorarbeit/Abbildungen/Aufnahmen/SmartPDF/TDA-sma_rev2.pdf

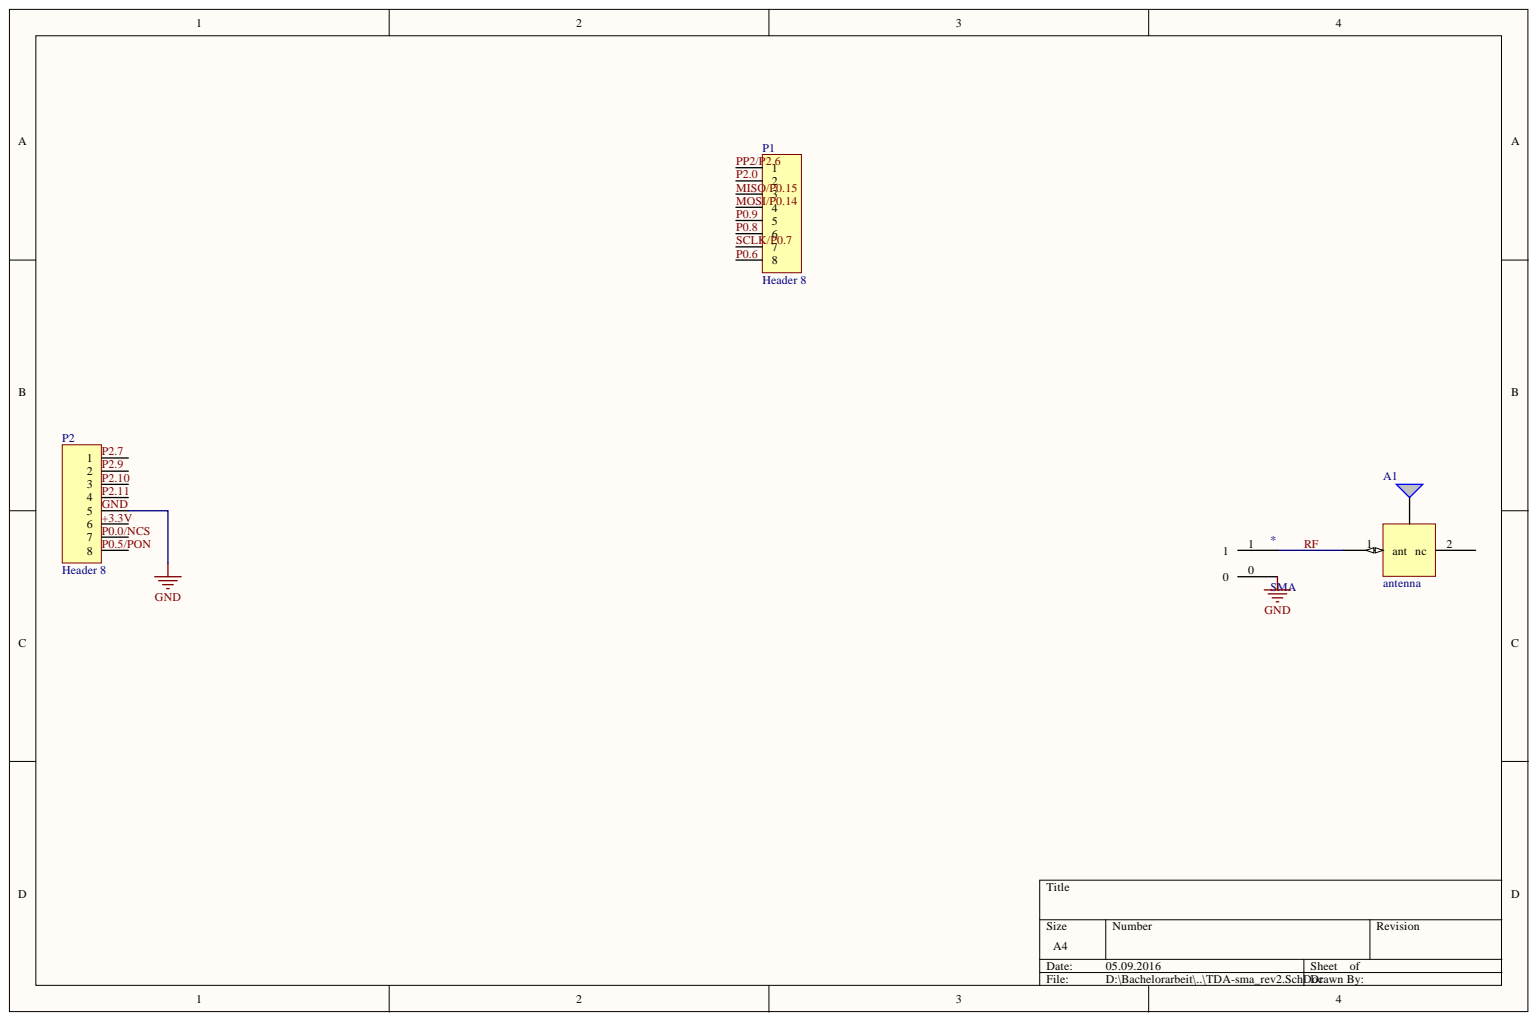
[picture p117: page 1]

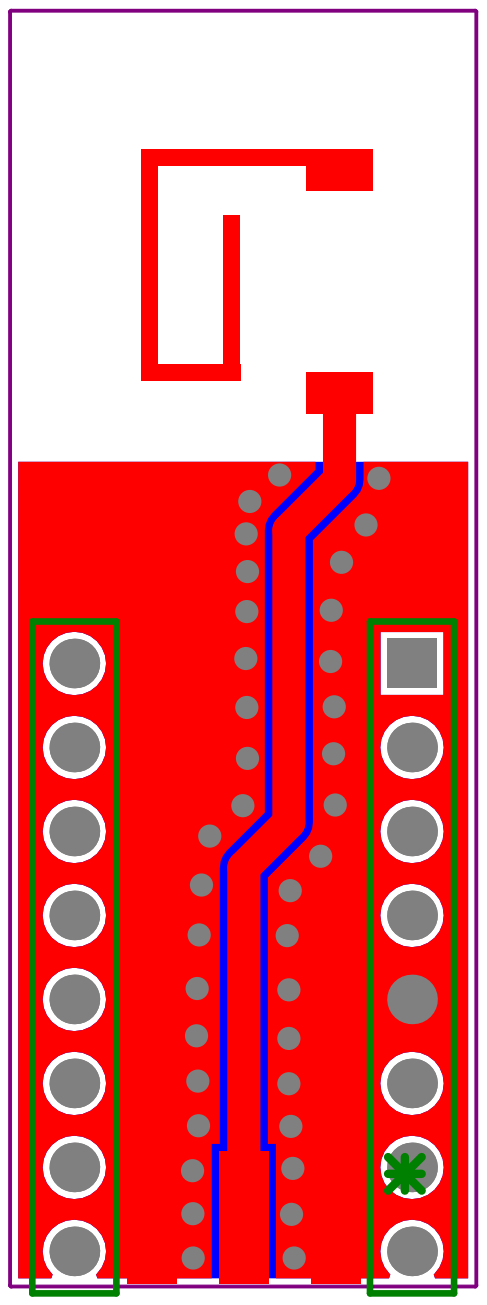
[picture p118: page 2]
