pfanchri/Bachelorarbeit/Dave/Basisstation/Testprojekt/GPIO.h

#ifndef __GPIO_H__
#define __GPIO_H__

/* Generated automatically for XMC4500_QFP144 */

#include <XMC4500.h>

#define INPUT           0x00U
#define INPUT_PD        0x08U
#define INPUT_PU        0x10U
#define INPUT_PPS       0x18U
#define INPUT_INV       0x20U
#define INPUT_INV_PD    0x28U
#define INPUT_INV_PU    0x30U
#define INPUT_INV_PPS   0x38U
#define OUTPUT_PP_GP    0x80U
#define OUTPUT_PP_AF1   0x88U
#define OUTPUT_PP_AF2   0x90U
#define OUTPUT_PP_AF3   0x98U
#define OUTPUT_PP_AF4   0xA0U
#define OUTPUT_OD_GP    0xC0U
#define OUTPUT_OD_AF1   0xC8U
#define OUTPUT_OD_AF2   0xD0U
#define OUTPUT_OD_AF3   0xD8U
#define OUTPUT_OD_AF4   0XE0U

#define WEAK            0x7UL
#define MEDIUM          0x4UL
#define STRONG          0x2UL
#define VERYSTRONG      0x0UL

#define SOFTWARE        0x0UL
#define HW0             0x1UL
#define HW1             0x2UL

__STATIC_INLINE void P0_0_set_mode(uint8_t mode){
    PORT0->IOCR0 &= ~0x000000f8UL;
    PORT0->IOCR0 |= mode << 0;
}

__STATIC_INLINE void P0_0_set_driver_strength(uint8_t strength){
    PORT0->PDR0 &= ~0x00000007UL;
    PORT0->PDR0 |= strength << 0;
}

__STATIC_INLINE void P0_0_set_hwsel(uint32_t config){
    PORT0->HWSEL &= ~0x00000003UL;
    PORT0->HWSEL |= config << 0;
}

__STATIC_INLINE void P0_0_set(void){
    PORT0->OMR = 0x00000001UL;
}

__STATIC_INLINE void P0_0_reset(void){
    PORT0->OMR = 0x00010000UL;
}

__STATIC_INLINE void P0_0_toggle(void){
    PORT0->OMR = 0x00010001UL;
}

__STATIC_INLINE uint32_t P0_0_read(void){
    return(PORT0->IN & 0x00000001UL);
}

__STATIC_INLINE void P0_1_set_mode(uint8_t mode){
    PORT0->IOCR0 &= ~0x0000f800UL;
    PORT0->IOCR0 |= mode << 8;
}

__STATIC_INLINE void P0_1_set_driver_strength(uint8_t strength){
    PORT0->PDR0 &= ~0x00000070UL;
    PORT0->PDR0 |= strength << 4;
}

__STATIC_INLINE void P0_1_set_hwsel(uint32_t config){
    PORT0->HWSEL &= ~0x0000000cUL;
    PORT0->HWSEL |= config << 2;
}

__STATIC_INLINE void P0_1_set(void){
    PORT0->OMR = 0x00000002UL;
}

__STATIC_INLINE void P0_1_reset(void){
    PORT0->OMR = 0x00020000UL;
}

__STATIC_INLINE void P0_1_toggle(void){
    PORT0->OMR = 0x00020002UL;
}

__STATIC_INLINE uint32_t P0_1_read(void){
    return(PORT0->IN & 0x00000002UL);
}

__STATIC_INLINE void P0_2_set_mode(uint8_t mode){
    PORT0->IOCR0 &= ~0x00f80000UL;
    PORT0->IOCR0 |= mode << 16;
}

__STATIC_INLINE void P0_2_set_driver_strength(uint8_t strength){
    PORT0->PDR0 &= ~0x00000700UL;
    PORT0->PDR0 |= strength << 8;
}

__STATIC_INLINE void P0_2_set_hwsel(uint32_t config){
    PORT0->HWSEL &= ~0x00000030UL;
    PORT0->HWSEL |= config << 4;
}

__STATIC_INLINE void P0_2_set(void){
    PORT0->OMR = 0x00000004UL;
}

__STATIC_INLINE void P0_2_reset(void){
    PORT0->OMR = 0x00040000UL;
}

__STATIC_INLINE void P0_2_toggle(void){
    PORT0->OMR = 0x00040004UL;
}

__STATIC_INLINE uint32_t P0_2_read(void){
    return(PORT0->IN & 0x00000004UL);
}

__STATIC_INLINE void P0_3_set_mode(uint8_t mode){
    PORT0->IOCR0 &= ~0xf8000000UL;
    PORT0->IOCR0 |= mode << 24;
}

__STATIC_INLINE void P0_3_set_driver_strength(uint8_t strength){
    PORT0->PDR0 &= ~0x00007000UL;
    PORT0->PDR0 |= strength << 12;
}

__STATIC_INLINE void P0_3_set_hwsel(uint32_t config){
    PORT0->HWSEL &= ~0x000000c0UL;
    PORT0->HWSEL |= config << 6;
}

__STATIC_INLINE void P0_3_set(void){
    PORT0->OMR = 0x00000008UL;
}

__STATIC_INLINE void P0_3_reset(void){
    PORT0->OMR = 0x00080000UL;
}

__STATIC_INLINE void P0_3_toggle(void){
    PORT0->OMR = 0x00080008UL;
}

__STATIC_INLINE uint32_t P0_3_read(void){
    return(PORT0->IN & 0x00000008UL);
}

__STATIC_INLINE void P0_4_set_mode(uint8_t mode){
    PORT0->IOCR4 &= ~0x000000f8UL;
    PORT0->IOCR4 |= mode << 0;
}

__STATIC_INLINE void P0_4_set_driver_strength(uint8_t strength){
    PORT0->PDR0 &= ~0x00070000UL;
    PORT0->PDR0 |= strength << 16;
}

__STATIC_INLINE void P0_4_set_hwsel(uint32_t config){
    PORT0->HWSEL &= ~0x00000300UL;
    PORT0->HWSEL |= config << 8;
}

__STATIC_INLINE void P0_4_set(void){
    PORT0->OMR = 0x00000010UL;
}

__STATIC_INLINE void P0_4_reset(void){
    PORT0->OMR = 0x00100000UL;
}

__STATIC_INLINE void P0_4_toggle(void){
    PORT0->OMR = 0x00100010UL;
}

__STATIC_INLINE uint32_t P0_4_read(void){
    return(PORT0->IN & 0x00000010UL);
}

__STATIC_INLINE void P0_5_set_mode(uint8_t mode){
    PORT0->IOCR4 &= ~0x0000f800UL;
    PORT0->IOCR4 |= mode << 8;
}

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
}

__STATIC_INLINE void P15_15_enable_digital(void){
    PORT15->PDISC &= ~0x00008000UL;
}

__STATIC_INLINE void P15_15_disable_digital(void){
    PORT15->PDISC |= 0x00008000UL;
}

__STATIC_INLINE uint32_t P15_15_read(void){
    return(PORT15->IN & 0x00008000UL);
}

#endif
