pfanchri/Bachelorarbeit/Dave/Basisstation/USBLIB_GENERICHID_XMC45/GenericHID.c

/*
             LUFA Library
     Copyright (C) Dean Camera, 2014.

  dean [at] fourwalledcubicle [dot] com
           www.lufa-lib.org
*/

/*
  Copyright 2014  Dean Camera (dean [at] fourwalledcubicle [dot] com)

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
  The author disclaims all warranties with regard to this
  software, including all implied warranties of merchantability
  and fitness.  In no event shall the author be liable for any
  special, indirect or consequential damages or any damages
  whatsoever resulting from loss of use, data or profits, whether
  in an action of contract, negligence or other tortious action,
  arising out of or in connection with the use or performance of
  this software.
*/

/** \file
 *
 *  Main source file for the GenericHID demo. This file contains the main tasks of
 *  the demo and is responsible for the initial application hardware configuration.
 */

#include "GenericHID.h"

/** Buffer to hold the previously generated HID report, for comparison purposes inside the HID class driver. */
static uint8_t PrevHIDReportBuffer[GENERIC_REPORT_SIZE];

/** LUFA HID Class driver interface configuration and state information. This structure is
 *  passed to all HID Class driver functions, so that multiple instances of the same class
 *  within a device can be differentiated from one another.
 */
USB_ClassInfo_HID_Device_t Generic_HID_Interface =
	{
		.Config =
			{
				.InterfaceNumber              = INTERFACE_ID_GenericHID,
				.ReportINEndpoint             =
					{
						.Address              = GENERIC_IN_EPADDR,
						.Size                 = GENERIC_REPORT_SIZE,
						.Banks                = 1,
					},
				.PrevReportINBuffer           = PrevHIDReportBuffer,
				.PrevReportINBufferSize       = sizeof(PrevHIDReportBuffer),
			},
	};


uint8_t buffer[GENERIC_REPORT_SIZE];

/* USB runtime structure*/
XMC_USBD_t USB_runtime =
{
  .usbd = USB0,
  .usbd_max_num_eps = XMC_USBD_MAX_NUM_EPS_6,
  .usbd_transfer_mode = XMC_USBD_USE_FIFO,
  .cb_xmc_device_event = USBD_SignalDeviceEventHandler,
  .cb_endpoint_event = USBD_SignalEndpointEvent_Handler

};

/*******************************************************************************
**                     Public Function Definitions                            **
*******************************************************************************/

void USB0_0_IRQHandler(void)
{
  XMC_USBD_IRQHandler(&USB_runtime);

}

/*The function initializes the USB core layer and register call backs. */
void USB_Init(void)
{
  USBD_Initialize(&USB_runtime);

  /* Interrupts configuration*/
  NVIC_SetPriority(USB0_0_IRQn, NVIC_EncodePriority(NVIC_GetPriorityGrouping(), 63, 0));
  NVIC_ClearPendingIRQ(USB0_0_IRQn);
  NVIC_EnableIRQ(USB0_0_IRQn);

  /* USB Connection*/
  USB_Attach();

}

/** Event handler for the library USB Connection event. */
void EVENT_USB_Device_(void)
{
}
/** Event handler for the library USB Connection event. */
void EVENT_USB_Device_Connect(void)
{
}

/** Event handler for the library USB Disconnection event. */
void EVENT_USB_Device_Reset(void)
{
  if(device.IsConfigured)
  {
    USB_Init();
    device.IsConfigured=0;
  }
}

/** Event handler for the library USB Configuration Changed event. */
void EVENT_USB_Device_ConfigurationChanged(void)
{
  bool ConfigSuccess = true;

  USBD_SetEndpointBuffer(GENERIC_IN_EPADDR, buffer, GENERIC_REPORT_SIZE);

  ConfigSuccess &= HID_Device_ConfigureEndpoints(&Generic_HID_Interface);

  device.IsConfigured = ConfigSuccess;
}

/** Event handler for the library USB Control Request reception event. */
void EVENT_USB_Device_ControlRequest(void)
{
	HID_Device_ProcessControlRequest(&Generic_HID_Interface);
}


/** HID class driver callback function for the creation of HID reports to the host.
 *
 *  \param[in]     HIDInterfaceInfo  Pointer to the HID class interface configuration structure being referenced
 *  \param[in,out] ReportID    Report ID requested by the host if non-zero, otherwise callback should set to the generated report ID
 *  \param[in]     ReportType  Type of the report to create, either HID_REPORT_ITEM_In or HID_REPORT_ITEM_Feature
 *  \param[out]    ReportData  Pointer to a buffer where the created report should be stored
 *  \param[out]    ReportSize  Number of bytes written in the report (or zero if no report is to be sent)
 *
 *  \return Boolean \c true to force the sending of the report, \c false to let the library determine if it needs to be sent
 */
bool CALLBACK_HID_Device_CreateHIDReport(USB_ClassInfo_HID_Device_t* const HIDInterfaceInfo,
                                         uint8_t* const ReportID,
                                         const uint8_t ReportType,
                                         void* ReportData,
                                         uint16_t* const ReportSize)
{

	uint8_t* Data       = (uint8_t*)ReportData;

	Data[0] = (uint8_t)XMC_GPIO_GetInput(LED1);
	Data[1] = (uint8_t)XMC_GPIO_GetInput(LED2);
	*ReportSize = GENERIC_REPORT_SIZE;

	return false;
}

/** HID class driver callback function for the processing of HID reports from the host.
 *
 *  \param[in] HIDInterfaceInfo  Pointer to the HID class interface configuration structure being referenced
 *  \param[in] ReportID    Report ID of the received report from the host
 *  \param[in] ReportType  The type of report that the host has sent, either HID_REPORT_ITEM_Out or HID_REPORT_ITEM_Feature
 *  \param[in] ReportData  Pointer to a buffer where the received report has been stored
 *  \param[in] ReportSize  Size in bytes of the received HID report
 */
void CALLBACK_HID_Device_ProcessHIDReport(USB_ClassInfo_HID_Device_t* const HIDInterfaceInfo,
                                          const uint8_t ReportID,
                                          const uint8_t ReportType,
                                          const void* ReportData,
                                          const uint16_t ReportSize)
{
	uint8_t* Data       = (uint8_t*)ReportData;
	Data[0] ? XMC_GPIO_SetOutputHigh(LED1) : XMC_GPIO_SetOutputLow(LED1);
  Data[1] ? XMC_GPIO_SetOutputHigh(LED2) : XMC_GPIO_SetOutputLow(LED2);
}

bool CALLBACK_HIDParser_FilterHIDReportItem(HID_ReportItem_t* const CurrentItem)
{
  return true;
}
