pfanchri/Bachelorarbeit/Dave/Basisstation/TDA_XMC4500_PMA_testtrans/global.h

/*
 * global.h
 *
 *  Created on: 28.01.2015
 *      Author: pflaum
 */


#include <XMC4500.h>
#include "DAVE/generated/DAVE.h"
#include "portmakros.h"
#include "xmc_gpio.h"
#include "xmc_eru.h"
#include "xmc_spi.h"
#include "xmc_usic.h"
#include "main.h"
#include "tda5340.h"
#include "spi.h"
#include "relax_kit.h"
#include "crcchk.h"
#include "num_string_conversion.h"
