pfanchri/Bachelorarbeit/Dave/Basisstation/Basisstation/Led.h

/*
 * Led.h
 *
 *  Created on: Jun 22, 2016
 *      Author: christofpfannenmulle
 */

#ifndef LED_H_
#define LED_H_

//LED on/off functions


void led_on(uint8_t led);

void led_off(uint8_t led);


#endif /* LED_H_ */
