pfanchri/Bachelorarbeit/Dave/Basisstation/Basisstation/TDA.h

/*
 * TDA.h
 *
 *  Created on: Jun 22, 2016
 *      Author: christofpfannenmulle
 */

#ifndef TDA_H_
#define TDA_H_



//TDA function definitions


void set_TDA_status(uint8_t TDA, uint8_t status);




#endif /* TDA_H_ */
